Benedict-Bsl/SmartCap/Documents/US10445472.pdf

### US010445472B2

# ( 12 ) United States Patent

LeBrun

## ( 10 ) Patent No . : US 10 , 445 , 472 B2 ( 45 ) Date of Patent : Oct . 15 , 2019

### ( 54 ) SYSTEM AND METHOD FOR MONITORING

PILL CONTAINER ACTIVITY

( 56 ) | References Cited
U . S . PATENT DOCUMENTS
( 71 ) Applicant : PILLSY , INC . , Seattle , WA ( US ) | 5 , 751 , 661 A *

## ( 72 ) Inventor : Jeffrey R . LeBrun , Seattle , WA ( US )

## ( 73 ) Assignee : Pillsy , Inc . , Seattle , WA ( US )

6 , 518 , 523 B1
7 , 081 , 807 B2
7 , 446 , 272 B2
7 , 928 , 835 B1
8 , 092 , 224 B2
8 , 116 , 907 B2
5 / 1998 Walters | A61J 7 / 0409
221 / 2
2 / 2003 Chou
7 / 2006 Lai
11 / 2008 Chou
4 / 2011 Jovanov et al . 1 / 2012 Walker et al . 2 / 2012 Hyde et al .

( Continued )

( * ) Notice : Subject to any disclaimer , the term of this
patent is extended or adjusted under 35
U . S . C . 154 ( b ) by 742 days .
( 21 ) Appl . No . : 14 / 824 , 231 | FOREIGN PATENT DOCUMENTS
( 22 ) Filed : Aug . 12 , 2015 | WO
WO
2010078558 AL | 7 / 2010
2013120029 AL | 8 / 2013
( Continued ) ( 65 ) | Prior Publication Data
US 2016 / 0048657 A1 Feb . 18 , 2016 | OTHER PUBLICATIONS

## Related U . S . Application Data

( 60 ) Provisional application No . 62 / 036 , 272 , filed on Aug . 12 , 2014 .

PCT / US2018 / 040150 search report published WO2019 / 006212 dated Mar . 1 , 2019 .

### Primary Examiner — Hiep V Nguyen

( 51 ) | ( 74 ) Attorney , Agent , or Firm - Carrie M . Stroup

( 52 )

Int . Cl . G06F 19 / 00 | ( 2018 . 01 )
B65D 51 / 24 | ( 2006 . 01 )
B650 50 / 04 | ( 2006 . 01 )
A61J 1 / 14 | ( 2006 . 01 )
U . S . CI . CPC . . | G06F 19 / 3462 ( 2013 . 01 ) ; A61 ) 1 / 1412
( 2013 . 01 ) ; B650 50 / 043 ( 2013 . 01 ) ; B65D 51 / 24 ( 2013 . 01 ) ; B65D 51 / 248 ( 2013 . 01 ) ; GO6F 19 / 3418 ( 2013 . 01 ) ; A61J 2200 / 30 ( 2013 . 01 ) ; A61J 2200 / 74 ( 2013 . 01 ) Field of Classification Search
CPC | GO6F 19 / 3462 ; G06F 19 / 3456 ; A61J
1 / 1412 ; A61J 7 / 0472 ; A61J 7 / 0436 ; B65D 51 / 248 ; B65D 2101 / 0015 ; B65D 83 / 0409
USPC | | | 705 / 2
See application file for complete search history .
( 57 ) | ABSTRACT
A cap for a medication container includes a housing with a top portion and a bottom portion . The top and bottom portions together define a cavity therebetween . A sliding plate is disposed in the cavity adjacent the bottom portion . A microcontroller with a contact sensor is disposed in the

cavity between the top portion and the sliding plate . The
sliding plate is configured to slide toward and activate the
contact sensor where the cap is secured to the medication container in a closed state . The sliding plate is also config ured to slide away from and not activate the contact sensor where the cap is removed from the medication container in an open state .

( 58 )

21 Claims , 12 Drawing Sheets

501
Smart pill cap
Sensors | Micro
| controller
Wireless radio | Memory

Power
source | PCB

508
Remote computer
511 Wireless radio Memory

512 Power

source

Display
screen

User input interface ( touch screen or keyboard )

## US 10 , 445 , 472 B2

### Page 2

( 56 ) | | | References Cited
U . S . PATENT DOCUMENTS
8 , 362 , 914 B2 | 1 / 2013 Hyde et al . 8 , 666 , 926 B13 / 2014 Nease et al . 8 , 754 , 769 B2 | 6 / 2014 Stein et al . 2001 / 0028308 Al * 10 / 2001 De La Huerga . . A61M 5 / 14212

340 / 573 . 1
2002 / 0126585 Al * 9 / 2002 Osberg | A61J 7 / 0472
368 / 107
2003 / 0063522 AL | | | 4 / 2003 Sagar
2003 / 0069540 Al | 4 / 2003 Fowler et al . 2005 / 0047114 Al | 3 / 2005 Harrell et al .
2007 / 0171627 Al | | | 7 / 2007 Hsu
2007 / 0201220 A1 | | | 8 / 2007 Ulicny
2009 / 0134181 A1 | 5 / 2009 Wachman et al . 2010 / 0001812 A1 | 1 / 2010 Kausch
2010 / 0270257 Al 10 / 2010 Wachman et al . 2012 / 0029693 AL | 2 / 2012 Bear et al . 2014 / 0052468 A1 | 2 / 2014 Burrows et al . 2014 / 0108031 A1 | 4 / 2014 Ferrara
2014 / 0240094 AL | | | 8 / 2014 Stein et al . 2014 / 0300273 Al 10 / 2014 LeBrun et al .

FOREIGN PATENT DOCUMENTS
WO
WO
WO

2013127564 AL
2013158352 A1
WO2019006212 A1
| | | 9 / 2013
| | | 10 / 2013
| | | 1 / 2019
* cited by examiner

U . S . Patent | Oct . 15 , 2019 Sheet 1 of 12 | US 10 , 445 , 472 B2

103
101 | w | 104

105

106

102

# FIG . 1

U . S . Patent | Oct . 15 , 2019 | Sheet 2 of 12 | US 10 , 445 , 472 B2

101 .

Yrvacy | NO
wth | - 201

wa

Benim 203 -
IT S

AN
ITEMTIDUR Det ETT
am

208
209
207 _
01 | 202 4 + | 4 | + 4 | + 4 | + 4 + 4 *

AAL
? . . | XSATTA LE
written * * * * * * * * | : 11 * * * | ranti | F
. * | 206
211 | he

t

Whether

# FIG . 2

U . S . Patent | Oct . 15 , 2019 | Sheet 3 of 12 | US 10 , 445 , 472 B2

301

# FIG . 3A

302

w

ww | wwwwwwww
303 / | FIG . 3B

atent | Oct . 15 , 2019 | Sheet 4 of 12 | US 10 , 445 , 472 B2

Os 302
301 -

303

# FIG . 4

U . S . Patent | Oct . 15 , 2019 | Sheet 5 of 12 | US 10 , 445 , 472 B2

501

# \ Smart pill cap

Sensors | Micro
| controller

### Wireless

## radio Memory

WW

## Power

source

PCB

508

# Remote computer

- 511

### Wireless

## radio Memory

512
Power source | Display
| screen

### User input interface ( touch

## screen or keyboard )

# FIG . 5

U . S . Patent | Oct . 15 , 2019 Sheet 6 of 12 | US 10 , 445 , 472 B2

607

# Smart Pill Cap

# Additional remote

# computers ( e . g . caregiver smartphones or

# laptops )

603

# First Remote Computer

# ( e . g . smartphone )

# Internet

606 604
602

# Remote Servers

FIG . 6 | Storage

## ( databases )

## Processors

## ( controllers ) 605 -

atent | Oct . 15 , 2019 | Sheet 7 of 12 | US 10 , 445 , 472 B2

707

| 701
Smart Pill Cap | First remote computer ( e . g . User ' s computer , tablet or smartphone )

703

# Gateway

( e . g . cellular hub ) | Internet
708 | 704 | 706

# Servers Second remote

# computer ( operated by

# somebody other than

the user ) | Storage
| ( databases )

## Processors

### ( controllers ) 705

## FIG . 7

U . S . Patent atent | Oct . 15 , 2019 | Sheet 8 of 12 | US 10 , 445 , 472 B2

807

1801 Smart Pill Cap | User ' s smartphone

803

FIG . 8 | Internet

802
806

# Servers Caregiver or provider

## remote computers

( smartphones , laptops , etc . ) | Storage
| ( databases ) Processors

## ( controllers ) 805

atent | Oct . 15 , 2019 | Sheet 9 of 12 | US 10 , 445 , 472 B2
901 | 902

# PUBLIC GATEWAY

# Load balancing layer

App layer | Bastion layer

904

# PRIVATE GATEWAY

Database layer | .

_ W
905 | FIG . 9
906

tent | Oct . 15 , 2019 | Sheet 10 of 12 | US 10 , 445 , 472 B2
1001 | | Standby
1002 | Microcontroller on container receives sensor data indicating open / closed state
1003 | Sensor activity is recorded into memory with timestamp
1004 | Microcontroller sensor data log to smartphone via Bluetooth Low Energy , if they are paired or bonded and if there is a connection
1005 | Smartphone application sends pre - programmed reminders , unless the container activity is recorded and sent prior to the reminder time
1006 | Smartphone sends sensor data log to servers via cellular connection

# FIG . 10

U . S . Patent | Oct . 15 , 2019 | Sheet 11 of 12 | US 10 , 445 , 472 B2
1101 | User initiates refill action through sensor or switch located on the smart pill cap
1102 | Microcontroller on the smart pill cap interprets the sensed action to be a pill refill action
1103 | Microcontroller on the smart pill cap wirelessly sends a refill instruction to the smartphone or tablet application
1104 | Smartphone or tablet application sends a refill message to the web application API endpoint
1105 | Web application processes request and sends a refill message to the pharmacy ' s API endpoint

## 1106 _ Pharmacy API returns confirmation of successful refill to the

| web application API endpoint

1107 11077 Web application sends message to user ' s smartphone , confirming the successful refill action to the user ( optional )

# FIG . 11

nt | Oct . 15 , 2019 | Sheet 12 of 12 | US 10 , 445 , 472 B2

1205 000000000 1202

1203

1204 1204
. 1201

# FIG . 12

## US 10 , 445 , 472 B2

SYSTEM AND METHOD FOR MONITORING | | prescribed medications , and can transmit this information to
PILL CONTAINER ACTIVITY | | authorized individuals who can further assist patients in
managing their conditions . CROSS - REFERENCE TO RELATED | In one embodiment , a cap for a medication container
APPLICATIONS | | 5 includes a housing with a top portion and a bottom portion . The top portion and the bottom portion together define a
This application claims the benefit of U . S . Provisional | cavity therebetween . A sliding plate is disposed in the cavity Application No . 62 / 036 , 272 , filed on Aug . 12 , 2014 . The | adjacent the bottom portion . A microcontroller with a switch
entire disclosure of the above application is hereby incor | type contact sensor is disposed in the cavity between the top porated herein by reference . | portion and the sliding plate . The sliding plate is configured
to slide toward and activate the contact sensor where the cap FIELD | is secured to the medication container in a closed state . The
sliding plate is configured to slide away from and not The present disclosure relates to systems and methods for | activate the contact sensor where the cap is removed from increasing patient adherence to medication and nutrition 15 the medication container in an open state . regimens and , more particularly , to a smart pill cap for use
with standard prescription medicine containers . | | In another embodiment , a system for promoting adher
| | ence to a regimen by a patient includes the cap , and a first
BACKGROUND | | remote computer having a memory and a display . The first
| | 20 remote computer is in electronic communication with the
The statements in this section merely provide background | | cap . The first remote computer is configured to show on the
information related to the present disclosure and may not | | display information corresponding with the sliding plate
constitute prior art . | | pressing against and activating the contact sensor . The
Many people take medications , vitamins , and nutritional | | information is indicative of an opening and a closing of the
supplements on a regular basis as a way of life . However , a 25 medication container over time . common problem is that people forget to take their medi - | | In a further embodiment , a method for promoting adher
cations or other pills on a regular basis , or as they are | | ence to a regimen by a patient , includes the steps of
prescribed . Experts have estimated average medication | | providing the system with the cap and the first remote
adherence rates of 50 % to 60 % . According to the National | | computer , and maintaining the cap in a standby mode until
Community Pharmacists Association , this costs about 125 , 30 the cap senses a change in state from one of the open state
000 lives and $ 290 billion in the United States alone . While | | and the closed state . The cap is then caused to enter an active
there are several factors behind non - adherence , several mode for a predefined period of time . The cap is configured
studies have indicated that forgetfulness is a driving factor . | | to record the information from the contact sensor while in
In light of these facts , there is a continuing need for a cost | | the active mode . The microcontroller of the cap then creates
effective system and method of promoting patient adherence 35 a sensor data log of the information , and communicates the
to medication and nutrition regimens . Desirably , increasing | sensor data log to the first remote computer . rates of patient adherence will improve patient outcomes . | Further areas of applicability will become apparent from
saving patient lives and reducing preventative costs borne by | | the description provided herein . It should be understood that
the healthcare system and society . | | the description and specific examples are intended for pur 40 poses of illustration only and are not intended to limit the
SUMMARY | | scope of the present disclosure .
In concordance with the instant disclosure , a cost effective | | DRAWINGS
system and method of promoting patient adherence to medi
cation and nutrition regimens , which improves patient out - 45 | | The above , as well as other advantages of the present
comes , saves patient lives , and reduces preventative costs | | disclosure will become readily apparent to those skilled in
borne by the healthcare system and society , is surprisingly | | the art from the following detailed description when con
discovered . | | sidered in light of the accompanying drawings , in which :
The present disclosure provides a device and method to | | FIG . 1 is a perspective view of an assembly including a
assist people with managing either a ) their medications or b ) 50 smart pill cap attached to a prescription pill container , the medications of somebody whom they are caring for . In | | according to one embodiment of the disclosure ;
one embodiment of the disclosure , these medications are | | FIG . 2 is an exploded side elevational view of the
placed into a standard prescription pill container that is | | assembly of FIG . 1 ;
labeled and filled by a pharmacist . The standard prescription | | FIG . 3A is an enlarged side elevational view of the
pill vial has a smart pill cap . Information about the medi - 55 threaded smart pill cap of FIG . 1 , shown without the
cation , including the medication schedule , are programmed | | prescription pill container ;
into a software application that connects to the smart pill cap | | FIG . 3B is an enlarged bottom perspective view of the
attached to the pill container . The smart pill cap detects | | threaded smart pill cap shown in FIG . 3A ;
interactions with the pill container , including when it is | | FIG . 4 is an enlarged bottom perspective view of a smart
opened and closed , and sends this information wirelessly to 60 pill cap according to another embodiment of the disclosure , a remote computer . The remote computer can remind the | | wherein the smart pill cap is childproof ;
user to take their medications when they forget . The remote | | FIG . 5 is a schematic diagram illustrating an example
computer can also send the user ' s medication adherence data | | communication relationship between the smart pill cap and
to a remote server , where it may be shared with family | | pill container of FIG . 1 and a smartphone application ;
members or their healthcare providers . The system can 65 | | FIG . 6 is a schematic diagram illustrating an example of
remind patients when to take their medications , provide | | one network architecture between the smart pill cap , and
information about the medications , monitor adherence to the | | remote servers that store the web application ;

## US 10 , 445 , 472 B2

15

FIG . 7 is a schematic diagram illustrating an example | | | board 203 . Although the top portion 201 and the bottom
network architecture where the smart pill cap sends a | portion 202 are described further herein as being distinct top wireless signal to a cellular gateway , which relays medica - and bottom pieces , separately formed and subsequently tion adherence information to remote servers through the | attached to one another , it should be appreciated that the top Internet , which then routes medication adherence data to 5 portion 201 and the bottom portion 202 may also be formed
devices used by the patient and members of their care team ; | integrally as a single or unitary one - piece body , as desired . FIG . 8 is a schematic diagram illustrating an example | The printed circuit board contains a switch type sensor network architecture according to another embodiment of | 204 , a wireless radio , memory , a speaker , and other elec
the disclosure ; | tronic components . A sliding plate 204 is also encased by the FIG . 9 is a particular embodiment of a data structure for 10 top piece 201 of the housing and the bottom piece 202 of the preserving securing within the remote servers ; | housing . The sliding plate 204 presses down the switch type FIG . 10 is a flow diagram illustrating a method for sharing | sensor 205 when the pill container 211 is attached to the information from the smart pill cap to a remote server
through an intermediary remote computer , according to one | | | smart pill cap 101 by tightening the threads 206 on the
5 container with the threads 207 internal to the smart pill cap . embodiment of the disclosure ;
FIG . 11 is a flow diagram illustrating a method for | | | A silicone band 208 may be placed on the outside of the
initiating a prescription refill through the smart pill cap . | | | assembled smart pill cap 101 . The silicone band 208 may fit
according to another embodiment of the disclosure ; and | | | into a groove 209 that permits a flush fitting within the side
FIG . 12 is schematic illustration of a smart pill cap that is | | | of the smart pill cap 101 . The silicone band 208 may cover
capable of sensing and calculating the weight of the contents 20 up screw holes 210 that are used to attach the top piece 201
of the attached pill vial . | | | and the bottom piece 202 of the smart pill cap 101 . FIGS . 3A and 3B illustrate alternative views of the smart
DETAILED DESCRIPTION | | | pill cap 101 that is designed to fit with a “ 1 - click ” pill container . A thread 302 secures the smart pill cap to the pill The following description is merely exemplary in nature 25 container , with a rectangular block of plastic 303 that is
and is not intended to limit the present disclosure , applica - | | | incorporated into the smart pill cap 301 securing the 1 - click
tion , or uses . It should be understood that throughout the | | | mechanism that is built into the pill container . This ensures
drawings , corresponding reference numerals indicate like or | | | that the smart pill cap 301 remains securely fastened to the
corresponding parts and features . | | | pill cap until the user presses the 1 - click release mechanism
FIG . 1 illustrates a smart pill cap 101 that is capable of 30 on the container and twists the smart pill cap 301 to remove
being removably coupled to a pill container 102 , such as a | it . vial . The smart pill cap 101 contains an internal switch - type | FIG . 4 illustrates a further alternative version of the smart
contact sensor for detecting whether or not it is coupled to | | | pill cap 101 that is designed to integrate with a childproof
the container 102 , thereby detecting whether the container is | | | pill container . In this embodiment , rectangular blocks of
opened or closed . This information is stored in local memory 35 plastic 301 are integrated to the smart pill cap that fit with
that is also internal to the cap . As used herein , the term | | | plastic “ hooks ” that are included on the external portion of
“ memory ” may include a non - transitory and tangible com - | | | a childproof pill container when the smart pill cap is pushed
puter - readable storage medium , on which databases and | | | onto the childproof pill container . The sliding plate 302
processor - executable software code may be embodied . The | | | selectively activates , for example , by pressing against , the
smart pill cap 101 transmits the information to an external 40 switch type contact sensor when the container is attached to
computer or gateway via a wireless radio connection . Audio | | | the smart pill cap . A ridge 303 is included on the sliding plate
reminders may be emitted from a speaker internal to the | | | 302 in order to maintain a tight seal with the mouth of the
smart pill cap 101 , which are configured to occur when the | | | pill container .
user does not open the container on a pre - scheduled basis . | | | FIG . 5 illustrates a medication adherence system com
In a particular embodiment , a top plate 103 is incorpo - 45 prising a smart pill cap 501 , also described hereinabove and
rated into the smart pill cap 101 that can be removed in order | | | shown in FIGS . 1 and 2 as reference number 101 , that
to expose a coin cell style battery . A gap 104 between the top | | | transmits information that is sensed by the switch - based
plate 103 and the primary container body 105 permits the top | sensor 502 to a remote computer 508 , such as a smartphone , plate 103 to be removed via a prying action , as well as | tablet computer , or laptop computer , by transmitting infor
permits sound emitted by the internal speaker to be heard by 50 mation digitally from the smart pill cap ' s wireless radio 503
the user . | to the wireless radio contained in the remote computer 508 . A silicone band 106 provides an improved grip on the | The smart pill cap stores data in local memory 506 that is
smart pill cap while concealing a seam between the top and | | | transmitted whenever the smart pill cap 501 and remote
bottom portions of the smart pill cap assembly . The silicone | | | computer 508 are connected and are in range . A power
band 106 may also be colored in a way that the user 55 source 504 such as a lithium or lithium - ion battery is
associates it with the display of one of their medications in | | | contained inside the smart pill cap and components are
the accompanying software of the smart pill cap 101 . | connected via a printed circuit board ( PCB ) 507 . The smart pill cap 101 can be placed on a prescription or | The remote computer receives has the capability to store
over - the - counter pill container in order to track medication | | | data from the smart pill cap in local memory 511 . The
usage and adherence . The container 102 may be filled by a 60 remote computer also contains an onboard power 510
pharmacist , drug manufacturer , drug distributor , or whole - | | | source , such as a lithium ion battery . Most importantly the
sale provider . | | | remote computer serves as the user ' s primary means of
FIG . 2 illustrates a sub - assembly of the smart pill cap 101 | | | viewing data that is collected by the smart pill cap , with the
and integration with the pill container 102 , according to one | | | user of the smart pill cap having the ability to view said data
embodiment of the disclosure . A top portion 201 of the smart 65 on the display screen 512 of the remote computer 512 as
pill cap housing is securely attached to a bottom portion 202 | | | well as to input data that can be sent from the remote
of the smart pill cap housing , encasing a printed circuit | | | computer 508 to the smart pill cap 501 , such as a schedule view

## US 10 , 445 , 472 B2

of times when the user is supposed to take the medications | | | number 101 , sends data directly to remote servers 804
contained by the smart pill cap 501 and the pill container that | | | through a cellular data connection without passing data
it is mated to . | | | through an intermediate hub or remote computer , such as
FIG . 6 illustrates a medication adherence network archi - | | | those that were described in FIG . 6 and FIG . 7 . In this case , tecture comprising the system described in FIG . 5 . The 5 the remote servers 804 may relay data collected by sensors
remote computer 602 sends information received from the | | | in the smart pill cap 801 to the user ' s remote computer , or
smart pill cap 601 , also described hereinabove and shown in | to remote computers operated by people other than the user . FIGS . 1 and 2 as reference number 101 , to a remote server | The cellular connection used in this architecture may be
604 through the Internet 603 . The remote servers having | GSM , CDMA , LTE or another network type . storage 605 and processing capabilities 606 . | 10 | FIG . 9 illustrates an architecture for securely storing data
Data related to the user ' s medication adherence may be | | | collected by the smart pill cap described in FIG . 1 on a
stored in the smart pill cap , the remote computer , and on the | | | remote server . Requests to a first remote server come in
remote server , with data periodically synced across all three | | | through a public gateway 901 , with requests being routed to
locations . Medication adherence data stored on the smart pill | | | a second remote server through the load balancing layer 902 . cap may be deleted after a specified number of events in 15 This helps to ensure maximum responsiveness and uptime
order to free up additional memory , preferably after data is | | | by distributing the computational load among a network of
pushed to the remote computer or remote servers . Informa | | | servers . Requests are routed to the app layer 903 of a web
tion may also be sent from the remote servers to the user ' s | | | application or API that is designed specifically to be com
remote computer . For example , information may be sent to | | | plimentary to the smart pill cap device described in FIG . 1 . the user ' s smartphone related to pricing at various pharma - 20 This app layer 903 can may requests to database layer 906
cies where they can refill their medications . | | | only through a private gateway 905 . By limiting extraction
Optionally , a portion of the data captured by the smart pill | | | of data from the database layer to a small subset of known
cap may be shared from the remote servers to additional | | | servers , this helps to ensure security of the medication
remote computers 607 that are managed by remote caregiv | | | adherence data . All data stored in the server is also encrypted
ers , care managers , family members , or healthcare profes - 25 and servers are kept in locations that are physically secure . sionals ( doctors , nurses , physician ' s assistants , etc . ) . This | | | A bastion layer 904 running on one or more servers receives
sharing is likely to be executed via an application program - | requests from protected areas of the network and is desig ming interface ( API ) that is made available to users that have | nated with specific responsibilities , such as security privi
1 ) received permission from the owner of the smart pill cap | | | leges and access privileges . and first remote computer 2 ) have proven their credentials to 30 FIG . 10 illustrates a method for recording medication
the API through an authentication method , such as OAuth , | | | adherence data into memory located in a smart pill cap and
a known open standard for authorization , or a token - based | | | sending that information to remote servers via a smartphone
authentication method . This capability provides additional | | | intermediary . The smart pill cap will remain in standby
users to see information that can help them to care for the mode 1001 until it senses a change to opened / closed state , user , such as to intervene when the user has deviated from 35 at which point it will enter " active mode ” for a predefined their medication schedule . Moreover , the API enables 3rd | | | period of time . Standby mode may be designed to conserve
party solution providers to write custom software applica | | | power by reducing the advertising interval frequency by the
tions that combine data from the smart pill cap with data | | | wireless radio . Once sensor data is detected 1002 it will be
from other sources . For example , the additional remote | | | recorded into memory 1003 located on the smart pill cap . computers may combine data from the smart pill cap with 40 When the smart pill cap connects to a smartphone that it is
data from a wireless scale or a wireless blood pressure | | | paired to , it sends the data log to a complimentary applica
monitor to determine if the user has a high degree of risk of | | | tion running on the smartphone 1004 . The smartphone is
heart attack due to the user ' s deviation from their prescribed | | | pre - programmed to send medication reminders to the user
medication regimen . | | | unless it receives data from the smart pill container indicat
FIG . 7 illustrates a medication adherence system whereby 45 ing that the smart pill container has been opened within a
the smart pill cap 701 , also described hereinabove and | | | time interval designated to be associated with the scheduled
shown in FIGS . 1 and 2 as reference number 101 , sends data | | | medication event 1005 . The smartphone also sends the
related to a user ' s medication adherence to a wireless hub | | | sensor data log over the Internet using a cellular , WiFi , or
702 that is located within a close proximity ( less than 2000 | other wireless connection 1006 . feet ) that subsequently relays the data to remote servers 704 . 50 | FIG . 11 illustrates a method for initiating a refill of a
The remote servers are able to send the medication adher - | | | prescription medication , vitamin , or over - the - counter medi
ence data transmitted originally from the smart pill cap 701 | cation by interacting directly with the smart pill container . to at least one of the user ' s smartphone 707 or to remote | The user initiates the refill action by initiating the sensor
computers 708 being operated by the user ' s caregiver , | | | located inside of the smart pill cap 1101 using a pre - defined
family member or a healthcare professional . This represents 55 action , such as pressing the sliding plate two or three times
a different network architecture that requires an additional | | | quickly , or by tapping the container on the table . The
intermediate gateway device 702 that is not required in the microcontroller within the smart pill cap interprets the
architecture described in FIG . 6 . However this architecture | sensed action to be a pill refill action 1102 , and sends a pill does not require the user to own a smartphone or other | refill request to the user ' s remote computer ( e . g . smart

device . In this case , the gateway 702 may also receive data 60 phone ) during the next session when the two devices com
sent by additional remote monitoring devices , such as wire - | | | municate wireless 1103 . The remote computer relays this
less scales , blood pressure monitors , glucose monitors , | refill message to a web application ' s API endpoint 1104 , motion sensors or other devices , most likely by using a | with the web application relating the refill request to a
wireless connection . | | | specific medication known to be taken by the user . The web
FIG . 8 illustrates a medication adherence network archi - 65 application converts this into a refill request that can be send
tecture whereby the smart pill cap 801 , also described | | | to a pharmacy ' s API endpoint 1105 , including information
hereinabove and shown in FIGS . 1 and 2 as reference | | | the pharmacy can use to identify the specific prescription

## US 10 , 445 , 472 B2

such as the Rx number , store ID , and possibly some infor - | What is claimed is :
mation used to identify the individual ( name , social security | 1 . An electronic sensing cap for a pill container , compris number , phone number , etc . ) . Optionally this request may be | ing :
routed through one or more intermediate APIS , such as an | a housing with a top portion and a bottom portion and
ePrescription web service , prior to being routed to the 5 | defining a cavity therebetween ;
pharmacy . At this point the pharmacy has received infor | a sliding plate disposed in the cavity adjacent to the
mation instructing them to refill the prescription , which may | bottom portion ;
help them comply with regulations requiring user - initiated | a microcontroller with a switch type contact sensor dis
posed in the cavity between the top portion and the actions to refill prescriptions . Optionally , the pharmacy API | sliding plate , the sliding plate configured to slide may return confirmation to the original web service that the prescription was successfully received 1106 , with the web | upward and activate the contact sensor where the cap is
secured to the pill container in a closed state , and the application relaying that message to the user ' s remote com | sliding plate configured to slide downward from and puter 1107 through a mobile application that is also capable | not activate the contact sensor where the cap is of communicating with the smart pill container . The phar - 15 | removed from the pill container in an open state ;
macy ' s API may send additional messages to the user to | wherein the microcontroller further comprises a printed provide updates on the status of the prescription refill , such | circuit board that comprises a non - infrared wireless
as indication of when it is ready to be shipped or picked up . | radio , a memory , a speaker , and wherein a battery is
FIG . 12 illustrates a method for integrating a method for | connected to the printed circuit board that is powered at
detecting weight into the smart pill cap . In order to use this 20 | least in part in both the opened state and the closed
design , the smart cap and pill must be placed upside - down , | state ; and
with the contents of the pill container resting on the smart | wherein the microcontroller is configured to non - infra
pill cap in an attached position . The weight of the pills | redly , wirelessly transmit information indicative of an
presses on the sliding plate internal to the smart pill cap , for | opening and a closing of the pill container over time to
example , the sliding plate 204 described hereinabove . The 25 | at least one of a smartphone or a tablet computer and / or
sliding plate rests on a spring 1204 ; this spring can be the | a cellular gateway device . spring included in the sensor switch . | 2 . The cap of claim 1 , wherein the microcontroller is
As shown in FIG . 12 , a capacitor is created through two | configured to store in the memory information correspond
metallic plates , the first plate 1201 of which is attached to the | ing with the sliding plate pressing up against the switch type
printed circuit board . The second metallic plate is integrated 30 contact sensor , the information indicative of an opening and
into the sliding plate , and may consist of a sliding plate that | a closing of the medication container over time . is coated in a metallic material on the side of the plate that | 3 . The cap of claim 1 , wherein the microcontroller is
is not in contact with the contents of the pill container . The | configured to cause the speaker to emit an audio reminder
sliding plate may move between a first position 1202 when | according to a predetermined schedule . the contents of the container are empty , and a second 35 4 . The cap of claim 1 , wherein the bottom portion of the
position 1203 when the contents of the container are full and | housing has internal threads configured to cooperate with
there is a greater force imposed on the plate . Capacitance is | external threads of the container , and at least one rectangular
sensed by the printed circuit board and correlated to a | block of plastic beneath the internal threads , configured to
measured distance , based on previous empirical experimen - | securely fasten the pill cap to the container until the user
tation . A weight is calculated based on Hooke ' s law , which 40 presses down on the cap in a one - click action and twists the
holds that the displacement of a spring is proportional to the | cap to remove it from the container . weight and the spring constant . The spring 1204 in the | 5 . The cap of claim 1 , wherein the top portion of the
pushbutton may be used to provide the resistive force to the | housing has a removable top plate that permits access to the
weight of the pills 1205 that are resting on the sliding plate | cavity and the battery upon removal . 1201 . Calibration is required to correlate weight to capaci - 45 6 . The cap of claim 1 , further comprising a band disposed
tance , which may be measured by creating a delay line | on an outer perimeter of the cap , flush to a cap side , covering consisting of the capacitive sensor and a large resistor | a seam between the top portion and the bottom portion , and
( ~ 10M Ohm ) . | colored to associate with a specific pill . In another embodiment , the pushbutton itself is used as a | 7 . The cap of claim 6 , wherein the top portion is a top capacitive weight sensor . | 50 piece and the bottom portion is a bottom piece , the top piece
In yet another embodiment , a load sensor is used that is | formed separately from the bottom piece , the top piece
attached to the printed circuit board . | affixed to the bottom piece to form the housing , and at least
In a further embodiment , scattered light is used to mea - | one of the top piece and the bottom piece defines a groove
sure the distance between the PCB and the sliding plate . An | on an outer surface thereof , the groove extending around an
infrared LED and complementary photoreceiver are placed 55 entirety of the cap , the band disposed in the groove . in proximity on the side of the printed circuit board that is | 8 . The cap of claim 1 , wherein the microcontroller further
facing the sliding plate . Scattering from the sliding plate | includes a sensor configured to measure a weight of contents
results in reflections of a portion of the illuminated light onto | of the container where the container is turned upside down . the photoreceiver , with the intensity of the light being | 9 . The electronic sensing cap of claim 1 , wherein a cap

proportional to the distance between the two plates . This 60 data is able to be wirelessly synced from one of the cellular
illumination is best enabled in short bursts or on command | enabled remote computers and / or the cellular gateway
in order to conserve energy . | device through an internet to a remote server , and the remote
From the foregoing description , one ordinarily skilled in | server is configured to receive the data through an applica
the art can easily ascertain the essential characteristics of | tion program interface ( API ) , store an encrypted data in the
this disclosure and , without departing from the spirit and 65 memory , and process the encrypted data on a central web
scope thereof , make various changes and modifications to | application , the API first checking for an authorization and
the disclosure to adapt it to various usages and conditions . | a credential prior to granting access ; and wherein the data is

## US 10 , 445 , 472 B2

10

ma

synced from a central web application to a second web | | | | | tion , and a microcontroller with a switch type contact
application that is run by a healthcare provider and / or by a | | | | | sensor disposed in the cavity between the top portion
secure web - based API . | | | | | and the sliding plate , the sliding plate configured to
10 . The electronic sensing cap of claim 1 , wherein the | | | | | slide upward and activate the contact sensor where the
microprocessor within the cap , is programmed to remain in 5 | | | | | cap is secured to the pill container in a closed state , and
a first low energy standby mode until the switch type contact | | | | | the sliding plate configured to slide downward and not
sensor is activated , upon which the microprocessor enters a | | | | | activate the contact sensor where the cap is removed
second high energy active mode for a predefined period of | from the pill container in an open state , time . | wherein the microcontroller further comprises a printed
11 . The electronic sensing cap of claim 1 , wherein the 10 | | | | | circuit board that comprises a non - infrared wireless
microprocessor within the cap is programmed to schedule | | | | | radio , a memory , a speaker , and a battery connected
transmission of a wireless data on a regularly scheduled | | | | | to the printed circuit board that is powered at least in
basis regardless of the contact sensor input , and varies one | | | | | part in both the opened state and the closed state ;
of a transmission power , or a reduced wireless radio adver | | | | | and
tising interval frequency , in response to a data that is 15 | a first remote computer having a memory and a display , received by the contact sensor . | the first remote computer in non - infrared wireless
12 . A system for promoting adherence to a regimen by a | electronic communication with the cap and config patient , comprising : | ured to show on a display information corresponding
a cap for a pill container , including a housing with a top | with the sliding plate activating the contact sensor , portion and a bottom portion and defining a cavity 20 | the information indicative of an opening and a clos
therebetween , a sliding plate disposed in the cavity | | | | | ing of the pill container over time , wherein the first
adjacent to the bottom portion , and a microcontroller | | | | | remote computer is a smartphone or a tablet com
with a switch type contact sensor disposed in the cavity | | | | | puter ;
between the top portion and the sliding plate , the | | | | | maintaining the cap in a standby mode until the cap senses
sliding plate configured to slide upward and activate the 25 | | | | | a change in state from one of the open state and the
contact sensor where the cap is secured to the pill | | | | | closed state ;
container in a closed state , and the sliding plate con | | | | | causing the cap to enter an active mode , the cap config
figured to slide downward and not activate the contact | | | | | ured to record the information from the contact sensor
sensor where the cap is removed from the pill container | | | | | in the active mode ;
in an open state ; wherein the microcontroller further 30 | | | | | creating by the microcontroller of the cap a sensor data
comprises a printed circuit board that comprises a | | | | | log of the information ; and
non - infrared wireless radio , a memory , a speaker , and | | | | | communicating non - infrared wirelessly from the micro
a battery connected to the printed circuit board that is | | | | | controller of the cap to the first remote computer the
powered at least in part in both the opened state and the | sensor data log . closed state ; | 35 | 19 . The method of claim 18 , further comprising the step
and | | | | | of sending non - infrared wirelessly pill reminders to the
a first remote computer having a memory and a display , | | | | | patient by the first remote computer unless the first remote
the first remote computer in non - infrared wireless elec | | | | | computer receives information from the cap indicating that
tronic communication with the cap and configured to | | | | | the container has been in the open state within a time interval
show on the display information corresponding with 40 designated to be associated with a scheduled pill event . the sliding plate activating the switch type contact | | | | | 20 . The method of claim 18 , further comprising the steps
sensor , the information indicative of an opening and a | of , closing of the pill container over time . | initiating a refill action by a pre - defined action on the cap 13 . The system of claim 12 , wherein the first remote | by a user , the predefined action comprising , pressing computer is one of a personal computer , a tablet , and a 45 | the sliding plate two or three times quickly , or by smartphone of the patient . | tapping the pill container on the table , the microcon
14 . The system of claim 13 , wherein the smartphone or | | troller detecting the predefined action and causing the
tablet is pre - programmed to send pill reminders to the | | microcontroller to non - infrared wirelessly send a refill
patient , unless the smartphone or tablet non - infrared wire | | request to the first remote computer ;
lessly receives data from the pill container indicating that the 50 relaying the refill request wirelessly by the first remote
pill container has been opened within a time interval des | | computer to a second remote computer through an API
ignated to be associated with a scheduled pill event . | | endpoint with a web application ;
15 . The system of claim 12 , further comprising a cellular | | relaying the refill request wirelessly by the web applica
gateway in non - infrared wireless communication with both | | tion to a pharmacy computer running a pharmacy
the cap and the first remote computer . | 55 | application , wherein the refill request comprises infor
16 . The system of claim 12 , further comprising a second | | mation to identify the prescription and patient ;
remote computer in non - infrared wireless communication | | relaying a confirmation message from the pharmacy
with the first remote computer over the Internet . | | application to the web application API endpoint ; and
17 . The system of claim 16 , wherein the second remote | | the web application processing a successful refill confir
computer provides access to the information to one of a 60 | mation and wirelessly sending a message to the first
caregiver and a provider of the patient . | | remote computer confirming a successful refill action
18 . A method for promoting adherence to a regimen by a | by the pharmacy computer . patient , the method comprising the steps of : | 21 . A method for ordering a refill of a vitamin or a
providing a system including a cap for a pill container , the medication in a pill container , comprising :
cap having a housing with a top portion and a bottom 65 | providing a system with a wireless network connecting a
portion and defining a cavity therebetween , a sliding | | cap for a pill container , a first remote computer , a
plate disposed in the cavity adjacent the bottom por | | second remote computer with a refill request web

## US 10 , 445 , 472 B2

12
application installed thereon , and a remote pharmacy computer , the cap including a housing with a top
portion and a bottom portion and defining a cavity therebetween , a sliding plate disposed in the cavity adjacent to the bottom portion , and a microcontroller 5

with a switch type contact sensor disposed in the cavity between the top portion and the sliding plate , the sliding plate configured to slide upward and activate the contact sensor ;
wherein and the microcontroller further comprises a 10 printed circuit board that comprises a non - infrared wireless radio , a memory , a speaker , and a battery connected to the printed circuit board that is powered at least part in both the opened stated and the closed
state ;
a first remote computer comprising a user ' s personal computer , a tablet , or a smartphone , having a memory and a display , and in non - infrared wireless electronic communication with the cap and configured to show on the display information corresponding to a refill 20 request ;
initiating a refill action by a pre - defined action on the cap by the user , the predefined action comprising pressing

the sliding plate two or three times quickly , or by tapping the pill container on the table , and causing the
microcontroller to non - infrared wirelessly send a refill request to the first remote computer ;
relaying the refill request wirelessly by the first remote computer to a second remote computer with a refill
request web application installed thereon , wherein the web application refill request comprises information to identify the prescription and a patient , comprising at
least one of , a prescription number , a store identifica
tion , and / or a patient identification information ;
relaying the refill request wirelessly by the second remote computer web application to a pharmacy computer , wherein the refill request comprises the information to

identify the prescription and the patient ;
transmitting a confirmation of a refill completion wire

### lessly by the pharmacy computer to the second remote

computer web application ; and
transmitting the confirmation of the refill completion wirelessly by the second remote computer web appli cation to the first remote computer .

15
