Benedict-Bsl/SmartCap/Documents/US20160048657A1.pdf

## (19) United States

# (12) Patent Application Publication (10) Pub. No.: US 2016/0048657 A1

US 201600.48657A1

LeBrun et al. | (43) Pub. Date: | Feb. 18, 2016
(54) SYSTEMAND METHOD FORMONITORING | B65D 5L/24 | (2006.01)
PLL CONTAINERACTIVITY | B65D 4L/04 | (2006.01)
(52) U.S. Cl.
(71) Applicant: PILLSY, INC., Seattle, WA (US) | CPC ........ G06F 19/3462 (2013.01); G06F 19/3418
(2013.01); B65D 41/04 (2013.01); B65D 43/20 (72) Inventors: Jeffrey R. LeBrun, Seattle, WA (US); | (2013.01); B65D 5L/245 (2013.01); B65D
David McIntosh, Wilsonville, OR (US) | 5 1/248 (2013.01)
(21) Appl. No.: 14/824,231 | (57) | ABSTRACT
(22) Filed: | Aug. 12, 2015 | A cap for a medication container includes a housing with atop
O O | portion and a bottom portion. The top and bottom portions Related U.S. Application Data | together define a cavity therebetween. A sliding plate is dis
(60) Provisional application No. 62/036,272, filed on Aug. | posed in the cavity adjacent the bottom portion. A microcon
12, 2014. | troller with a contact sensor is disposed in the cavity between
the top portion and the sliding plate. The sliding plate is
Publication Classification | configured to slide toward and activate the contact sensor
where the cap is secured to the medication container in a
(51) Int. Cl. | closed State. The sliding plate is also configured to slide away
G06F 9/00 | (2006.01) | from and not activate the contact sensor where the cap is
B65D 43/20 | (2006.01) | removed from the medication container in an open state.

101
Y

205

210

2O2

Patent Application Publication | Feb. 18, 2016 Sheet 1 of 12 | US 2016/0048657 A1

## FIG. 1

Patent Application Publication | Feb. 18, 2016 Sheet 2 of 12 | US 2016/0048657 A1

101

2O3

2O6

Patent Application Publication | Feb. 18, 2016 Sheet 3 of 12 | US 2016/0048657 A1

301

## FIG. 3A

302

303

Patent Application Publication | Feb. 18, 2016 Sheet 4 of 12 | US 2016/0048657 A1

3O2
301

303

## FIG. 4

Patent Application Publication | Feb. 18, 2016 Sheet 5 of 12 | US 2016/0048657 A1

501

## Smart pill cap

502 | 505

Micro
Controller Sensors
503 | 506
Wireless
radio

SOCC

Memory

508 | N-1

## Remote computer

509 | 511
Wireless
radio
510 | 512 Display
SOUCe | SCee

User input interface (touch Screen or keyboard)

## FIG. 5

POWer

513

Patent Application Publication | Feb. 18, 2016 Sheet 6 of 12 | US 2016/0048657 A1
601 | Additional remote

## Computers

# (e.g. Caregiver Smartphones or

# laptops)

# Smart Pill Cap

## First Remote

# Computer

# (e.g. Smartphone)

## Remote Servers

## FIG. 6

Processors

### (controllers)

Storage

### (databases) 605

Patent Application Publication | Feb. 18, 2016 Sheet 7 of 12 | US 2016/0048657 A1

707

701

## First remote computer

(e.g. User's Computer,

## tablet or smartphone)

# Smart Pill Cap

702

# Gateway

# (e.g. cellular hub)

706

### Second remote

## Computer (operated by

## somebody other than

the user) | Processors

### (controllers)

Storage

### (databases)

## FIG. 7

Patent Application Publication | Feb. 18, 2016 Sheet 8 of 12 | US 2016/0048657 A1

807

801
Smart Pill Cap | User's Smartphone

## FIG. 8

802
YN

## Caregiver or provider

## remote computers

(Smartphones,

## laptops, etc.)

806

Processors

### (controllers)

Storage

### (databases)

Patent Application Publication | Feb. 18, 2016 Sheet 9 of 12 | US 2016/0048657 A1
901 | 902

## PUBLIC GATEWAY

## Load balancing layer

App layer | Bastion layer

# PRIVATE GATEWAY

## Database layer

905 | FIG. 9
906

Patent Application Publication | Feb. 18, 2016 Sheet 10 of 12 | US 2016/0048,657 A1
1001 N-N | Standby
1002 | Microcontroller on container receives sensor

## data indicating open/closed State

1003 | Sensor activity is recorded into memory with timestamp
1004 | Microcontroller Sensor data log to Smartphone via Bluetooth Low Energy, if they are paired or bonded and if there is a connection
1005 | Smartphone application sends pre-programmed reminders, unless the container activity is recorded and sent prior to the reminder time
1006 | Smartphone sends sensor data log to Servers via cellular connection

## FIG. 10

Patent Application Publication | Feb. 18, 2016 Sheet 11 of 12 | US 2016/0048657 A1

## User initiates refill action through sensor or switch located on

## the smart pill cap 1 101

1102 | Microcontroller on the smart pill cap interprets the sensed action to be a pill refill action
| Microcontroller on the smart pill cap wirelessly sends a refill instruction to the smartphone or tablet application
| Smartphone or tablet application sends a refill message to the web application API endpoint

1103

1104

## Web application processes request and sends a refill message to the pharmacy's API endpoint

V

## Pharmacy API returns confirmation of successful refill to the Web application AP endpoint

1105

1106

Web application sends message to user's Smartphone,

## confirming the successful refill action to the user (optional) 1107

## FIG. 11

Patent Application Publication | Feb. 18, 2016 Sheet 12 of 12 | US 2016/0048657 A1

# 120s --OOOOOOO

## FIG. 12

US 2016/0048,657 A1

SYSTEMAND METHOD FORMONITORING PLL CONTAINERACTIVITY

CROSS-REFERENCE TO RELATED APPLICATIONS
0001. This application claims the benefit of U.S. Provi sional Application No. 62/036,272, filed on Aug. 12, 2014. The entire disclosure of the above application is hereby incor porated herein by reference.

FIELD
0002 The present disclosure relates to systems and meth ods for increasing patient adherence to medication and nutri tion regimens and, more particularly, to a Smart pill cap for use with standard prescription medicine containers.

BACKGROUND
0003. The statements in this section merely provide back ground information related to the present disclosure and may not constitute prior art.
0004. Many people take medications, vitamins, and nutri tional Supplements on a regular basis as a way of life. How ever, a common problem is that people forget to take their medications or other pills on a regular basis, or as they are prescribed. Experts have estimated average medication adherence rates of 50% to 60%. According to the National Community Pharmacists Association, this costs about 125, 000 lives and S290 billion in the United States alone. While there are several factors behind non-adherence, several stud ies have indicated that forgetfulness is a driving factor. 0005. In light of these facts, there is a continuing need for a cost effective system and method of promoting patient adherence to medication and nutrition regimens. Desirably, increasing rates of patient adherence will improve patient outcomes, saving patient lives and reducing preventative costs borne by the healthcare system and Society.

SUMMARY
0006. In concordance with the instant disclosure, a cost effective system and method of promoting patient adherence to medication and nutrition regimens, which improves patient outcomes, saves patient lives, and reduces preventative costs borne by the healthcare system and Society, is Surprisingly
discovered.
0007. The present disclosure provides a device and method to assist people with managing either a) their medi cations or b) the medications of somebody whom they are caring for. In one embodiment of the disclosure, these medi cations are placed into a standard prescription pill container that is labeled and filled by a pharmacist. The standard pre Scription pill vial has a Smart pill cap. Information about the medication, including the medication schedule, are pro grammed into a software application that connects to the Smart pill cap attached to the pill container. The Smart pill cap detects interactions with the pill container, including when it is opened and closed, and sends this information wirelessly to a remote computer. The remote computer can remind the user to take their medications when they forget. The remote com puter can also send the user's medication adherence data to a remote server, where it may be shared with family members or their healthcare providers. The system can remind patients when to take their medications, provide information about the medications, monitor adherence to the prescribed medica

### Feb. 18, 2016

tions, and can transmit this information to authorized indi viduals who can further assist patients in managing their
conditions.
0008. In one embodiment, a cap for a medication container includes a housing with a top portion and a bottom portion. The top portion and the bottom portion together define a cavity therebetween. A sliding plate is disposed in the cavity adjacent the bottom portion. A microcontroller with a switch type contact sensor is disposed in the cavity between the top portion and the sliding plate. The sliding plate is configured to slide toward and activate the contact sensor where the cap is
secured to the medication container in a closed State. The
sliding plate is configured to slide away from and not activate the contact sensor where the cap is removed from the medi cation container in an open state.
0009. In another embodiment, a system for promoting adherence to a regimen by a patient includes the cap, and a first remote computer having a memory and a display. The first remote computeris in electronic communication with the cap. The first remote computer is configured to show on the display information corresponding with the sliding plate pressing against and activating the contact sensor. The infor mation is indicative of an opening and a closing of the medi
cation container over time.
0010. In a further embodiment, a method for promoting adherence to a regimen by a patient, includes the steps of providing the system with the cap and the first remote com puter, and maintaining the cap in a standby mode until the cap senses a change in state from one of the open state and the closed State. The cap is then caused to enteran active mode for a predefined period of time. The cap is configured to record
the information from the contact sensor while in the active
mode. The microcontroller of the cap then creates a sensor datalog of the information, and communicates the sensor data log to the first remote computer.
0011 Further areas of applicability will become apparent from the description provided herein. It should be understood that the description and specific examples are intended for purposes of illustration only and are not intended to limit the Scope of the present disclosure.

DRAWINGS
0012. The above, as well as other advantages of the present disclosure will become readily apparent to those skilled in the art from the following detailed description when considered in light of the accompanying drawings, in which:
0013 FIG. 1 is a perspective view of an assembly includ ing a Smart pill cap attached to a prescription pill container, according to one embodiment of the disclosure;
0014 FIG. 2 is an exploded side elevational view of the assembly of FIG. 1;
0015 FIG. 3A is an enlarged side elevational view of the threaded smart pill cap of FIG. 1, shown without the prescrip tion pill container, 0016 FIG. 3B is an enlarged bottom perspective view of the threaded smart pill cap shown in FIG. 3A:
0017 FIG. 4 is an enlarged bottom perspective view of a Smart pill cap according to another embodiment of the dis closure, wherein the Smart pill cap is childproof.
0018 FIG. 5 is a schematic diagram illustrating an example communication relationship between the Smart pill cap and pill container of FIG. 1 and a Smartphone application;

US 2016/0048,657 A1

0019 FIG. 6 is a schematic diagram illustrating an example of one network architecture between the Smart pill cap, and remote servers that store the web application; 0020 FIG. 7 is a schematic diagram illustrating an example network architecture where the Smart pill cap sends a wireless signal to a cellular gateway, which relays medica tion adherence information to remote servers through the Internet, which then routes medication adherence data to devices used by the patient and members of their care team; 0021 FIG. 8 is a schematic diagram illustrating an example network architecture according to another embodi ment of the disclosure;
0022 FIG.9 is a particular embodiment of a data structure for preserving securing within the remote servers;
0023 FIG. 10 is a flow diagram illustrating a method for sharing information from the Smart pill cap to a remote server through an intermediary remote computer, according to one embodiment of the disclosure;
0024 FIG. 11 is a flow diagram illustrating a method for initiating a prescription refill through the Smart pill cap, according to another embodiment of the disclosure; and 0025 FIG. 12 is schematic illustration of a smart pill cap that is capable of sensing and calculating the weight of the contents of the attached pill vial.

DETAILED DESCRIPTION
0026. The following description is merely exemplary in nature and is not intended to limit the present disclosure, application, or uses. It should be understood that throughout the drawings, corresponding reference numerals indicate like or corresponding parts and features.
0027 FIG. 1 illustrates a smart pill cap 101 that is capable of being removably coupled to a pill container 102, such as a vial. The smart pill cap 101 contains an internal switch-type contact sensor for detecting whether or not it is coupled to the container 102, thereby detecting whether the container is opened or closed. This information is stored in local memory that is also internal to the cap. As used herein, the term “memory may include a non-transitory and tangible com puter-readable storage medium, on which databases and pro cessor-executable software code may be embodied. The smart pill cap 101 transmits the information to an external computer or gateway via a wireless radio connection. Audio reminders may be emitted from a speaker internal to the Smart pill cap 101, which are configured to occur when the user does not open the container on a pre-scheduled basis.
0028. In a particular embodiment, a top plate 103 is incor porated into the smart pill cap 101 that can be removed in order to expose a coin cell style battery. A gap 104 between the top plate 103 and the primary container body 105 permits the top plate 103 to be removed via a prying action, as well as permits sound emitted by the internal speaker to be heard by
the user.
0029. A silicone band 106 provides an improved grip on the Smart pill cap while concealing a seam between the top and bottom portions of the smart pill cap assembly. The silicone band 106 may also be colored in a way that the user associates it with the display of one of their medications in the accompanying software of the Smart pill cap 101.
0030 The smart pill cap 101 can be placed on a prescrip tion or over-the-counterpill container in order to track medi cation usage and adherence. The container 102 may be filled by a pharmacist, drug manufacturer, drug distributor, or wholesale provider.

### Feb. 18, 2016

0031 FIG. 2 illustrates a sub-assembly of the smart pill cap 101 and integration with the pill container 102, according to one embodiment of the disclosure. A top portion 201 of the Smart pill cap housing is securely attached to a bottom portion 202 of the Smart pill cap housing, encasing a printed circuit board 203. Although the top portion 201 and the bottom portion 202 are described further herein as being distinct top and bottom pieces, separately formed and Subsequently attached to one another, it should be appreciated that the top portion 201 and the bottom portion 202 may also be formed integrally as a single or unitary one-piece body, as desired. 0032. The printed circuit board contains a switch type sensor 204, a wireless radio, memory, a speaker, and other electronic components. A sliding plate 204 is also encased by the top piece 201 of the housing and the bottom piece 202 of the housing. The sliding plate 204 presses down the switch type sensor 205 when the pill container 211 is attached to the smart pill cap 101 by tightening the threads 206 on the con tainer with the threads 207 internal to the Smart pill cap. 0033. A silicone band 208 may be placed on the outside of the assembled smart pill cap 101. The silicone band 208 may fit into a groove 209 that permits a flush fitting within the side of the smart pill cap 101. The silicone band 208 may cover up screw holes 210 that are used to attach the top piece 201 and the bottom piece 202 of the Smart pill cap 101.
0034 FIGS. 3A and 3B illustrate alternative views of the smart pill cap 101 that is designed to fit with a “1-click” pill container. A thread 302 secures the Smart pill cap to the pill container, with a rectangular block of plastic 303 that is incorporated into the smart pill cap 301 securing the 1-click mechanism that is built into the pill container. This ensures that the smart pill cap 301 remains securely fastened to the pill cap until the user presses the 1-click release mechanism on the container and twists the Smart pill cap 301 to remove it. 0035 FIG. 4 illustrates a further alternative version of the smart pill cap 101 that is designed to integrate with a child proof pill container. In this embodiment, rectangular blocks of plastic 301 are integrated to the Smart pill cap that fit with plastic “hooks' that are included on the external portion of a childproof pill container when the smart pill cap is pushed onto the childproof pill container. The sliding plate 302 selec tively activates, for example, by pressing against, the Switch type contact sensor when the container is attached to the Smart pill cap. A ridge 303 is included on the sliding plate 302 in order to maintain a tight seal with the mouth of the pill
container.
0036 FIG. 5 illustrates a medication adherence system comprising a smart pill cap 501, also described hereinabove and shown in FIGS. 1 and 2 as reference number 101, that transmits information that is sensed by the Switch-based sen sor 502 to a remote computer 508, such as a smartphone, tablet computer, or laptop computer, by transmitting informa tion digitally from the smart pill caps wireless radio 503 to the wireless radio contained in the remote computer 508. The smart pill cap stores data in local memory 506 that is trans mitted whenever the smart pill cap 501 and remote computer 508 are connected and are in range. A power source 504 such as a lithium or lithium-ion battery is contained inside the Smart pill cap and components are connected via a printed circuit board (PCB) 507.
0037. The remote computer receives has the capability to store data from the Smart pill cap in local memory 511. The remote computer also contains an onboard power 510 Source, such as a lithium ion battery. Most importantly the remote

US 2016/0048,657 A1

computer serves as the user's primary means of viewing data that is collected by the smart pill cap, with the user of the Smart pill cap having the ability to view said data on the display screen 512 of the remote computer 512 as well as to input data that can be sent from the remote computer 508 to the smart pill cap 501, such as a schedule of times when the user is Supposed to take the medications contained by the smart pill cap 501 and the pill container that it is mated to. 0038 FIG. 6 illustrates a medication adherence network architecture comprising the system described in FIG. 5. The remote computer 602 sends information received from the smart pill cap 601, also described hereinabove and shown in FIGS. 1 and 2 as reference number 101, to a remote server 604 through the Internet 603. The remote servers having storage 605 and processing capabilities 606. 0039 Data related to the user's medication adherence may be stored in the Smart pill cap, the remote computer, and on the remote server, with data periodically synced across all
three locations. Medication adherence data stored on the
smart pill cap may be deleted after a specified number of events in order to free up additional memory, preferably after data is pushed to the remote computer or remote servers. Information may also be sent from the remote servers to the user's remote computer. For example, information may be sent to the user's Smartphone related to pricing at various pharmacies where they can refill their medications.
0040. Optionally, a portion of the data captured by the smart pill cap may be shared from the remote servers to additional remote computers 607 that are managed by remote caregivers, care managers, family members, or healthcare professionals (doctors, nurses, physicians assistants, etc.). This sharing is likely to be executed via an application pro gramming interface (API) that is made available to users that have 1) received permission from the owner of the smart pill cap and first remote computer 2) have proven their credentials to the API through an authentication method, such as OAuth, a known open standard for authorization, or a token-based authentication method. This capability provides additional users to seeinformation that can help them to care for the user,
such as to intervene when the user has deviated from their
medication schedule. Moreover, the API enables 3rd party Solution providers to write custom Software applications that combine data from the Smart pill cap with data from other Sources. For example, the additional remote computers may combine data from the Smart pill cap with data from a wireless scale or a wireless blood pressure monitor to determine if the user has a high degree of risk of heart attack due to the user's deviation from their prescribed medication regimen.
0041 FIG. 7 illustrates a medication adherence system whereby the Smart pill cap 701, also described hereinabove and shown in FIGS. 1 and 2 as reference number 101, sends
data related to a user's medication adherence to a wireless hub
702 that is located within a close proximity (less than 2000 feet) that subsequently relays the data to remote servers 704.
The remote servers are able to send the medication adherence
data transmitted originally from the Smart pill cap 701 to at least one of the user's smartphone 707 or to remote computers 708 being operated by the user's caregiver, family member or a healthcare professional. This represents a different network architecture that requires an additional intermediate gateway device 702 that is not required in the architecture described in FIG. 6. However this architecture does not require the user to own a Smartphone or other device. In this case, the gateway 702 may also receive data sent by additional remote monitor

### Feb. 18, 2016

ing devices, such as wireless scales, blood pressure monitors, glucose monitors, motion sensors or other devices, most likely by using a wireless connection.
0042 FIG. 8 illustrates a medication adherence network architecture whereby the smart pill cap 801, also described
hereinabove and shown in FIGS. 1 and 2 as reference number
101, sends data directly to remote servers 804 through a cellular data connection without passing data through an intermediate hub or remote computer, Such as those that were described in FIG. 6 and FIG. 7. In this case, the remote servers 804 may relay data collected by sensors in the smart pill cap 801 to the user's remote computer, or to remote computers operated by people other than the user. The cellular connec tion used in this architecture may be GSM, CDMA, LTE or another network type.
0043 FIG. 9 illustrates anarchitecture for securely storing data collected by the Smart pill cap described in FIG. 1 on a remote server. Requests to a first remote server come in through a public gateway 901, with requests being routed to a second remote server through the load balancing layer 902. This helps to ensure maximum responsiveness and uptime by distributing the computational load among a network of serv ers. Requests are routed to the app layer 903 of a web appli cation or API that is designed specifically to be complimen tary to the smart pill cap device described in FIG.1. This app layer 903 can may requests to database layer 906 only through a private gateway 905. By limiting extraction of data from the database layer to a small subset of known servers, this helps to ensure security of the medication adherence data. All data stored in the server is also encrypted and servers are kept in locations that are physically secure. A bastion layer 904 run ning on one or more servers receives requests from protected areas of the network and is designated with specific respon sibilities, such as security privileges and access privileges. 0044 FIG. 10 illustrates a method for recording medica tion adherence data into memory located in a Smart pill cap and sending that information to remote servers via a Smart phone intermediary. The Smart pill cap will remain in standby mode 1001 until it senses a change to opened/closed State, at which point it will enter “active mode” for a predefined period of time. Standby mode may be designed to conserve power by reducing the advertising interval frequency by the wireless

radio. Once sensor data is detected 1002 it will be recorded
into memory 1003 located on the smart pill cap. When the Smart pill cap connects to a Smartphone that it is paired to, it sends the datalog to a complimentary application running on the Smartphone 1004. The smartphone is pre-programmed to
send medication reminders to the user unless it receives data
from the Smart pill container indicating that the Smart pill container has been opened within a time interval designated

to be associated with the scheduled medication event 1005.
The Smartphone also sends the sensor data log over the Inter net using a cellular, WiFi, or other wireless connection 1006. 0045 FIG. 11 illustrates a method for initiating a refill of a prescription medication, vitamin, or over-the-counter medi cation by interacting directly with the Smart pill container. The user initiates the refill action by initiating the sensor located inside of the Smart pill cap 1101 using a pre-defined action, Such as pressing the sliding plate two or three times quickly, or by tapping the container on the table. The micro controller within the smart pill cap interprets the sensed action to be a pill refill action 1102, and sends a pill refill request to the user's remote computer (e.g. Smartphone) dur ing the next session when the two devices communicate wire

US 2016/0048,657 A1

less 1103. The remote computer relays this refill message to a web application’s API endpoint 1104, with the web applica tion relating the refill request to a specific medication known to be taken by the user. The web application converts this into a refill request that can be send to a pharmacy’s API endpoint 1105, including information the pharmacy can use to identify the specific prescription Such as the RX number, Store ID, and possibly some information used to identify the individual (name, Social security number, phone number, etc.). Option ally this request may be routed through one or more interme diate APIS, such as an ePrescription web service, prior to being routed to the pharmacy. At this point the pharmacy has received information instructing them to refill the prescrip tion, which may help them comply with regulations requiring user-initiated actions to refill prescriptions. Optionally, the pharmacy API may return confirmation to the original web service that the prescription was successfully received 1106, with the web application relaying that message to the user's remote computer 1107 through a mobile application that is also capable of communicating with the Smart pill container. The pharmacy's API may send additional messages to the user to provide updates on the status of the prescription refill, Such as indication of when it is ready to be shipped or picked
up.
0046 FIG. 12 illustrates a method for integrating a method for detecting weight into the Smart pill cap. In order to use this design, the Smart cap and pill must be placed upside-down, with the contents of the pill container resting on the smart pill cap in an attached position. The weight of the pills presses on the sliding plate internal to the Smart pill cap, for example, the sliding plate 204 described hereinabove. The sliding plate rests on a spring 1204; this spring can be the spring included
in the sensor Switch.
0047. As shown in FIG. 12, a capacitor is created through two metallic plates, the first plate 1201 of which is attached to the printed circuit board. The second metallic plate is inte grated into the sliding plate, and may consist of a sliding plate that is coated in a metallic material on the side of the plate that is not in contact with the contents of the pill container. The sliding plate may move between a first position 1202 when the contents of the container are empty, and a second position
1203 when the contents of the container are full and there is a
greater force imposed on the plate. Capacitance is sensed by the printed circuit board and correlated to a measured dis tance, based on previous empirical experimentation. A weight is calculated based on Hooke's law, which holds that the displacement of a spring is proportional to the weight and the spring constant. The spring 1204 in the pushbutton may be used to provide the resistive force to the weight of the pills 1205 that are resting on the sliding plate 1201. Calibration is required to correlate weight to capacitance, which may be measured by creating a delay line consisting of the capacitive sensor and a large resistor (-10M Ohm).
0048. In another embodiment, the pushbutton itself is used as a capacitive weight sensor.
0049. In yet another embodiment, a load sensor is used that is attached to the printed circuit board.
0050. In a further embodiment, scattered light is used to measure the distance between the PCB and the sliding plate. An infrared LED and complementary photoreceiver are placed in proximity on the side of the printed circuit board that is facing the sliding plate. Scattering from the sliding plate results in reflections of a portion of the illuminated light onto the photoreceiver, with the intensity of the light being

### Feb. 18, 2016

proportional to the distance between the two plates. This
illumination is best enabled in short bursts or on command in
order to conserve energy. 0051. From the foregoing description, one ordinarily skilled in the art can easily ascertain the essential character istics of this disclosure and, without departing from the spirit and scope thereof, make various changes and modifications to the disclosure to adapt it to various usages and conditions.
What is claimed is:
1. A cap for a medication container, comprising:
a housing with a top portion and a bottom portion and defining a cavity therebetween;
a sliding plate disposed in the cavity adjacent the bottom portion; and
a microcontroller with a contact sensor disposed in the cavity between the top portion and the sliding plate, the sliding plate configured to slide toward and activate the contact sensor where the cap is secured to the medica tion container in a closed State, and the sliding plate configured to slide away from and not activate the con tact sensor where the cap is removed from the medica tion container in an open state.
2. The cap of claim 1, wherein the microcontroller includes a printed circuit board.
3. The cap of claim 2, wherein the printed circuit board further includes a wireless radio, a memory, and a speaker.
4. The cap of claim 3, wherein the microcontroller is con figured to store in the memory information corresponding with the sliding plate pressing against the contact sensor, the information indicative of an opening and a closing of the medication container over time, and transmit the information to at least one of an external computer and a cellular gateway
via the wireless radio.
5. The cap of claim 3, wherein the microcontroller is con figured to cause the speaker to emit an audio reminder accord ing to a predetermined schedule.
6. The cap of claim 1, wherein the bottom portion of the housing has internal threads configured to cooperate with
external threads of the container.
7. The cap of claim 1, wherein the top portion of the housing has a removable top plate that permits access to the cavity upon removal.
8. The cap of claim 1, further comprising a silicone band disposed on an outer perimeter of the cap.
9. The cap of claim 8, wherein the top portion is a top piece and the bottom portion is a bottom piece, the top piece formed separately from the bottom piece, the top piece affixed to the bottom piece to fonn the housing., and at least one of the top piece and the bottom piece defines a groove on an outer Surface thereof, the groove extending around an entirety of the cap, the silicone band disposed in the groove.
10. The cap of claim 1, wherein the microcontroller further includes a sensor configured to measure a weight of contents of the container where the container is turned upside down.
11. A system for promoting adherence to a regimen by a patient, comprising:
a cap for a medication container, including a housing with a top portion and a bottom portion and defining a cavity therebetween, a sliding plate disposed in the cavity adja cent the bottom portion, and a microcontroller with a contact sensor disposed in the cavity between the top portion and the sliding plate, the sliding plate configured

to slide toward and activate the contact sensor where the
cap is secured to the medication container in a closed

US 2016/0048,657 A1

state, and the sliding plate configured to slide away from and not activate the contact sensor where the cap is removed from the medication container in an open state;
and
a first remote computer having a memory and a display, the first remote computer in electronic communication with the cap and configured to show on the display informa tion corresponding with the sliding plate activating the contact sensor, the information indicative of an opening and a closing of the medication container over time.
12. The system of claim 11, wherein the first remote com puteris one of a personal computer, a tablet, and a Smartphone of the patient.
13. The system of claim 11, further comprising a cellular gateway in communication with both the cap and the first remote computer.
14. The system of claim 11, further comprising a second remote computer in communication with the first remote computer over the Internet.
15. The system of claim 14, wherein the second remote computer provides access to the information to one of a caregiver and a provider of the patient.
16. A method for promoting adherence to a regimen by a patient, the method comprising the steps of
providing a system including a cap for a medication con tainer, the cap having a housing with a top portion and a bottom portion and defining a cavity therebetween, a sliding plate disposed in the cavity adjacent the bottom portion, and a contact sensor disposed in the cavity between the top portion and the sliding plate, the sliding plate configured to slide toward and activate the contact sensor where the cap is secured to the medication con tainer in a closed State, and the sliding plate configured to slide away from and not activate the contact sensor where the cap is removed from the medication container in an open state, and a first remote computer having a

### Feb. 18, 2016

memory and a display, the first remote computer in elec tronic communication with the cap and configured to show on the display information corresponding with the sliding plate activating the contact sensor, the informa tion indicative of an opening and a closing of the medi cation container over time;
maintaining the cap in a standby mode until the cap senses a change in state from one of the open state and the closed State;
causing the cap to enter an active mode for a predefined period of time, the cap configured to record the informa tion from the contact sensor in the active mode; creating by the microcontroller of the cap a sensor datalog of the information; and
communicating from the microcontroller of the cap to the first remote computer the sensor data log.
17. The method of claim 16, further comprising the step of sending medication reminders to the patient by the first remote computer unless the first remote computer receives information from the cap indicating that the container has been in the open state within a time interval designated to be
associated with a scheduled medication event.
18. The method of claim 16, further comprising the step of initiating a refill action by a pre-defined action on the cap, the predefined action causing the microcontroller to send a refill request to the first remote computer.
19. The method of claim 18, further comprising the step of relaying the refill request by the first remote computer to a web application, which in turn provides the refill request to a pharmacy.
20. The method of claim 19, further comprising the step of sending by the web application a message to the first remote computer confirming a successful refill action by the phar
macy.
