Benedict-Bsl/SmartCap/Documents/US20160120758A1.pdf

US 2016O120758A1

## (19) United States

# (12) Patent Application Publication (10) Pub. No.: US 2016/0120758 A1

P. et al. | (43) Pub. Date: | May 5, 2016
(54) SMART PILL CONTAINER, CONTROL | (52) U.S. Cl.
METHOD AND SYSTEM | CPC. A61J 704 (2013.01); A61J I/03 (2013.01);
H04O9/00 (2013.01); H04O 2209/40 (71) Applicants: Bo PI, San Diego, CA (US); Halton PI, | (2013.01)
San Diego, CA (US)
(72) Inventors: Bo PI, San Diego, CA (US); Halton PI, | (57) | ABSTRACT
San Diego, CA (US)
A medicine pill box or pill bottle equipped with sensors to
(21) Appl. No.: 14/933,884 | detect presence or absence status of pills and/or movement of
(22) Filed: | Nov. 5, 2015 | the pill box or bottle and/or removal of a bottle cap, and a
communication module for wirelessly communicating with
Related U.S. Application Data | an external device to exchange data with the connected device
and internet-based services. The internet-based service
(60) yinal application No. 62/075,804, filed on Nov. | records the data from the pill box or bottle and sends relevant s | notifications and reminders to authorized users. In one
Publication Classification | example, capacitive sensors are provided at the bottom of
each cell of a pill box having multiple cells, to detect the
(51) Int. Cl. | presence and absence of pills in the cells. In another example,
46.7/04 | (2006.01) | magnetic field sensors are provided on the cap of a pill bottle
H04O9/00 | (2006.01) | and magnetic materials are provides on the body of the bottle,
A61. I/03 | (2006.01) | to detect the removal of the cap.

Other authorized

### USer 140

## Smart pill Container 1

Connected
Communication

## device 110

internet-based
cloud service
120

User's Mobile

## device 130

Patent Application Publication | May 5, 2016 Sheet 1 of 13 | US 2016/O120758A1

Patent Application Publication | May 5, 2016 Sheet 2 of 13 | US 2016/O120758A1

i

## Cell Sensor ... circuit. 2

•
O
O
S.

Patent Application Publication | May 5, 2016 Sheet 3 of 13 | US 2016/O120758A1

Patent Application Publication | May 5, 2016 Sheet 4 of 13 | US 2016/O120758A1

OY

co | y
G)
| See
S
99

y
N

Patent Application Publication | May 5, 2016 Sheet 5 of 13 | US 2016/O120758A1

Patent Application Publication | May 5, 2016 Sheet 6 of 13 | US 2016/O120758A1

Patent Application Publication | May 5, 2016 Sheet 7 of 13 | US 2016/O120758A1

i

Patent Application Publication | May 5, 2016 Sheet 8 of 13 | US 2016/0120758A1
i

i

Patent Application Publication | May 5, 2016 Sheet 9 of 13 | US 2016/O120758A1

555

Patent Application Publication | May 5, 2016 Sheet 10 of 13 | US 2016/O120758A1

318 pue[nOWN

Patent Application Publication | May 5, 2016 Sheet 11 of 13 | US 2016/O120758A1

Patent Application Publication | May 5, 2016 Sheet 12 of 13 | US 2016/0120758A1

Patent Application Publication | May 5, 2016 Sheet 13 of 13 | US 2016/O120758A1

US 2016/0120758 A1

SMART PILL CONTAINER, CONTROL
METHOD AND SYSTEM

BACKGROUND OF THE INVENTION
0001 1. Field of the Invention
0002 This invention relates to a control system and method to control taking of medicine pills, which uses sen sors for monitoring the status of the pill container, and a wireless link to report to user and a server program the status of the pill box to trigger appropriate actions.
0003 2. Description of Related Art
0004. In a conventional pill box, shown in FIG. 5, the pill box has multiple cells, which the user uses to help organize daily medicine or medicine needs to be taken at different times. With a conventional pill box, the user puts one or multiple types of medicines he needs to take each day in each cell of the pill box. And the user will typically remember to take the pill each day. For example, if the user forgot to take the pill for Tuesday, he returns home, and takes a look at the pillbox, he will find the pill still in the Tuesday cell. So it also serves as a reminder for the user. However, if the user forgot to check, then he would not know if he took the pill or not. Further, if the user's medicine needs to be taken at certain times, like in the morning, and if user forgot to take it, no one will remind him until he remembers to check the pillbox. The user may take the pill at a later time; this delay may affect the
medicine effectiveness.

SUMMARY
0005. One embodiment of this invention relates to a medi cine pillbox and a related user notification system. The Smart pill box has sensors in each pill box cell, and these sensors detect the status of each pill box cells, e.g. the presence or absence of pills, and/or the number of pills in the cell. The Smart pill box also has a communication module, which can be wirelessly connected to a communication device, to exchange data with the connected device and also exchange data with an Internet-based service through the connected
device. The Internet-based service records the status of each
Smart pill box, and also provides services like sending noti fications to authorized users regarding the status of the pill box, sending out reminders to a mobile device of the Smart pill box user to remind the person to take medicine if the medi cines in the pill box cell are not taken out in time, etc.
0006. The pill box according to an embodiment of the present invention has a sensor System, which senses the con tent of each pillbox cell, to determine which cell has pills or not. An electronic controller controls the sensor System, and also reads out sensed data from the sensor System. In one embodiment, when a cell contains one or more pills and the user takes out the pill from a cell, the status of the cell is changed from full to empty. This information is sent to the connected communication device, which directly notifies the user, or through the internet-based service sends the notifica tion to multiple peoples who are authorized to receive this information. An internet host database keeps a record of the status of each user. The Summery results are updated periodi cally for authorized persons to view. The authorized persons may include the user himself/herself, the user's care takers, the user's doctors, the user's relatives etc.
0007 Additional features and advantages of the invention will be set forth in the descriptions that follow and in part will be apparent from the description, or may be learned by prac

## May 5, 2016

tice of the invention. The objectives and other advantages of the invention will be realized and attained by the structure particularly pointed out in the written description and claims thereofas well as the appended drawings.
0008 To achieve these and/or other objects, as embodied and broadly described, the present invention provides a Smart pill box system which includes: a pill box body with multiple cell for containing pills; a sensor on the bottom of each cell for detecting presence or absence of the pills in the cell; a sensor circuit for processing signals from the sensor, a communica
tion circuit for wireless communication with external
devices; a battery; and a microprocessor unit and memory for controlling operations of the sensor circuit and communica
tion circuit.
0009. In another aspect, the present invention provides a method for monitoring the status of a Smart pillbox, the Smart pill box comprising one or more cells for containing pills, a sensor System for detecting presence or absence status of pills in each cell, control circuitry, and a communication unit, the method including: detecting the presence of absence status of each cell using the sensor system; recording status informa tion for each cell using the control circuitry; and communi cating the status information wirelessly to an external data processing system using the communication unit.
0010. In another aspect, the present invention provides a smart pill bottle system which includes: a sensor unit on the bottle, which includes an accelerometer, a magnetic field sensor, a communication circuit, a battery and a microcon troller and memory; and a magnetic material placed on the bottle, wherein the sensor unit is located on a cap of the bottle and the magnetic material is located on a body of the bottle, or the sensor unit is located on the body of the bottle and the magnetic material is located on the cap of the bottle.
0011. In another aspect, the present invention provides a method for monitoring a smart pill bottle, the smart pill bottle including a sensor unit which includes an accelerometer, a magnetic field sensor, a communication circuit, a battery and a Microcontroller and memory, and magnetic material, wherein the sensor unit is located on a cap of the bottle and the magnetic material is located on a body of the bottle, or the sensor unit is located on the body of the bottle and the mag netic material is located on the cap of the bottle, the method including: detecting a motion of the pill bottle using the accelerometer and generating a wakeup signal for the micro controller;
0012 detecting an event of a separation of the cap and the body of the bottle using the magnetic field sensor and the magnetic material and recording the separation event; and communicating the separation event to an external device. 0013. It is to be understood that both the foregoing general description and the following detailed description are exem plary and explanatory and are intended to provide further explanation of the invention as claimed.

BRIEF DESCRIPTION OF THE DRAWINGS
0014 FIG. 1 is a block diagram showing a smart pillbox connected to an internet-based service and to a user according to an embodiment of the present invention.
0015 FIG. 2 is a schematic illustration of the smart pill box according to an embodiment of the present invention. 0016 FIG. 3A shows an exemplary implementation of a capacitive Smart pill box sensor design according to an embodiment of the present invention.

US 2016/0120758 A1

0017 FIG. 3B is a schematic illustration of how the capacitive Smart pillbox sensor of FIG. 3A senses the pills in
the box cell.
0018 FIGS. 4A and 4B are flow diagrams showing how the Smart pillbox operates according to an embodiment of the present invention.
0019 FIG. 5 illustrate a conventional pill box.
0020 FIG. 6 is a schematic illustration of a smart bottle cap sensor according to another embodiment of the present
invention.
0021 FIG. 7 is a schematic block diagram of an exemplary implementation of the Smart bottle cap sensor design of FIG.

6.
0022 FIG. 8 is a flow diagram showing how the Smart cap sensor of FIGS. 6 and 7 operates.
0023 FIGS. 9A and 9B are schematic illustrations of a Smart bottle cap sensor according to another embodiment of the present invention.
0024 FIG.9C is the top view of an exemplary smart cap SSO. 0025 FIGS. 10A-C show data taken from an exemplary implementation of a smart bottle cap sensor of FIGS. 9A-B.

DETAILED DESCRIPTION OF PREFERRED EMBODIMENTS
0026. A preferred embodiment of the Smart pill box is descripted as follows with reference to FIGS. 1-3B. Like in a conventional pill box (see FIG. 5), the smart pill box 1 has multiple cells 2, which the user uses to help organize daily
medicine or medicine needs to be taken at different times. In
the Smart pillbox according to an embodiment of the present invention, the box1 has sensors to detect if each cell is empty or full with medicine. And the box 1 reports the status (full/ empty) to the connected device 110, which may be a smart phone, or a network gateway devices, or a network router, through a wireless connection, which maybe Bluetooth, Wi Fi, or other wireless links. The status of the pill box can be send, via the connected device 110, to an internet cloud based server 120, running a services Software to monitor each user's pill box status. Each user or his care taker, can configure the service software so it will record the status; also it may send out notice (and reminder) to user mobile devices 130, and/or to other authorized person's device 140. The user's mobile
device 130 and the connected device 120 in some case can be
the same device. The server software can also keep a record of when each user takes medicine in which pill box cell, and provide a summary of how well the user complies with the time schedule that he is required to take the medicine. 0027. The user or the user's authorized care taker can configure the service software to send out different remind ers, for example, if the pillbox cell has not been emptied at a set time, the service software will send out reminder at cer tainly time after the time that user is supposed to take the medicine. Also, the user or authorized person can check with service Software to get status if the user has taken the medi
cine or not.
0028. A preferred implementation of the smart pill box 1 of an embodiment of the present invention is illustrated in FIG. 2, where at the bottom of each cell 2, there are capacitive sensor elements. An example implementation of the capaci
tive sensorelements 8 and 9 is illustrated in FIGS. 3A and 3B.
In an example implementation of the Smart pillbox 1, there is a cell sensor circuit 3, which interfaces with the capacitive sensor elements. The sensor circuit 3 measures the capaci

## May 5, 2016

tance changes in sensor elements 8 and 9 of each cell. The sensor elements 8 and 9 are designed such that there will be differences in the capacitance between when the cell has pill(s) and when the cell is empty. Alternatively, the sensor elements 8 and 9 and the control circuit 3 may be designed to detect the number of pills present in each cell. The Smart pill box 1 also includes a microcontroller (MCU) with memory 4, a wireless communication circuit 7, an accelerometer (G sen sor) 5, and a battery 6. The wireless communication circuits 7 can be implement as low energy Bluetooth, Wi-Fi, Zigbee, or Some other standard or proprietary wireless communication schemes. The microcontroller 4 can execute a program to control the operation of the various circuits of the smart pill box 1. It also keeps a time and date of when each detected event happens. The events include when the user fills or empties the pill box cells. The microcontroller 4 also stores the status of the pill cells and the event time in the memory.
The microcontroller 4 also controls the communication cir
cuit 7 to periodically check if there is a connected communi
cation devices 110 available. A connected communication
device can be a cell phone, or a dedicated communication device (like a gateway, a router). When the microcontroller 4 detects a connected communication device available, it trans fers the status of the pill box to the connected device, and through the connected device, transfers the status to an inter net cloud based service program 120.
0029. The cell sensor circuit 3, the MCU4, the G sensor 5, the battery 7 and the communication circuit 7 may be physi cally located at any appropriate location of the overall pill box. Such as in a compartment under the cells 2, or in a compartment on the side of the cells, etc.
0030 FIG. 4A illustrates a process flow diagram of the smart pill box operation. When the pill box is not in use, the microcontroller 4 puts the system in a low power standby mode (step S41), where, the communication circuit 7 is in a low power standby mode, and the cell sensor circuit 3 is also in a low power standby mode. The G sensor 5 is normally in a low power detection mode, where the G sensor is used to detect ifa user is accessing the Smart pillbox 1. When the user tries to access the Smart pill box 1, like he pick up the box to open a cell to get the pill, or fill in the pills, the G sensor detects the motion of the Smart pill box (step S42). The G sensor S sends a signal to the microcontroller 4 to indicate that the user may be accessing the pill box (step S42). Upon receiving this signal, the microcontroller 4 changes to a nor mal detection mode; it also turns the sensor circuit 3 to a normal mode, and tries to scan the Smart pill box cell sensor elements 8 and 9, to check if there is capacitance changes in each cell 2. And it records the status of the cells in the memory with a time stamp (step S43). The microcontroller 4 also turns the wireless communication circuit 7 into a normal operation mode, and checks for connected device availability (step S44). If the connected device 110 is detected, the microcon troller 4 transfers the status of the smart pill box to the con nected device and through the connected device to the inter net cloud service program 120 (step S45).
0031. The microcontroller 4 also keeps a counter running in the standby mode, and if the microcontroller has not received signals from the G sensor 5 over a predetermined time period, the microcontroller periodically wakes up the system, and its circuits, to check for connected communica tion device availability (step S46). When the communication device 110 is available, the microcontroller 4 transfers the

US 2016/0120758 A1

recorded status to the connected device 110 and through the
connected device transfers it to the internet cloud service
program 120 (step S47).
0032. In another simpler form of implementation, illus trated by the flow diagram of FIG. 4B, the G sensor 5 is not required for the pill box system. The microcontroller is nor mally in a sleep mode and waits for wakeup timer interrupt (step S41A); it wakes up periodically (step S42A), to check the status of the pillbox cells (step S43A), and also check for presence of the connected device (step S44A). If the con nected device is detected, and the status of the cells has changed, the microcontroller sends updated information to the connected device and through the connected device to the internet cloud based service program (step S44A).
0033. In an exemplary implementation, the capacitive sensing elements for each pill cell are illustrated in FIGS. 3A, 3B. Under each pill cell 2, there are two group of interleaved electrodes 8,9. One group of the electrodes 8 transmits an RF signals (TX), typically in the frequency range of 100 Hz to 10 MHz. Another group of the electrodes 9 is connected to an amplified receive circuit 11 of sensor circuit block3, to detect the TX signals. As illustrated in FIG. 3B in detail, the mate rials 23 form bottom panels of the cells 2 isolates the elec trodes from the pills 21, and the cell walls 22 are also provided to contain the pills. These materials forming the bottom panel 23 and cell walls 22 can be plastics, glasses, or other polymers
materials which is nonconductive. There is electrical cou
pling (capacitive coupling) between two group of the elec trodes, as schematically indicated by the lines 20, and the present or absent of the pills 21 in the cell changes change the coupling of the signal (i.e. the capacitance between two groups of electrodes changes). The sensor circuit 3 detects these changes, and the software in the MCU 4 receives these data, to determine if the cell status is changed or not.
0034. Two groups of electrodes are used in this example to detect the change of material in the proximity of the elec trodes. Similarly one can use a single group of electrode to detect the change of materials in the proximity of the elec trode. In that case, there will be just one set of electrode under each pill cell 2.
0035. In another implementation of a smart pill control system, a Smart cap sensor is used to monitor the user's opening of the cap of a medicine bottle, and also wirelessly
communicate the information to a connected communication
device, and through the connected device to an internet cloud service program. Similar to the Smart pill box system and method described above, the internet cloud service can pro vide recording and sending out notifications to user and authorized persons.
0036 FIGS. 6 and 7 schematically illustrate an implemen tation of the Smart cap sensor used for monitoring the medi cine bottle. The sensor unit 31 (also referred to as a detection and communication system) may be attached to the top of the bottle cap 37 by an adhesive 32; the adhesive can be a double sided adhesive tape, or other adhesive. Alternatively, the sen Sor unit may be located inside the cap, for example, attached to the underside of the cap 37. The sensor unit 31 includes a communication circuits 47, an acceleration sensor (G sensor) 45, a magnetic field sensor (M sensor) 43, a microcontroller and memory 44, and a battery 46. The implementation also includes magnetic materials on the body 36 of the bottle. This can be implemented as a sticker with magnetic properties or a small magnet attached by a sticker, on the side of bottle 35, or on the bottom of the bottle33, or around the bottle as a ring

## May 5, 2016

34. The electronics detection and communication system 31 may alternatively be located on the body 36 of the bottle, in which case the magnetic material is located on the cap 37. 0037 FIG. 8 illustrates a process flow diagram of the smart pill bottle operation. When the pill bottle is not in use, the MCU puts the system in standby mode, where very low power is required (step S81). When the G sensor is in a low power mode, it can detect motions of the bottle. When user picks up the bottle, the G sensor detects the motion, and sends a signal to MCU (step S82); when MCU receives this signal, it wakes up the system, and turn on the M sensor (step S83). When the user opens the cap, the M sensor detects the sepa ration of the M sensor from the magnetic materials on the body of the bottle (33, or 34, or 35). It is the assumption that when user opens the medicine bottle, he will take his pill. The MCU records the event (opening of the bottle cap) with a time stamp. MCU also checks if a connected device is available (step S84), and communicate the event information to con nected device and through the connected device, communi cate to an internet cloud based service program (step S85). MCU also has an independent wake up timer, which wakes up MCU periodically to check if the connected device is avail able (step S86), and complete the communication of the bottle event to the connected device and through connected device to an internet cloud based service program (step S87). The cloud based service program 120 can record the event, and perform statistics of the event, and generate report of user/ bottle use, and send out notices to user and other authorized persons. In the event that the user forgot to take pill, the service program sends out reminder to user and other care
taker.
0038 FIGS. 9A and 9B schematically illustrate another implementation of this embodiment. FIG.9A is side view and FIG.9B is a top view of the medicine bottle. In this imple mentation, the detection and communication system 31 is located in the bottle cap 37; it includes a chip 42 which includes a magnetic field sensor (M sensor) or both an accel eration sensor (G sensor) and an M sensor (a combination chip), and a chip 41 that integrates the MCU 44 and the communication circuit 47. FIG.9C is a photograph showing a sample detection and communication system 31 including the chips 41 and 42 (M and G sensor chip). A magnetic material strip 38 is mounted on the body 36 of the medicine bottle, where the north and south poles of the magnet 38 is aligned in up/down direction (i.e. in the longitudinal direc tion) of the body 36 to ensure maximum magnetic field spread out of the magnet to reach the M sensor. The relative location of the M sensor and magnet strip is to be kept as close as possible to maximum the signals of the magnet on the M sensor. As shown in FIG. 9B, in the top view, the magnetic strip 38 and the M (or M and G) sensor chip 42 are aligned in the circumferential direction when the cap 37 is properly closed on the body 36 of the bottle. The magnet strip 38 can be attached with an adhesive tape to the side of the bottle. 0039. A visible marker 39 is optionally provided on the outside of the sensor unit 31 to indicate the position of the M sensor 42 inside the sensor unit. It helps the user to place the magnet strip 38 close to the M sensor. If the G sensor is in a separate chip from the M sensor, then the location of the G sensor is not important, as long as it is mounted inside the sensor unit 31. The chips are preferably mounted on a printed
circuit board. Note that the M and G sensors in the sensor
chips have their built in directionality, typically including three axes; when the chips are mounted on the PCB, the

US 2016/0120758 A1

alignment of the axes depend on the PCB mount. In most applications the precise directions of the axes are not impor
tant.
0040. The G sensor can detect movements of the bottle, while the M sensor can detect the rotation of the cap 37 or its removal from the body 36. In actual implementations, for a given G and M sensor chip 42 and a given magnetic strip 38 on a given bottle, the signal from the G and M sensor relative to the remove of the cap 37 of the bottle can be measured; based on the measurements, the microcontroller is designed to have appropriate signal thresholds for making various determinations as to whether the bottle is being picked up or the cap is being removed.
0041 FIGS. 10A-C are examples of measurement data taken from a Smart cap sensor having the configuration of FIGS. 9A-B. In each figure, the top panel is the M sensor signal and the bottom panel is the G sensor signal. Each sensor has three axels and their signals are represented by the three curves. In FIG. 10A, where the vertical axis is the signal of the sensor output, and the horizontal axis is the samples read in by the MCU, typical in the time of 1 Hz to 10 kHz sample rate, this graph is sample at 10 HZ rate, the cap was on the bottle body and the bottle was moved. In this case, when the bottle was moved, the G sensor signal changed up to +/-500 units, while the M sensor signal changed by smaller amounts, about +/-200 units, which are similar to the signal caused by changes in the earth magnetic field. In other words, and M sensor was picking up the changes in the magnetic field by moving the bottle in in the earth’s magnetic field.
0042. In FIG. 10B, the bottle cap was removed. It can be seen that the M sensor signal changed more than 1000 units in all 3 directions, which is much larger than the signal caused by changes in the earth's magnetic field in FIG. 10A. Also, the signal in one direction was of the opposite polarity as that in the other two directions. The G sensor signal also picked up the motion of the cap.
0043. In FIG. 10C, the bottle cap was put back on, where the magnetic strip on the bottle was again aligned with the M sensor. It can be seen that the G sensor picked up the motion of the cap (the signal change is +/-200 units). The M sensor signal again changed over 1000 units in all 3 directions; again the signal in one direction is of the opposite polarity as that in the other two directions. The M sensor signal change back to the state it was in when the cap was close on the bottle. The
data shown in FIGS. 10A-C demonstrates that the movement
of the bottle and the removal and re-placement of the cap can be reliably detected using the M and G sensors in the present
embodiments.
0044. In another implementation, every time when user closed the cap put the bottle back to storage, user can shake the bottle, or hit gently table two or more times. This can signal the sensor through the signal of the G sensor that the bottle is closed put to rest. And the sensor can ran through a
calibration program to acquire the normal values of each sensor as baseline values. These baseline values can be used
to compare with sensor values when user pick up the bottle and remove the cap. This makes it more accurate to determine the thresholds to determine the state changes of the bottles. 0045. This smart cap implementation can also be used to monitor access of a bottle for other materials. For example, it can be used to monitor alcohol bottles, so if the bottle is open by unknown person, it will send notice to internet service program. This can monitor unwanted kids use of alcohol in

## May 5, 2016

the family. It can also be used in the hotel to monitor the access of the premier drinks provide in hotel room.
0046. It will be apparent to those skilled in the art that
various modification and variations can be made in the Smart
medicine container and related method of the present inven tion without departing from the spirit or scope of the inven tion. Thus, it is intended that the present invention cover modifications and variations that come within the scope of the appended claims and their equivalents.
What is claimed is:
1. A Smart pill box system comprising:
a pill box body with multiple cell for containing pills;
a sensor on the bottom of each cell for detecting presence or absence of the pills in the cell;
a sensor circuit for processing signals from the sensor; a communication circuit for wireless communication with
external devices;
a battery; and
a microprocessor unit and memory for controlling opera
tions of the sensor circuit and communication circuit.
2. The smart pillbox system of claim 1, wherein the sensor is a capacitive sensor for generating capacitance signals in response to the presence or absence of the pills.
3. The Smart pill box system of claim 2, further comprising an accelerometer for detecting motions of the Smart pill box.
4. A method for monitoring the status of a Smart pill box, the Smart pillbox comprising one or more cells for containing pills, a sensor system for detecting presence or absence status of pills in each cell, control circuitry, and a communication unit, the method comprising:
detecting the presence of absence status of each cell using the sensor system;
recording status information for each cell using the control circuitry; and
communicating the status information wirelessly to an external data processing system using the communica
tion unit.
5. The method of claim 4, wherein the Smart pillbox further comprises an accelerometer for detecting motions of the Smart pill box, the method further comprising generating a wakeup signal for the control circuitry when a motion of the smart pill box is detected.
6. A Smart pill bottle system comprising:
a sensor unit on the bottle, which includes an accelerom eter, a magnetic field sensor, a communication circuit, a battery and a microcontroller and memory; and
a magnetic material placed on the bottle,
wherein the sensor unit is located on a cap of the bottle and the magnetic material is located on a body of the bottle, or the sensor unit is located on the body of the bottle and the magnetic material is located on the cap of the bottle.
7. A method for monitoring a smart pillbottle, the smart pill bottle including a sensor unit which includes an accelerom eter, a magnetic field sensor, a communication circuit, a bat tery and a Microcontroller and memory, and magnetic mate rial, wherein the sensor unit is located on a cap of the bottle and the magnetic material is located on a body of the bottle, or the sensor unit is located on the body of the bottle and the magnetic material is located on the cap of the bottle, the method comprising:
detecting a motion of the pillbottle using the accelerometer and generating a wakeup signal for the microcontroller;

US 2016/0120758 A1

detecting an event of a separation of the cap and the body of the bottle using the magnetic field sensor and the mag netic material and recording the separation event; and
communicating the separation event to an external device. k | k | k | k | k

## May 5, 2016
