Benedict-Bsl/SmartCap/cv/Dataset/p1.PNG

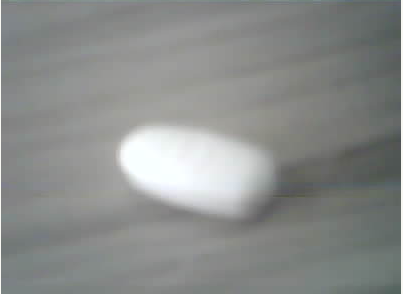
cv/Dataset/p1.PNG
