Benedict-Bsl/SmartCap/cv/Dataset/p2.PNG

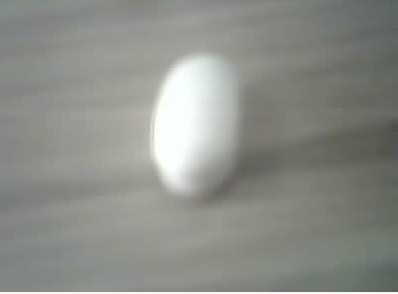
cv/Dataset/p2.PNG
