Benedict-Bsl/SmartCap/cv/Dataset/p3.PNG

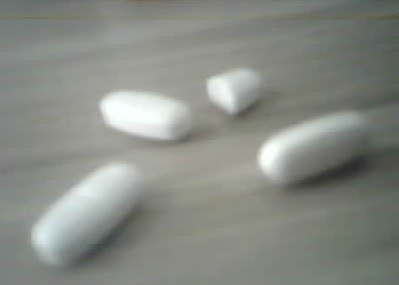
cv/Dataset/p3.PNG
