Benedict-Bsl/SmartCap/cv/Dataset/p4.PNG

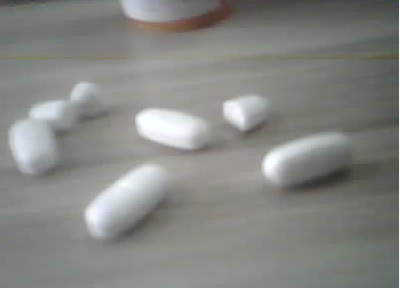
cv/Dataset/p4.PNG
