Benedict-Bsl/SmartCap/cv/Dataset/p6.PNG

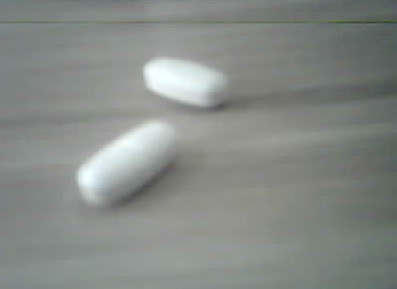
cv/Dataset/p6.PNG
