Benedict-Bsl/SmartCap/cv/Dataset/p7.PNG

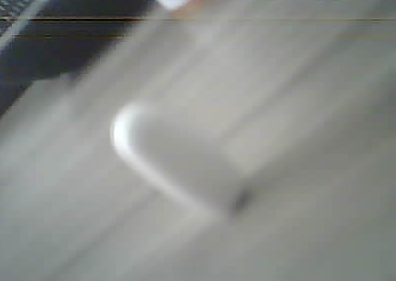
cv/Dataset/p7.PNG
