Benedict-Bsl/SmartCap/cv/Dataset/p8.PNG

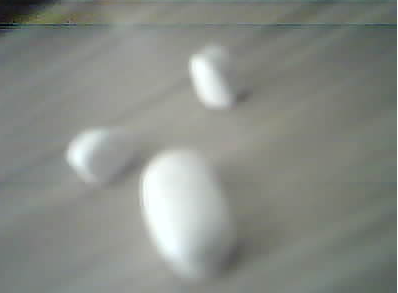
cv/Dataset/p8.PNG
