Benedict-Bsl/SmartCap/cv/Dataset/p9.PNG

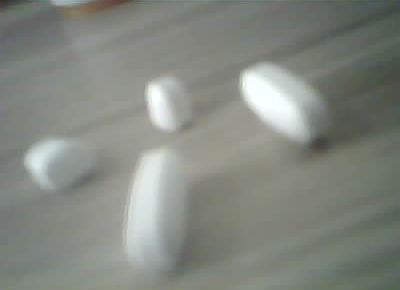
cv/Dataset/p9.PNG
