Benedict-Bsl/SmartCap/cv/Dataset/p10.PNG

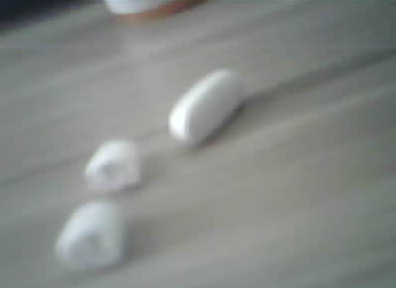
cv/Dataset/p10.PNG
