Benedict-Bsl/SmartCap/cv/Dataset/p11.PNG

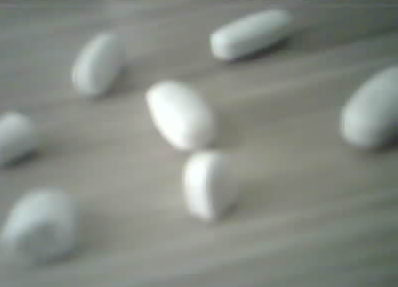
cv/Dataset/p11.PNG
