Benedict-Bsl/SmartCap/cv/Dataset/p12.jpg

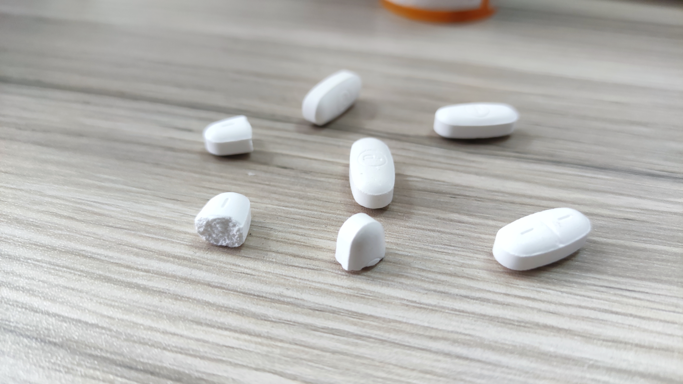
cv/Dataset/p12.jpg
