Benedict-Bsl/SmartCap/cv/Dataset/p13.jpg

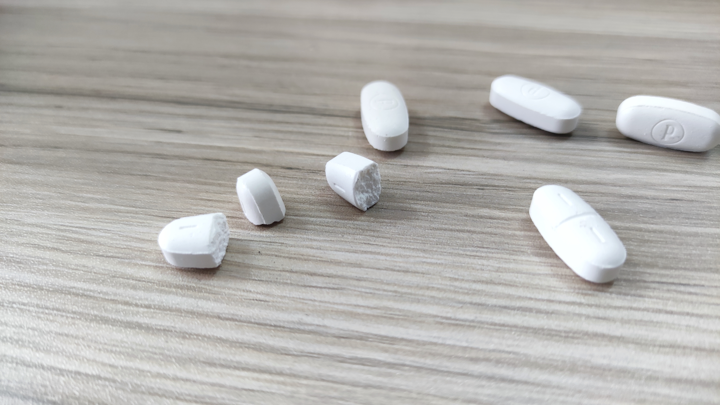
cv/Dataset/p13.jpg
