Benedict-Bsl/SmartCap/cv/Dataset/p14.jpg

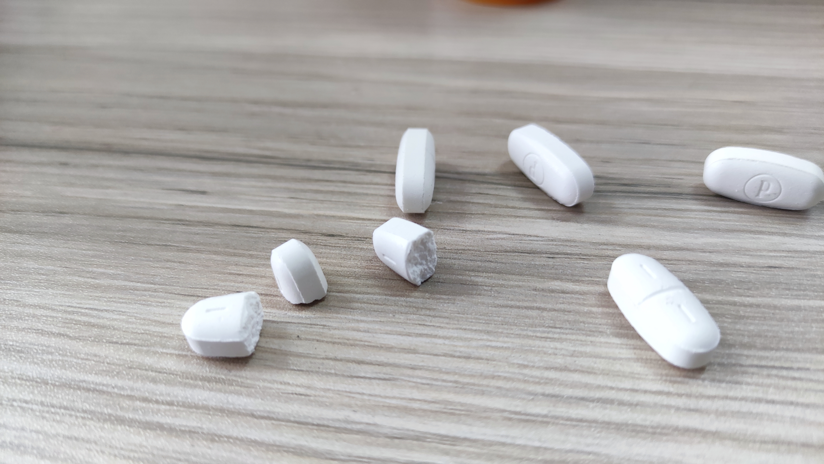
cv/Dataset/p14.jpg
