Benedict-Bsl/SmartCap/cv/Dataset/p15.jpg

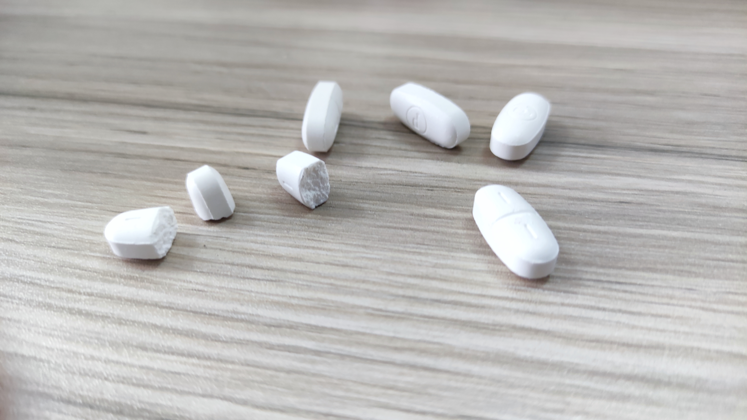
cv/Dataset/p15.jpg
