Benedict-Bsl/SmartCap/cv/Dataset/p16.jpg

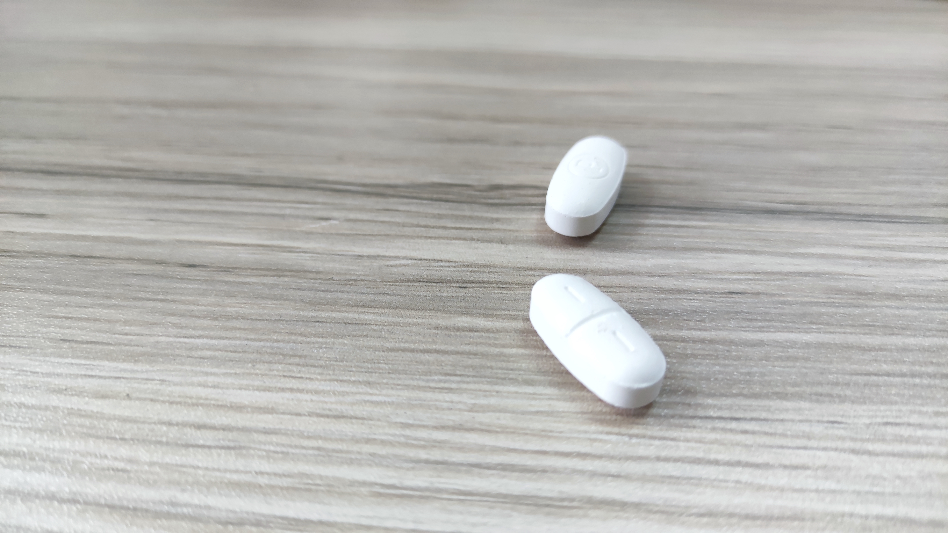
cv/Dataset/p16.jpg
