Benedict-Bsl/SmartCap/cv/Dataset/p17.jpg

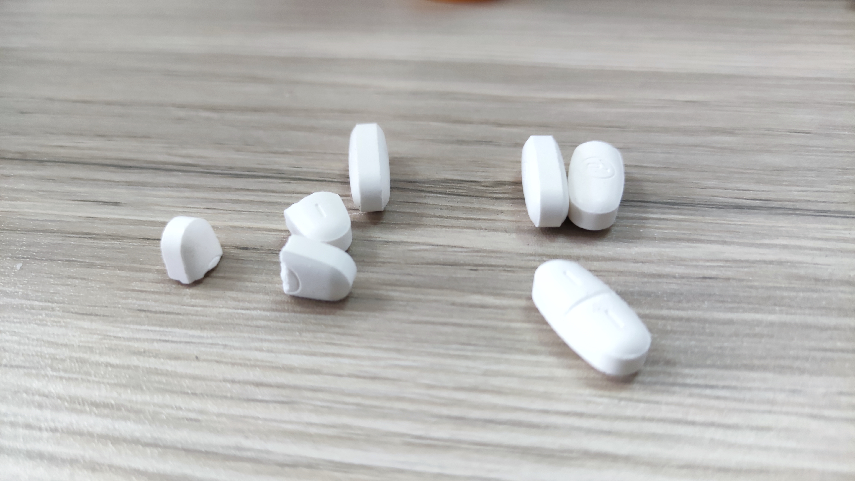
cv/Dataset/p17.jpg
