Benedict-Bsl/SmartCap/cv/Dataset/p18.jpg

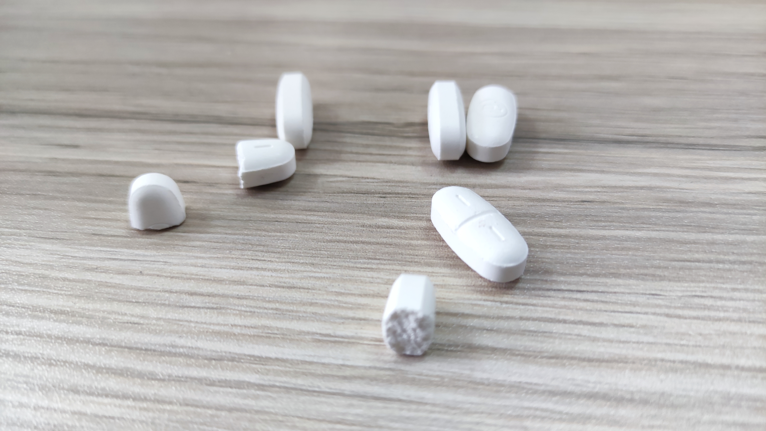
cv/Dataset/p18.jpg
