Benedict-Bsl/SmartCap/cv/Dataset/p19.jpg

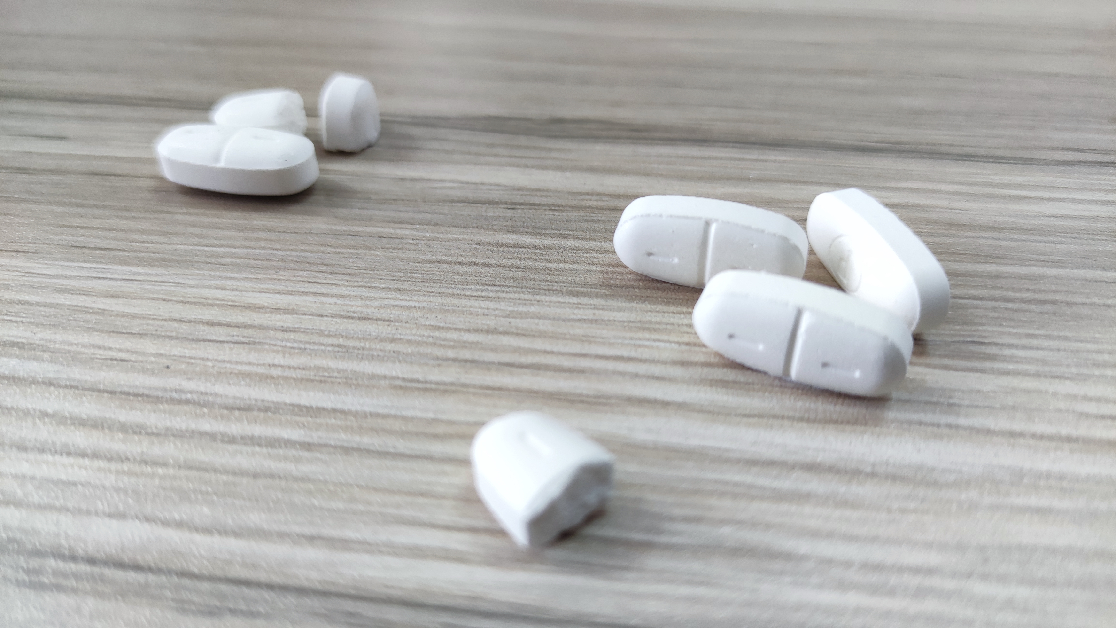
cv/Dataset/p19.jpg
