Benedict-Bsl/SmartCap/cv/Dataset/p22.jpg

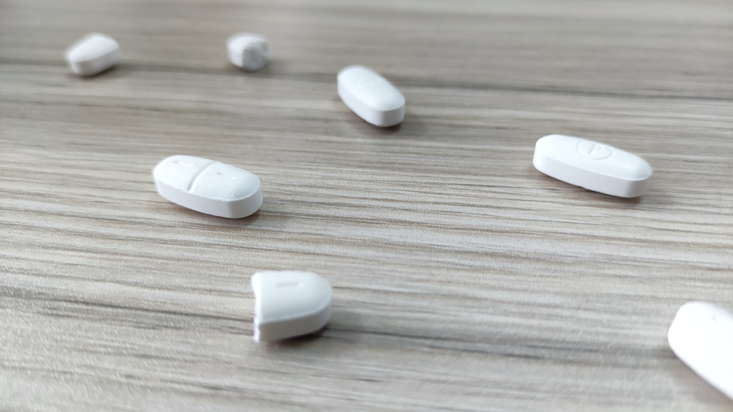
cv/Dataset/p22.jpg
