Benedict-Bsl/SmartCap/cv/Dataset/p23.jpg

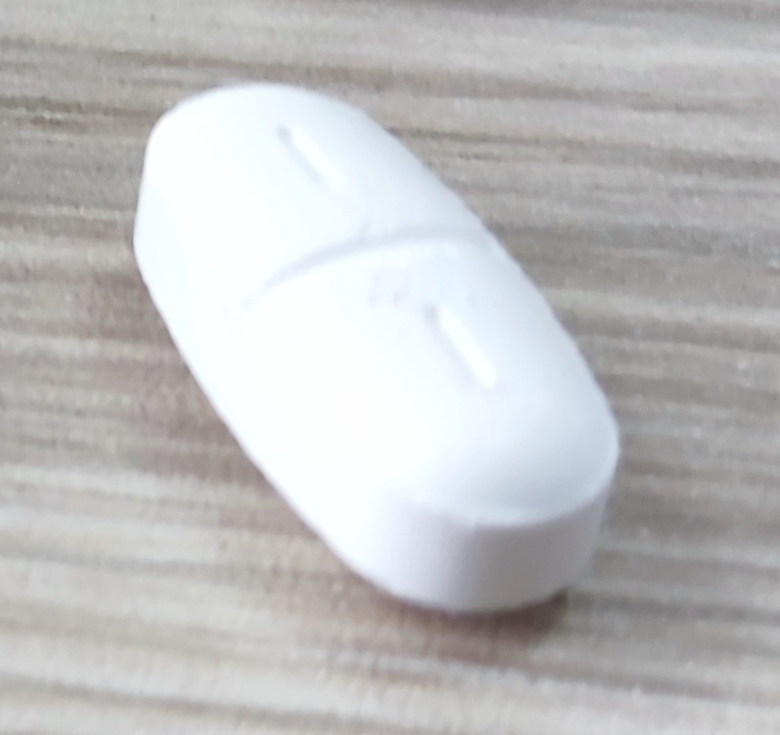
cv/Dataset/p23.jpg
