Benedict-Bsl/SmartCap/cv/Dataset/p24.jpg

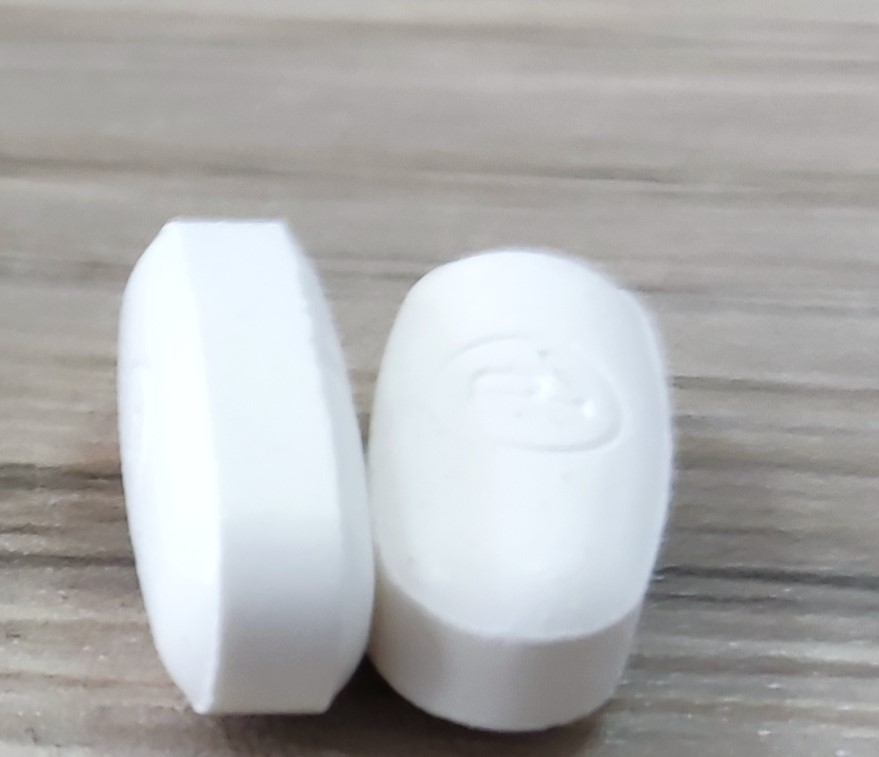
cv/Dataset/p24.jpg
