Benedict-Bsl/SmartCap/cv/Dataset/p25.jpg

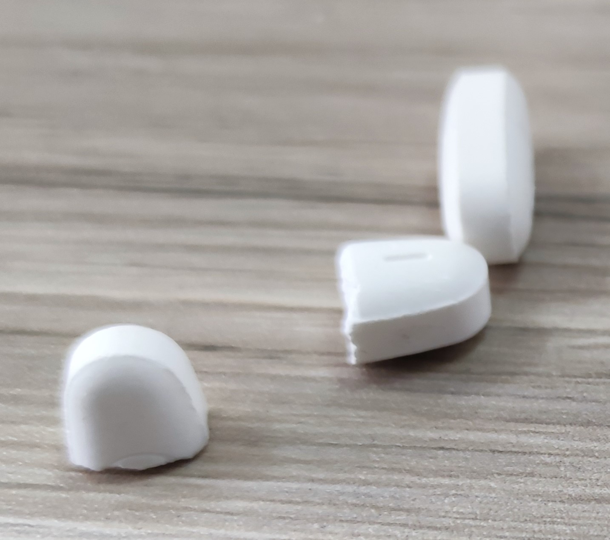
cv/Dataset/p25.jpg
