Benedict-Bsl/SmartCap/cv/Dataset/p26.jpg

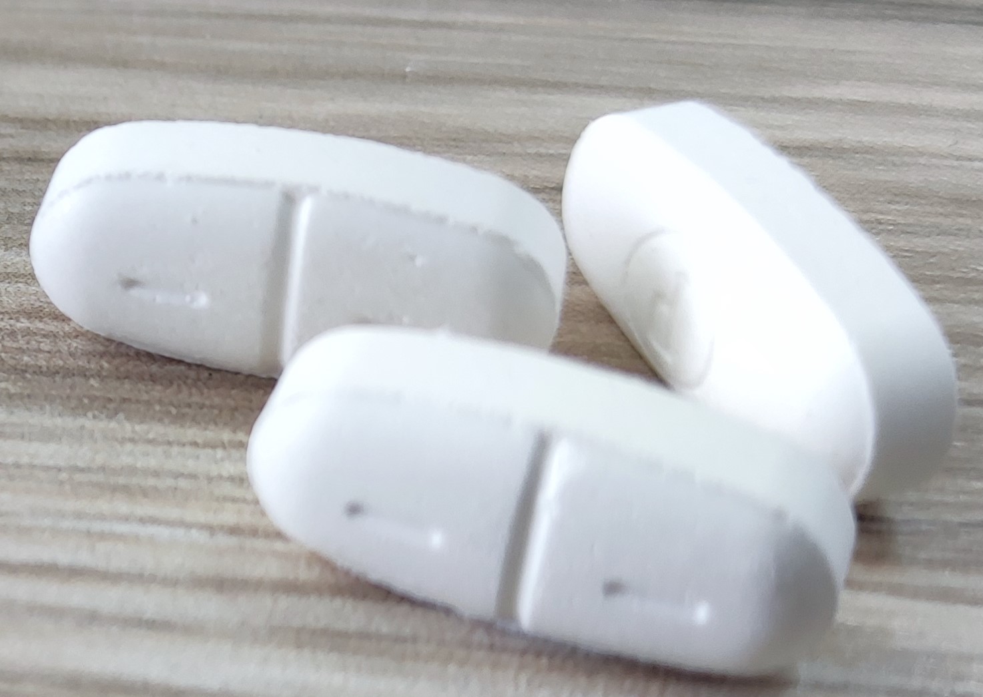
cv/Dataset/p26.jpg
