Benedict-Bsl/SmartCap/cv/Dataset/p27.jpg

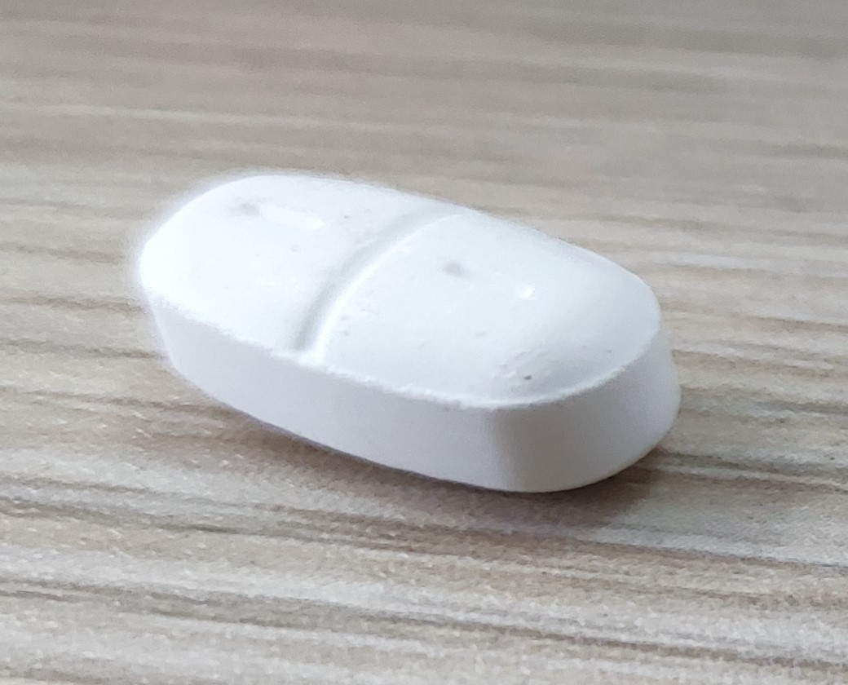
cv/Dataset/p27.jpg
