Benedict-Bsl/SmartCap/cv/Dataset/p28.jpg

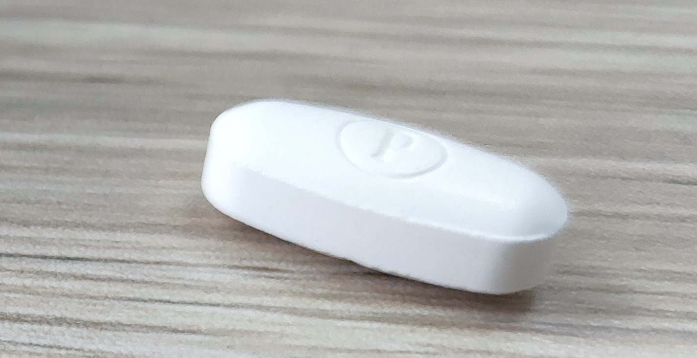
cv/Dataset/p28.jpg
