Benedict-Bsl/SmartCap/cv/Dataset/p29.jpg

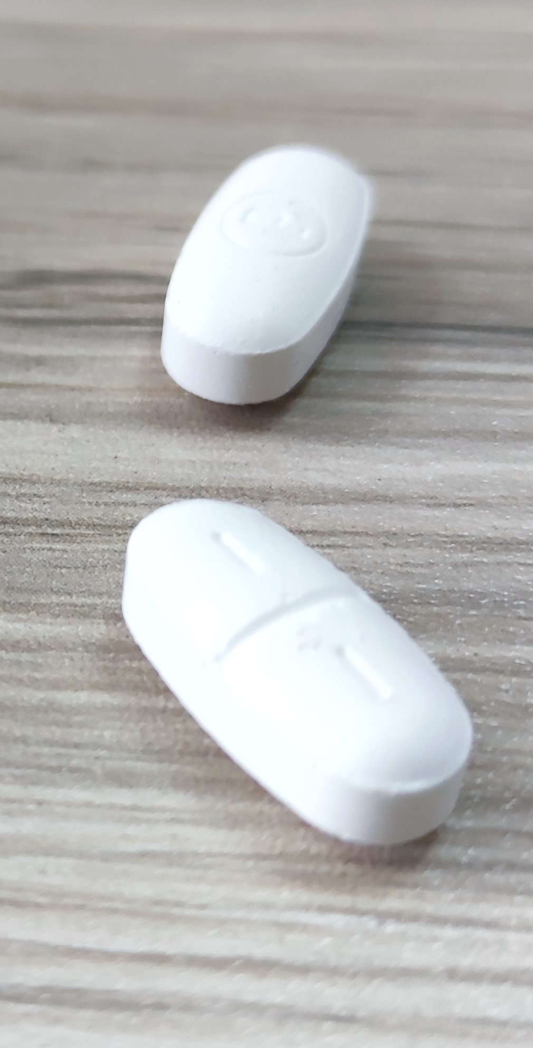
cv/Dataset/p29.jpg
