Benedict-Bsl/SmartCap/cv/Dataset/p30.jpg

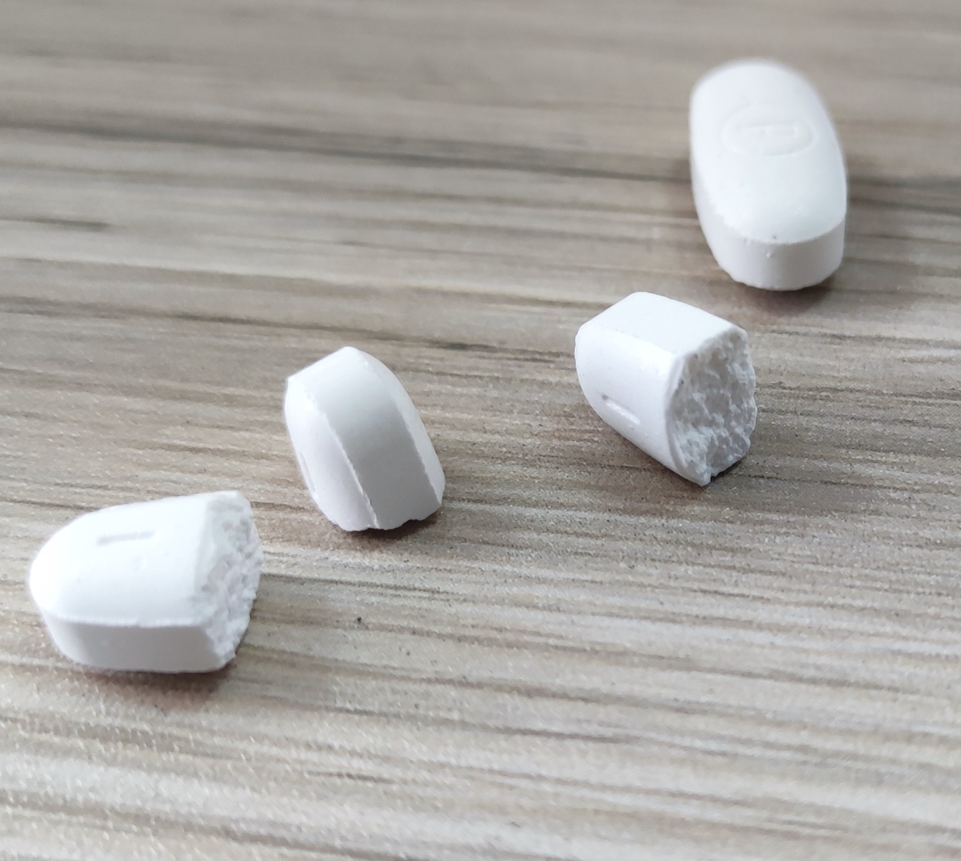
cv/Dataset/p30.jpg
