Benedict-Bsl/SmartCap/SmartCap.jpg

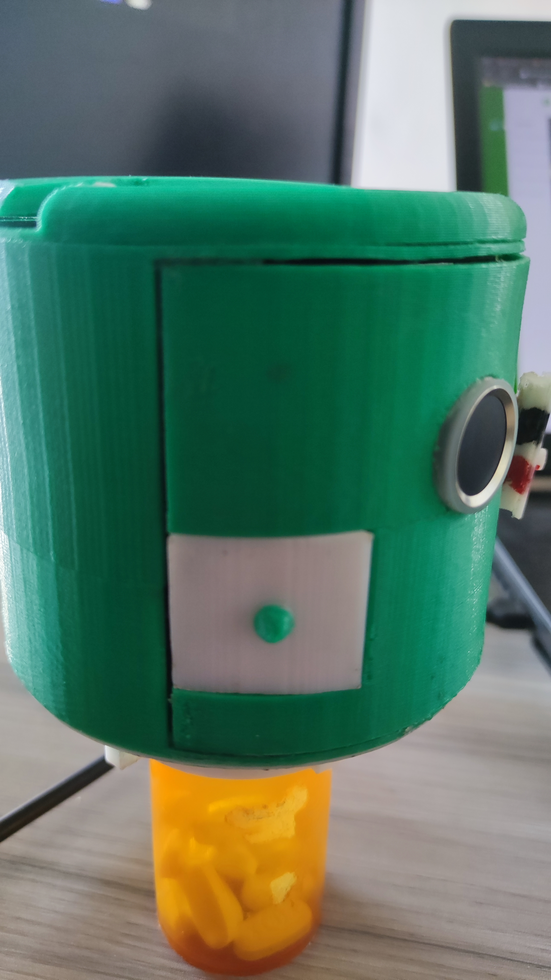
SmartCap.jpg
