Benedict-Bsl/SmartCap/Designs/Designs/Thursday 13 04 2022/Backup (5) of Assem2.SLDASM

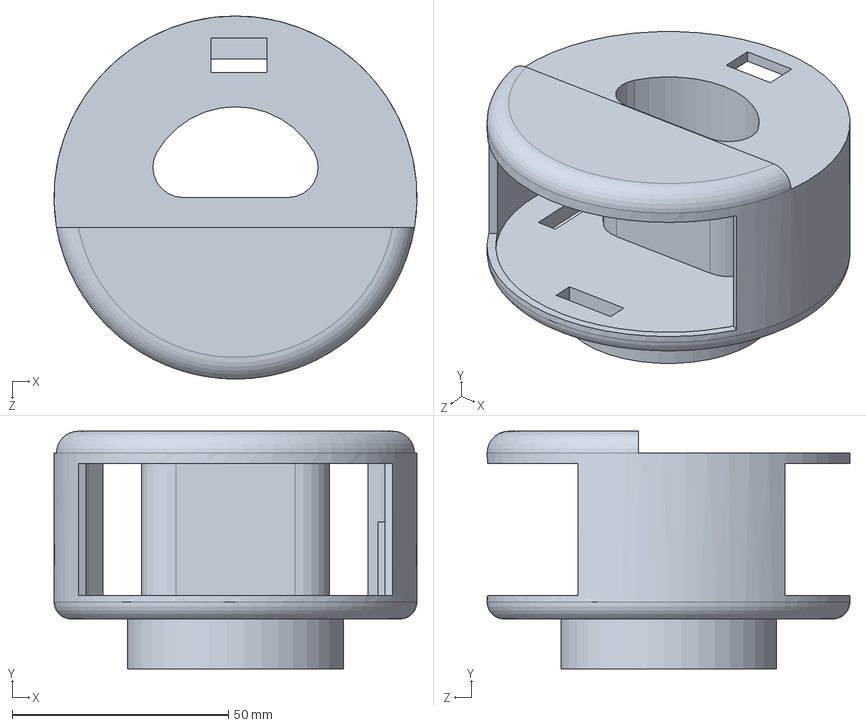
[picture p123: CAD file, 2022-04-26]
Designs/Designs/Thursday 13 04 2022/Backup (5) of Assem2.SLDASM
84.0 x 55.0 x 84.0 mm
