Benedict-Bsl/SmartCap/Designs/Designs/Assemblies/Backup (4) of Hinge_Assem1.SLDASM

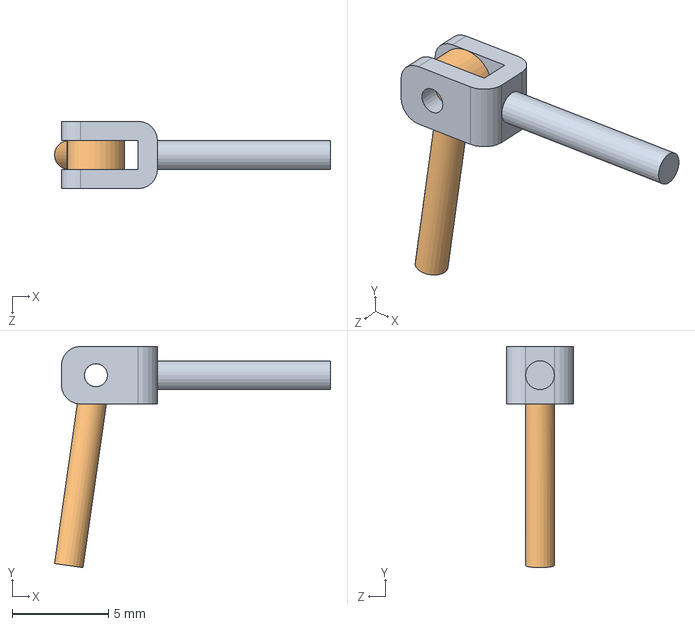
[picture p124: CAD file, 2022-04-26]
Designs/Designs/Assemblies/Backup (4) of Hinge_Assem1.SLDASM
14.4 x 11.5 x 3.50 mm
hinge2
hinge1
