Benedict-Bsl/SmartCap/Designs/STL files/Usable/Backup (1) of Assembly_4Dft&fp.SLDASM

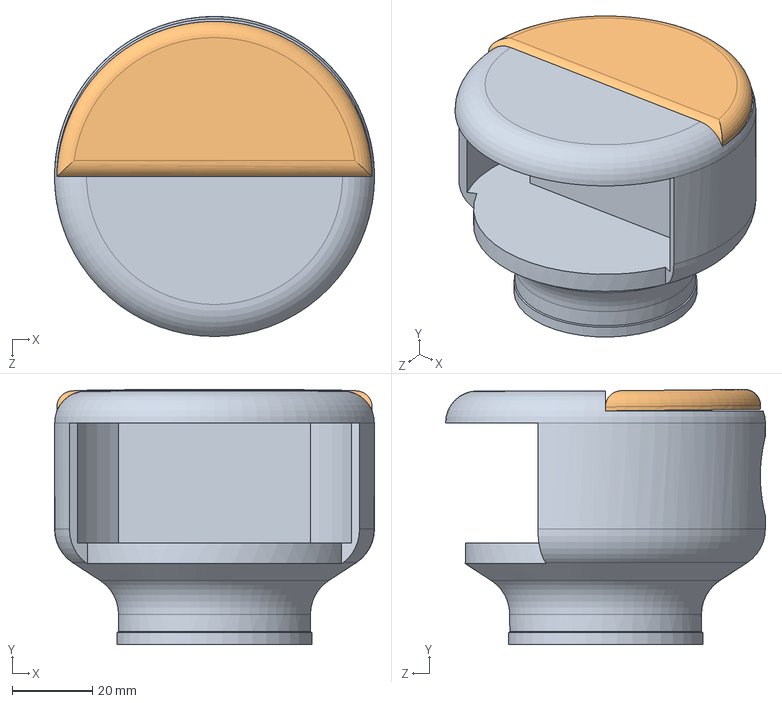
[picture p125: CAD file, 2022-03-20]
Designs/STL files/Usable/Backup (1) of Assembly_4Dft&fp.SLDASM
80.0 x 63.8 x 80.0 mm
CupVersion4D6_withLocksM_2_fp&mt
TopFor_VErsion4D_fp&mt
