Benedict-Bsl/SmartCap/Designs/Designs/STL files/New/Backup (1) of Rectractor_Assembly1.SLDASM

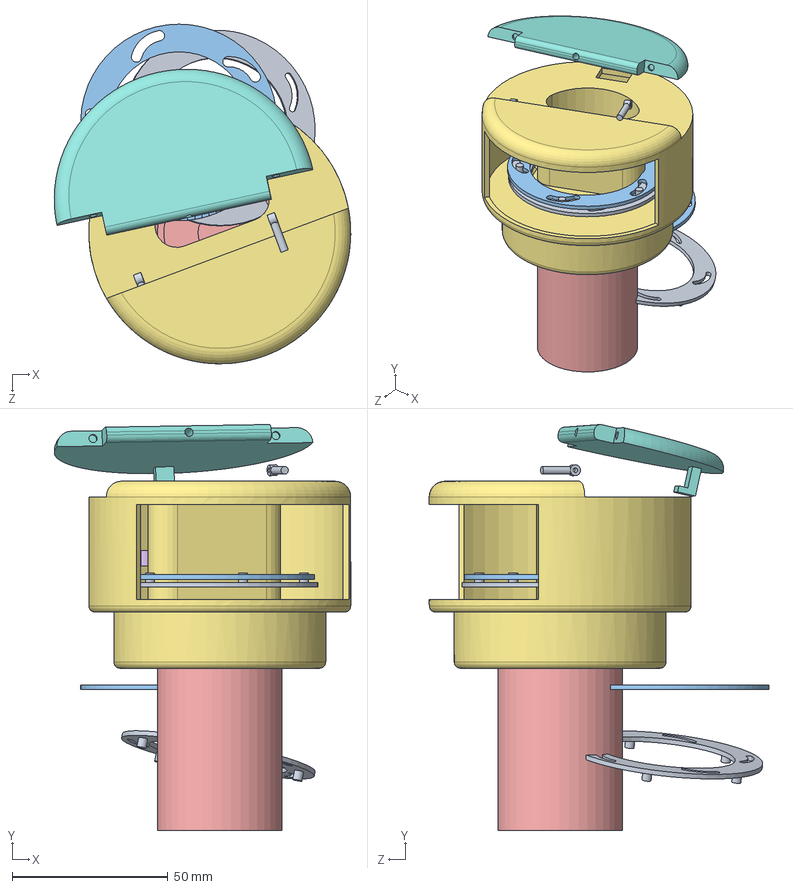
[picture p126: CAD file, 2022-04-26]
Designs/Designs/STL files/New/Backup (1) of Rectractor_Assembly1.SLDASM
95.1 x 130.2 x 108.9 mm
retractable2 x 2
Retractee
retractable_rotator x 2
Rectrator_holder
Bottle)design
MotorThread
CapDesign_Version2
UP_lock_CapDesign_Version2
hinge1 x 2
