Benedict-Bsl/SmartCap/Designs/Designs/Monday 04 04 2022/Assem1.SLDASM

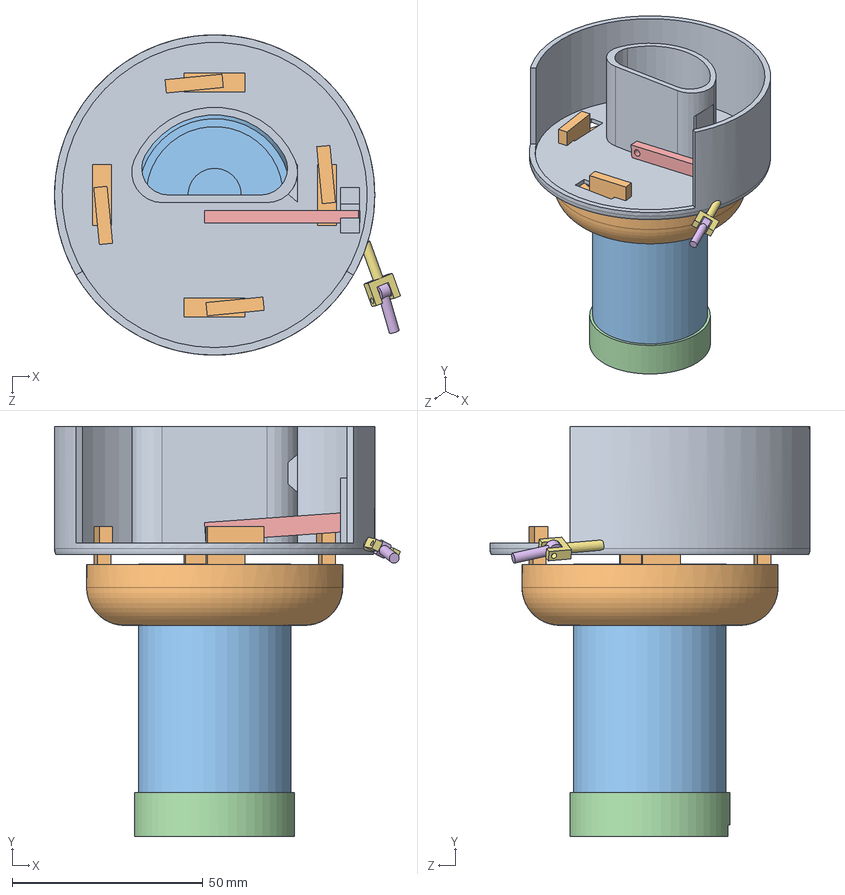
[picture p127: CAD file, 2022-04-26]
Designs/Designs/Monday 04 04 2022/Assem1.SLDASM
90.7 x 107.5 x 84.0 mm
CapDesign_Version5
Bottle)design
LockInside
