Benedict-Bsl/SmartCap/Designs/Designs/Assemblies/Backup (9) of Assem_With_Top_lockMechanism.SLDASM

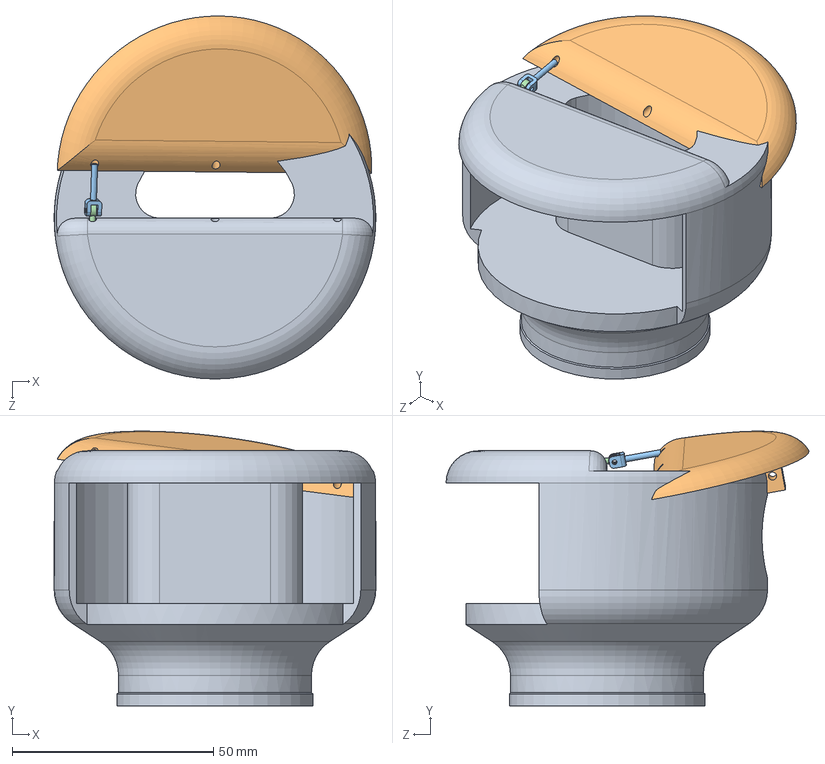
[picture p128: CAD file, 2022-04-26]
Designs/Designs/Assemblies/Backup (9) of Assem_With_Top_lockMechanism.SLDASM
80.0 x 68.3 x 90.3 mm
CupVersion4D6_withLocksM_2_fp&mt
Top_LockMechan_CupVersion4D6_withLocksM_2_fp&mt
hinge2
hinge1
