Benedict-Bsl/SmartCap/Designs/Designs/Thursday 13 04 2022/Backup (1) of Assem2.SLDASM

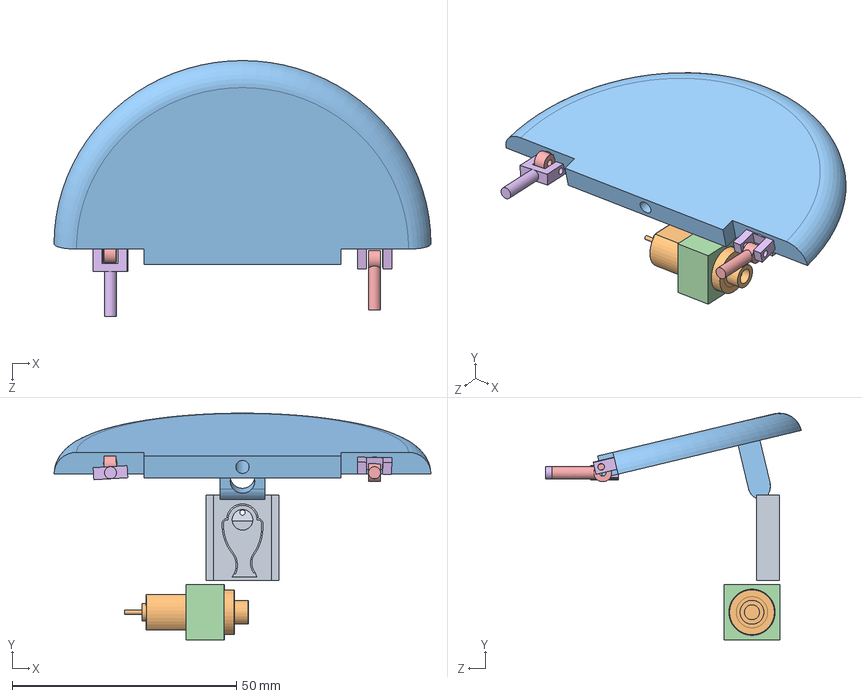
[picture p129: CAD file, 2022-04-26]
Designs/Designs/Thursday 13 04 2022/Backup (1) of Assem2.SLDASM
84.0 x 50.5 x 57.0 mm
a
servoMotor_A35A703
UP_lock_CapDesign_Version6
Holder_servoMotor_A35A703
