Benedict-Bsl/SmartCap/Designs/Tuesday 15 06 2022/Assem5_bigWithCam.SLDASM

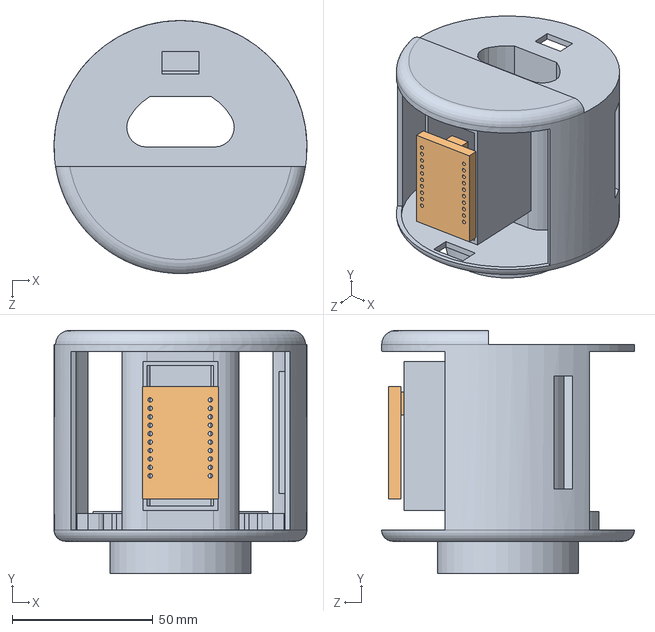
[picture p130: CAD file, 2022-06-18]
Designs/Tuesday 15 06 2022/Assem5_bigWithCam.SLDASM
90.0 x 86.5 x 90.0 mm
bigger_cap5
esp32Cam
