Benedict-Bsl/SmartCap/Designs/Tuesday10 05 2022/Assem2.SLDASM

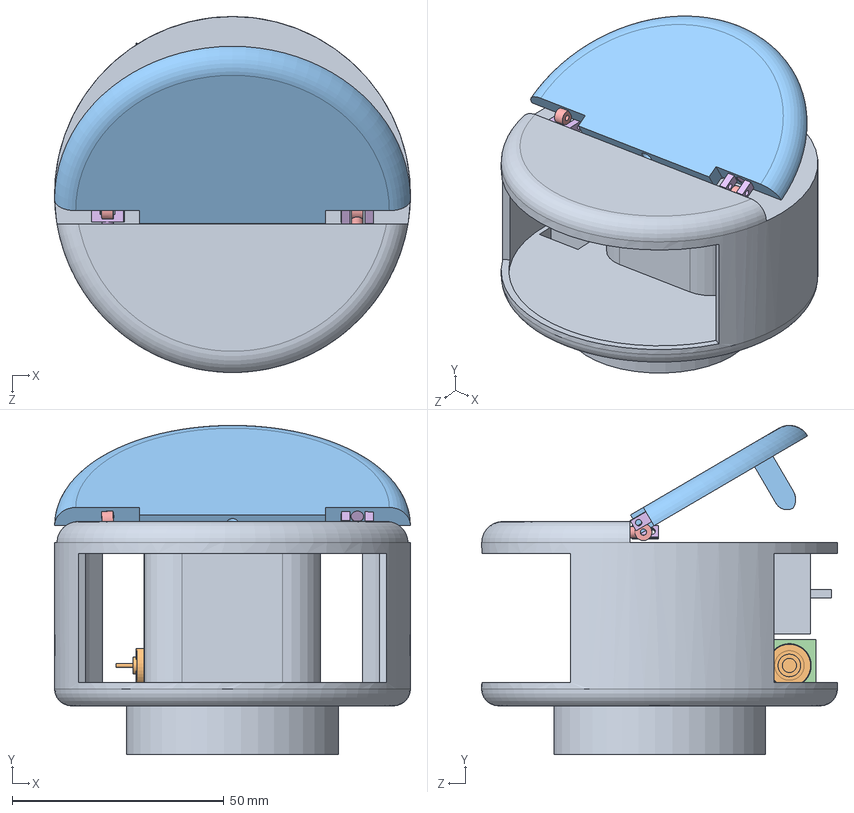
[picture p131: CAD file, 2022-05-22]
Designs/Tuesday10 05 2022/Assem2.SLDASM
84.0 x 77.7 x 84.0 mm
a
servoMotor_A35A703
UP_lock_CapDesign_Version6
Holder_servoMotor_A35A703
