Benedict-Bsl/SmartCap/Designs/Designs/Assemblies/Backup (3) of Hinge_Assem1.SLDASM

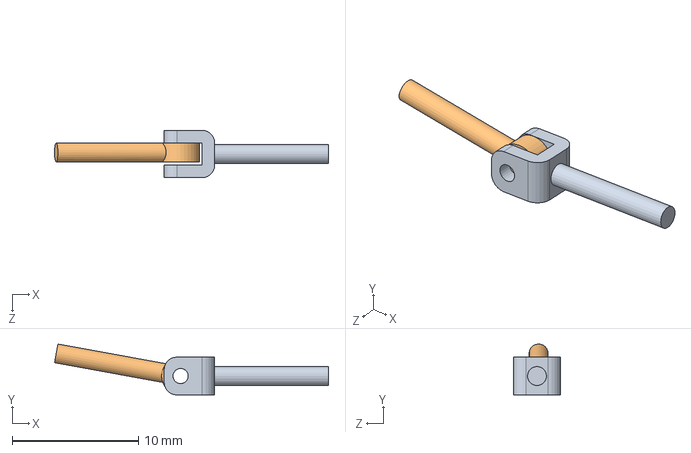
[picture p134: CAD file, 2022-04-26]
Designs/Designs/Assemblies/Backup (3) of Hinge_Assem1.SLDASM
21.7 x 4.03 x 3.75 mm
hinge2
hinge1
