Benedict-Bsl/SmartCap/Designs/Designs/Assemblies/Backup (1) of Hinge_Assem1.SLDASM

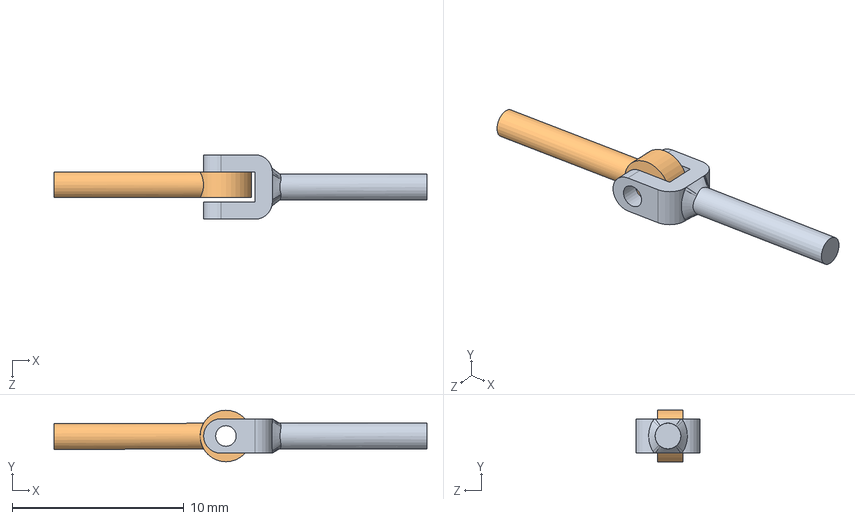
[picture p135: CAD file, 2022-04-26]
Designs/Designs/Assemblies/Backup (1) of Hinge_Assem1.SLDASM
21.7 x 3.00 x 3.75 mm
hinge2
hinge1
