Benedict-Bsl/SmartCap/Designs/Designs/Assemblies/Backup (8) of Assem_With_Top_lockMechanism.SLDASM

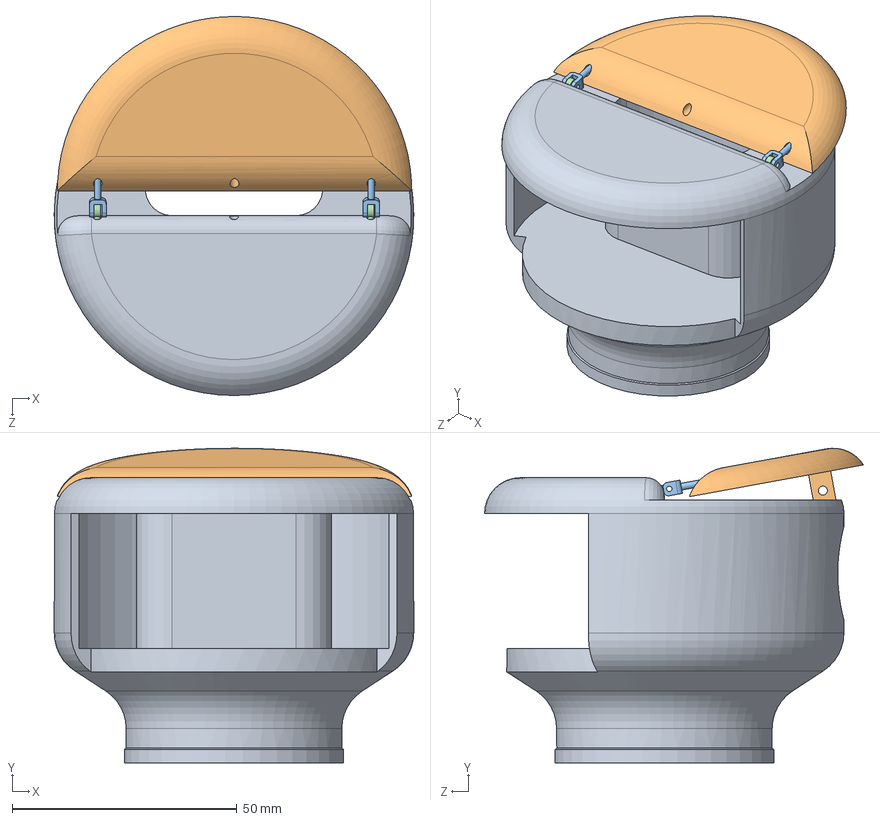
[picture p136: CAD file, 2022-04-26]
Designs/Designs/Assemblies/Backup (8) of Assem_With_Top_lockMechanism.SLDASM
80.0 x 70.0 x 84.3 mm
CupVersion4D6_withLocksM_2_fp&mt
Top_LockMechan_CupVersion4D6_withLocksM_2_fp&mt
hinge2 x 2
hinge1 x 2
