Benedict-Bsl/SmartCap/Designs/Designs/Assemblies/Version4D_Assembly1.SLDASM

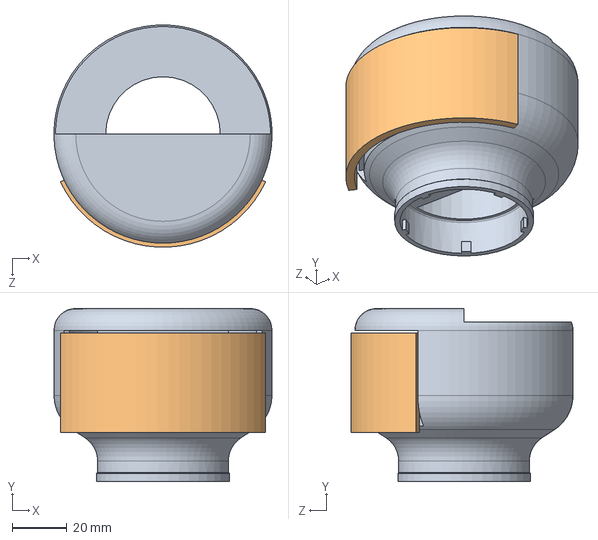
[picture p137: CAD file, 2022-03-20]
Designs/Designs/Assemblies/Version4D_Assembly1.SLDASM
79.9 x 63.4 x 81.4 mm
CupVersion4D6_withLocksM
SideCoverFor_CupVersion4D6
