Benedict-Bsl/SmartCap/Designs/Designs/Assemblies/CapVersion4_complete.SLDASM

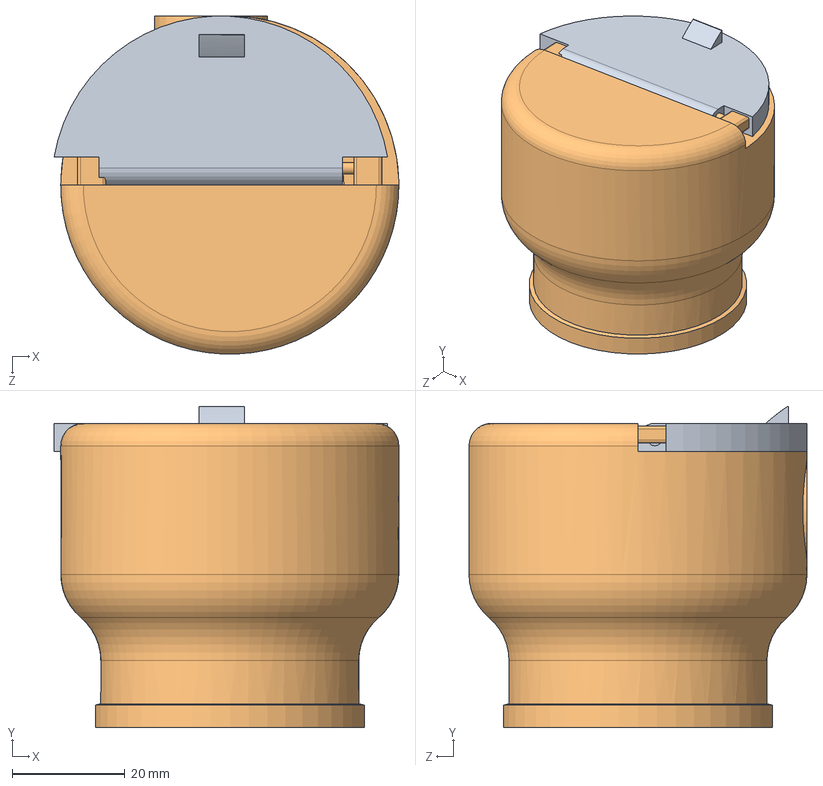
[picture p138: CAD file, 2022-03-13]
Designs/Designs/Assemblies/CapVersion4_complete.SLDASM
61.2 x 57.0 x 60.0 mm
CupOpenPopSideFv4C
CupVersion4C
