Benedict-Bsl/SmartCap/Designs/Designs/Assemblies/Assem1_OP.SLDASM

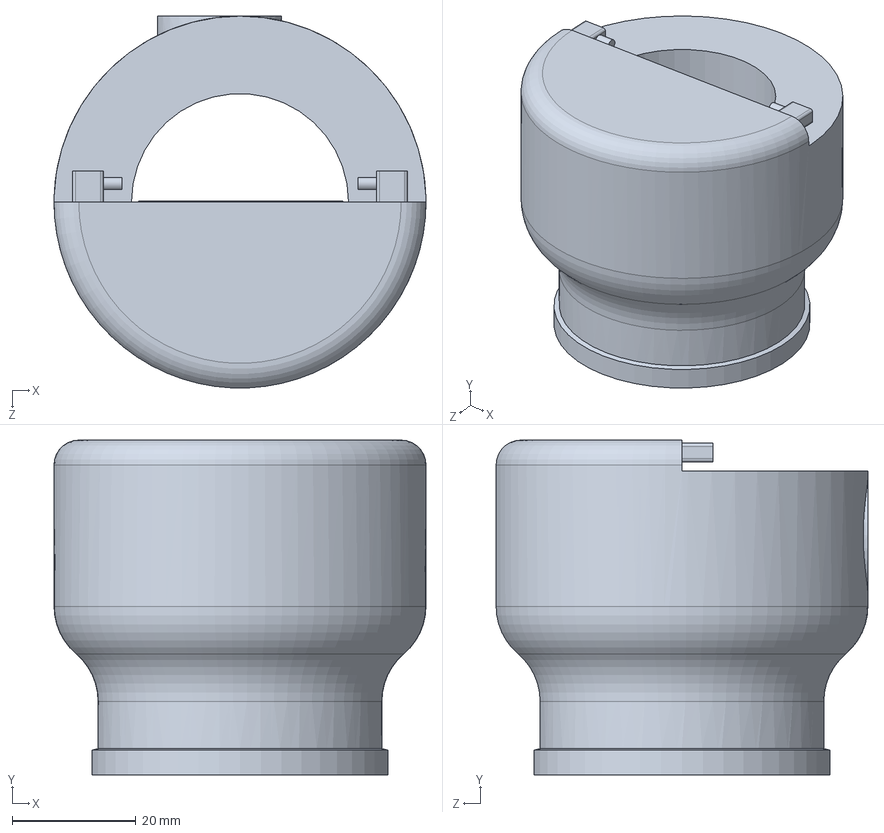
[picture p139: CAD file, 2022-03-13]
Designs/Designs/Assemblies/Assem1_OP.SLDASM
60.0 x 54.0 x 60.0 mm
CupVersion4C2
Gsm_moduleGPRS
wifi_module_esp8266
Arduino_Nano
