Benedict-Bsl/SmartCap/Designs/CupVersion4D6_withLocksM_2_fp&mt.SLDPRT

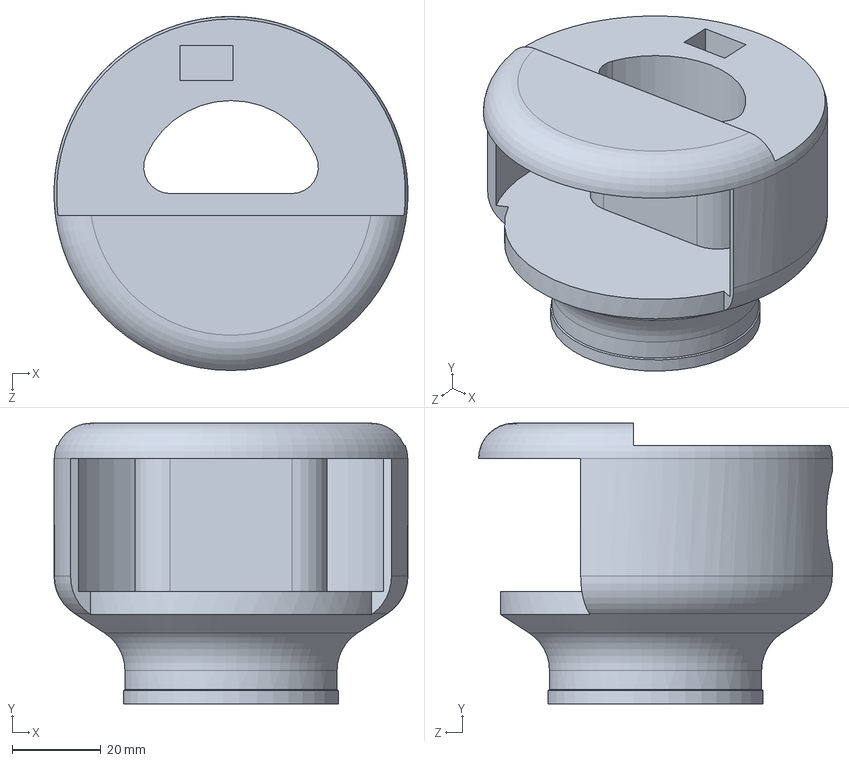
[picture p140: CAD file, 2022-05-06]
Designs/CupVersion4D6_withLocksM_2_fp&mt.SLDPRT
80.0 x 63.4 x 80.0 mm
