Benedict-Bsl/SmartCap/Designs/Designs/Idea_last_before_last/rectractee_.SLDPRT

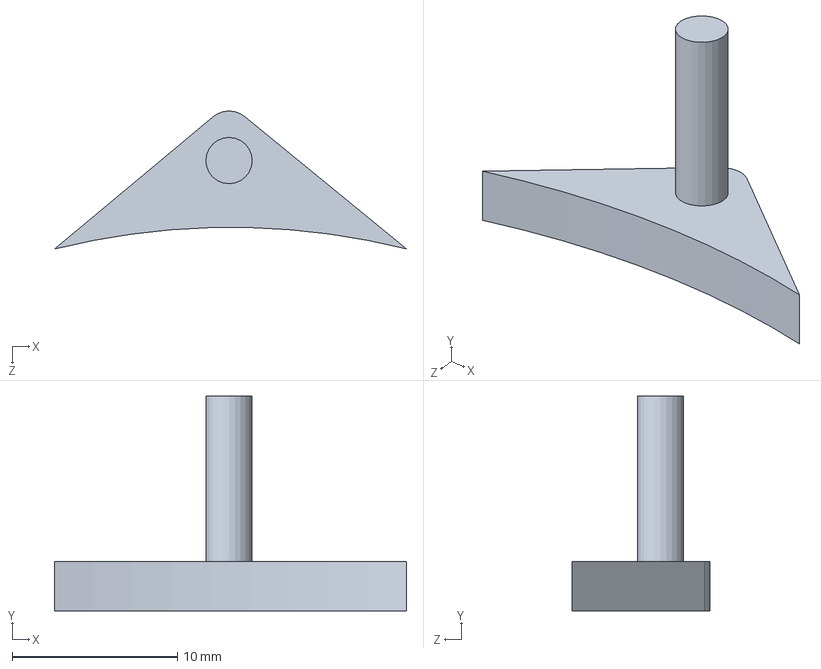
[picture p141: CAD file, 2022-04-26]
Designs/Designs/Idea_last_before_last/rectractee_.SLDPRT
21.3 x 13.0 x 8.35 mm
