Benedict-Bsl/SmartCap/Designs/Designs/Locking/New/lockee2.STL

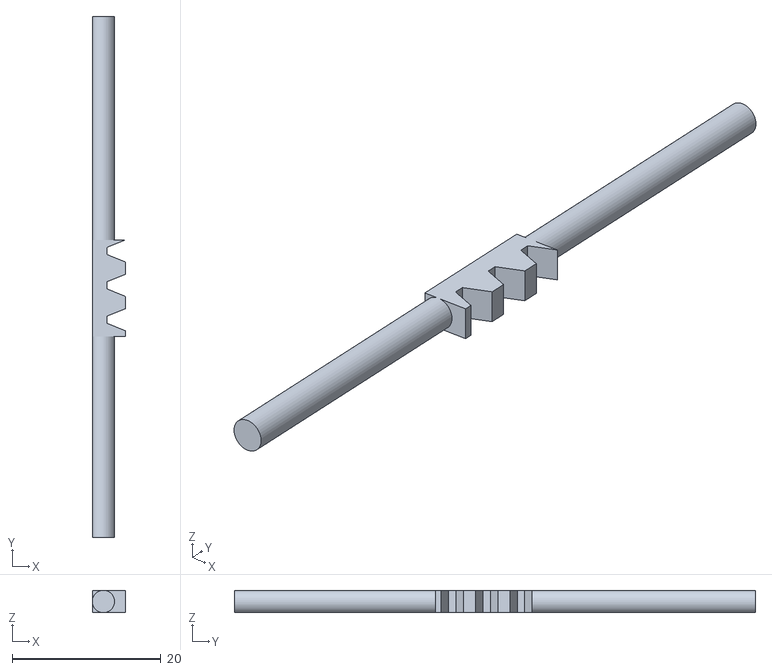
[picture p142: CAD file, 2022-04-26]
Designs/Designs/Locking/New/lockee2.STL
4.50 x 70.0 x 3.00
