Benedict-Bsl/SmartCap/Designs/Designs/Locking/Top_LockMechan_CupVersion4D6_withLocksM_2_fp&mt.SLDPRT

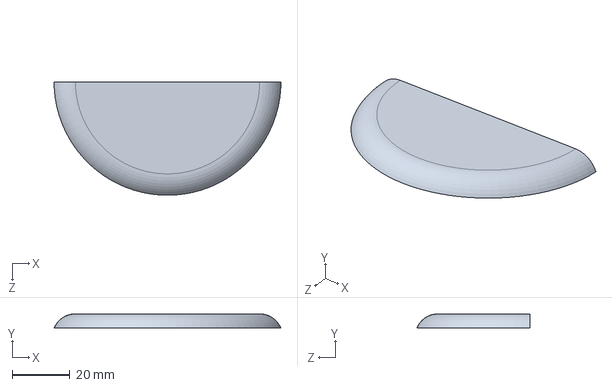
[picture p143: CAD file, 2022-05-06]
Designs/Designs/Locking/Top_LockMechan_CupVersion4D6_withLocksM_2_fp&mt.SLDPRT
78.8 x 5.00 x 39.4 mm
