Benedict-Bsl/SmartCap/Designs/Designs/Monday 04 04 2022/Part001B_bevel.STL

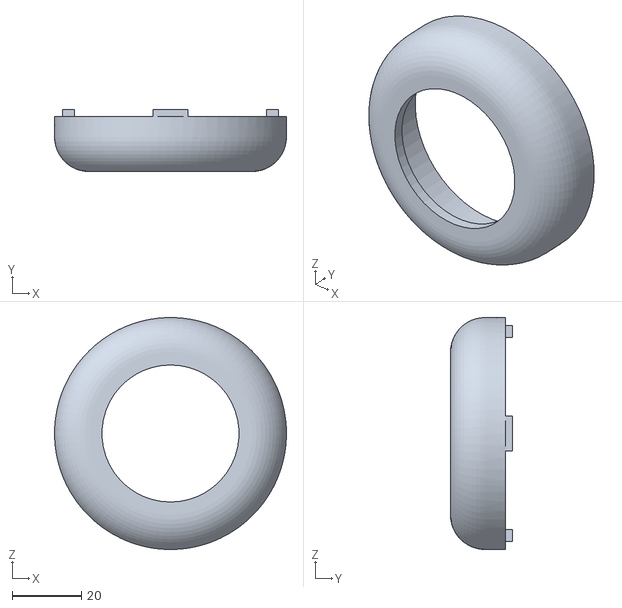
[picture p144: CAD file, 2022-04-26]
Designs/Designs/Monday 04 04 2022/Part001B_bevel.STL
67.2 x 18.0 x 67.2
