Benedict-Bsl/SmartCap/Designs/Designs/Monday 25 04 2022/locks_bottom_2.SLDPRT

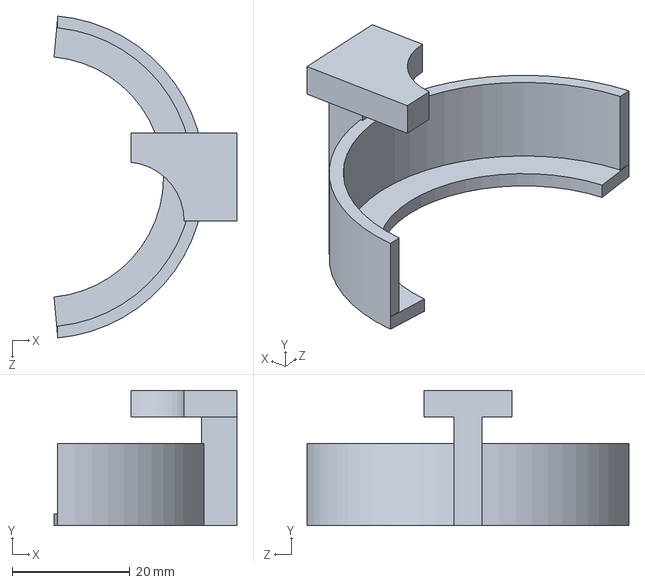
[picture p145: CAD file, 2022-05-22]
Designs/Designs/Monday 25 04 2022/locks_bottom_2.SLDPRT
31.1 x 23.0 x 54.8 mm
