Benedict-Bsl/SmartCap/Designs/Designs/New cap Design/CapDesign_Version2Down.SLDPRT

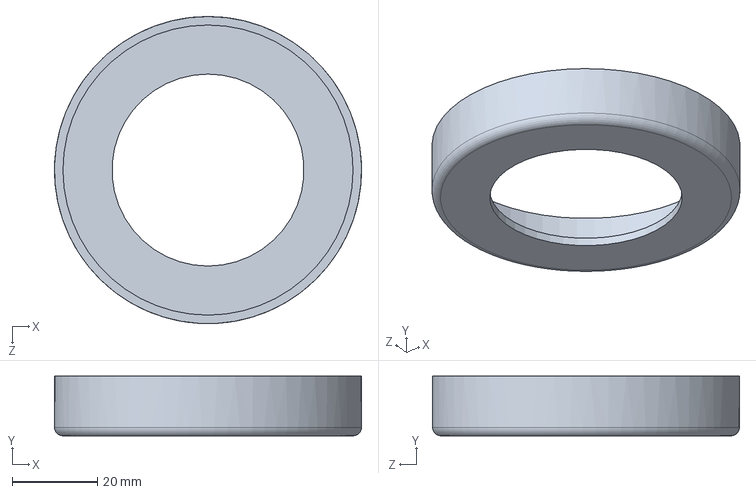
[picture p146: CAD file, 2022-04-26]
Designs/Designs/New cap Design/CapDesign_Version2Down.SLDPRT
72.0 x 14.0 x 72.0 mm
