Benedict-Bsl/SmartCap/Designs/Designs/New cap Design/stl/2 CapDesign_Version2.STL

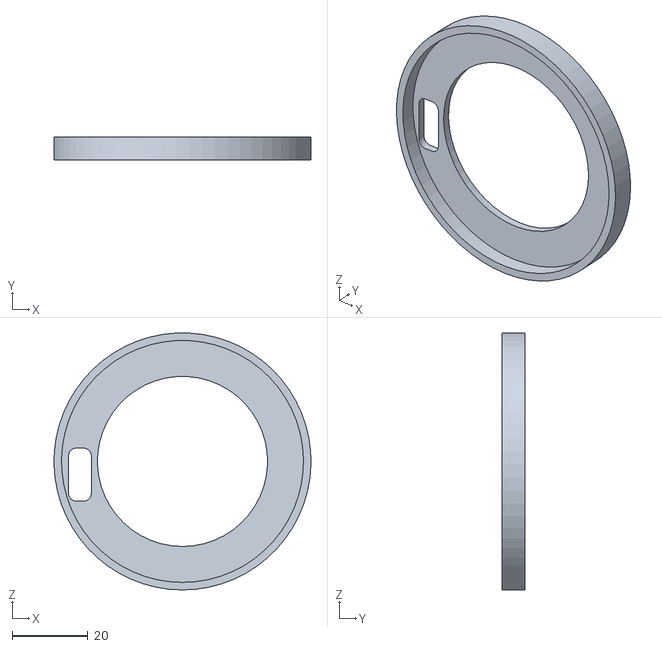
[picture p147: CAD file, 2022-04-26]
Designs/Designs/New cap Design/stl/2 CapDesign_Version2.STL
68.0 x 6.00 x 68.0
