Benedict-Bsl/SmartCap/Designs/Designs/STL files/New/retractable_anOtherOne.SLDPRT

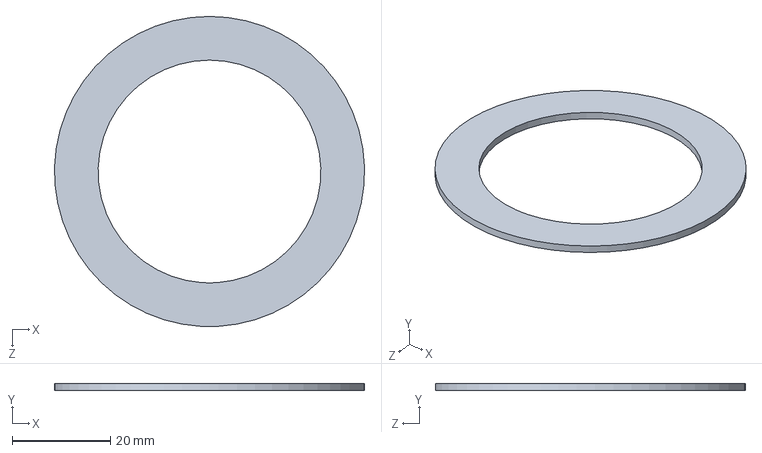
[picture p148: CAD file, 2022-04-26]
Designs/Designs/STL files/New/retractable_anOtherOne.SLDPRT
63.0 x 1.50 x 63.0 mm
