Benedict-Bsl/SmartCap/Designs/Designs/STL files/UP_lock_CapDesign_Version2.STL

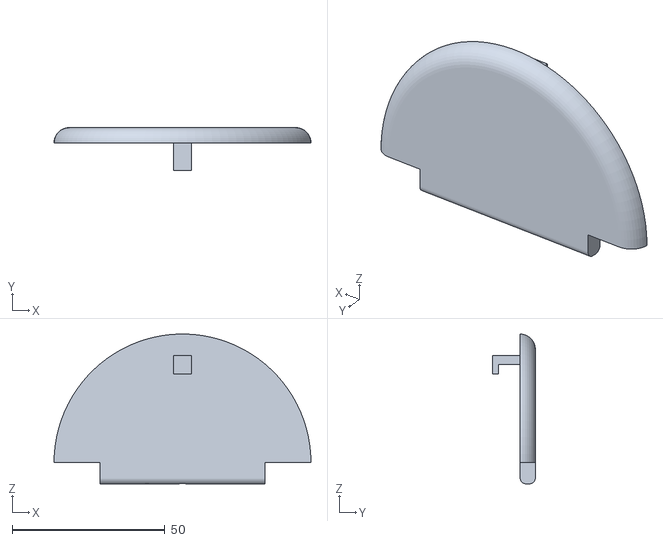
[picture p149: CAD file, 2022-04-26]
Designs/Designs/STL files/UP_lock_CapDesign_Version2.STL
84.0 x 14.0 x 49.0
