Benedict-Bsl/SmartCap/Designs/Designs/Thursday 13 04 2022/STL/a.SLDPRT

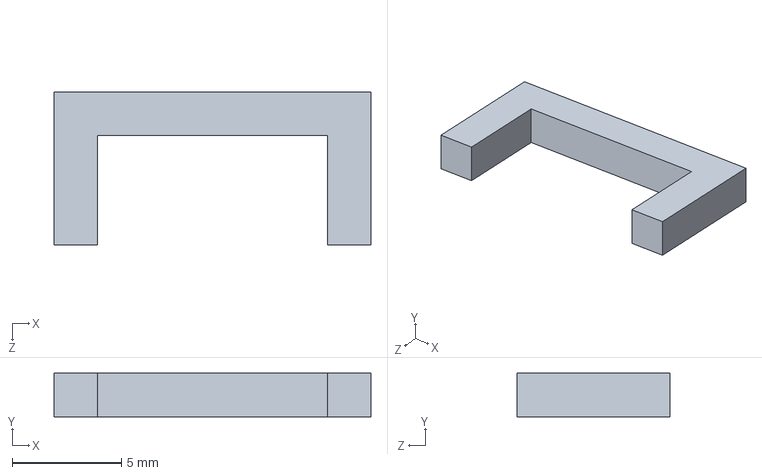
[picture p150: CAD file, 2022-05-22]
Designs/Designs/Thursday 13 04 2022/STL/a.SLDPRT
14.5 x 2.00 x 7.00 mm
