Benedict-Bsl/SmartCap/Designs/Designs/tuesda 04 05/Motor_HLDPart2.SLDPRT

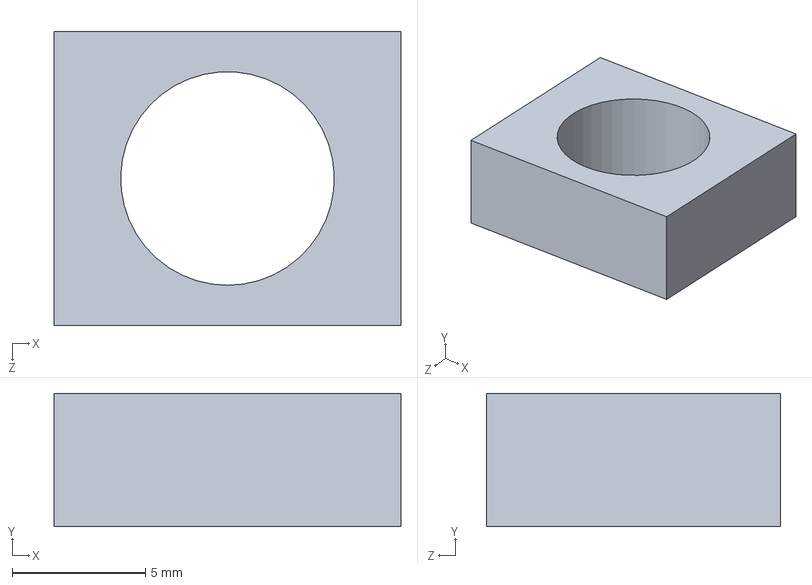
[picture p151: CAD file, 2022-04-26]
Designs/Designs/tuesda 04 05/Motor_HLDPart2.SLDPRT
13.0 x 5.00 x 11.0 mm
