Benedict-Bsl/SmartCap/Designs/Locking/Backup (1) of Top_LockMechan_CupVersion4D6_withLocksM_2_fp&mt.SLDPRT

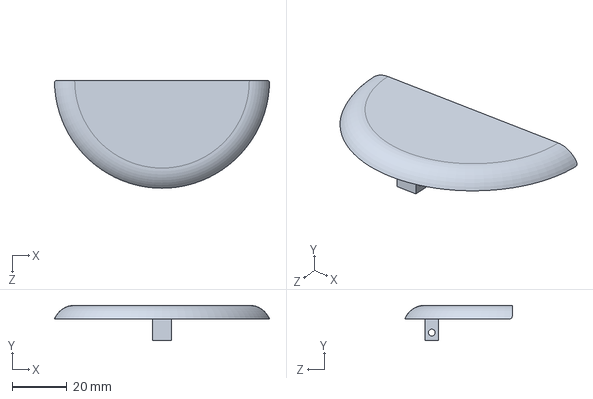
[picture p152: CAD file, 2022-05-06]
Designs/Locking/Backup (1) of Top_LockMechan_CupVersion4D6_withLocksM_2_fp&mt.SLDPRT
78.8 x 13.0 x 39.4 mm
