Benedict-Bsl/SmartCap/Designs/Monday 25 04 2022/stkl/FP_bigger_cap.STL

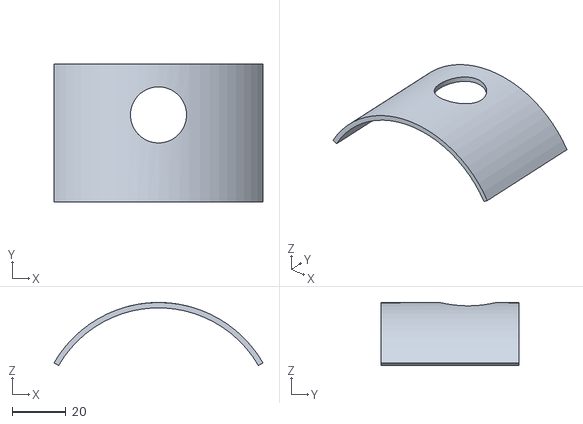
[picture p153: CAD file, 2022-05-06]
Designs/Monday 25 04 2022/stkl/FP_bigger_cap.STL
77.9 x 51.5 x 23.5
