Benedict-Bsl/SmartCap/Designs/STL files/CupVersion4D4.STL

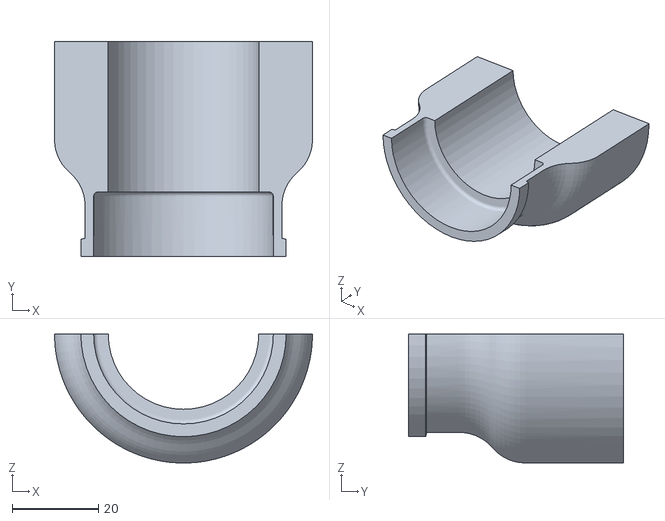
[picture p154: CAD file, 2022-03-20]
Designs/STL files/CupVersion4D4.STL
60.0 x 50.0 x 30.0
