Benedict-Bsl/SmartCap/Designs/STL files/Usable/Up1.STL

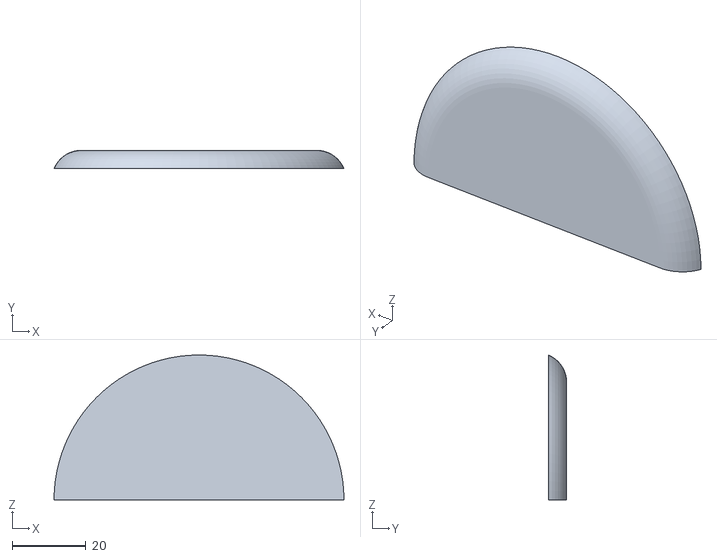
[picture p155: CAD file, 2022-03-20]
Designs/STL files/Usable/Up1.STL
78.8 x 5.00 x 39.4
