Benedict-Bsl/SmartCap/Designs/Thursday 13 04 2022/servoMotor_A35A703.SLDPRT

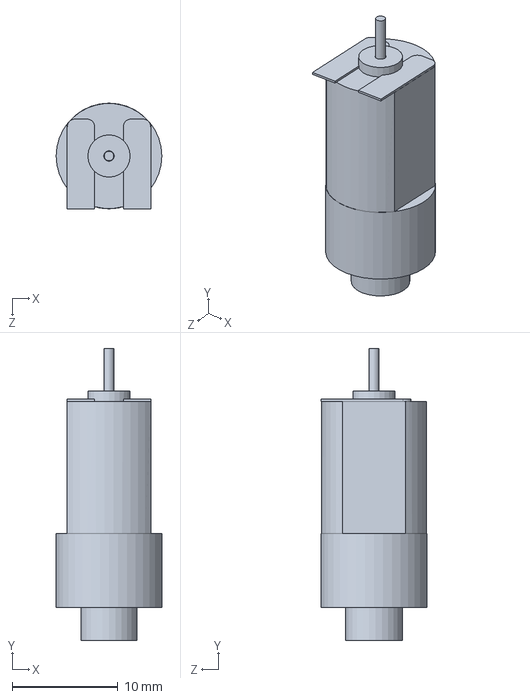
[picture p156: CAD file, 2022-06-18]
Designs/Thursday 13 04 2022/servoMotor_A35A703.SLDPRT
10.0 x 27.6 x 10.0 mm
