Benedict-Bsl/SmartCap/Designs/Tuesday 15 06 2022/Backup (7) of rotatingDisk2.SLDPRT

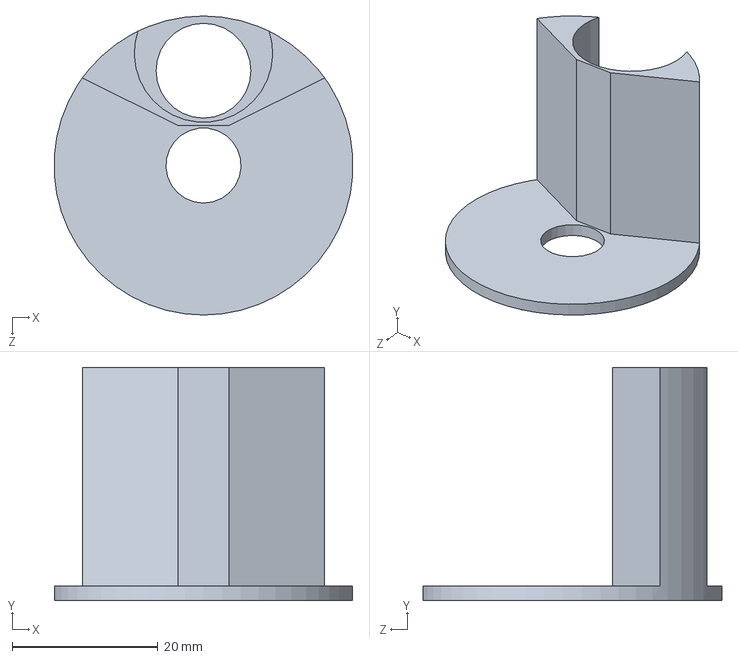
[picture p157: CAD file, 2022-06-18]
Designs/Tuesday 15 06 2022/Backup (7) of rotatingDisk2.SLDPRT
40.9 x 32.0 x 41.0 mm
