Benedict-Bsl/SmartCap/Designs/Tuesday 15 06 2022/STL/2_bigger_cap4_auto_pillDisp.STL

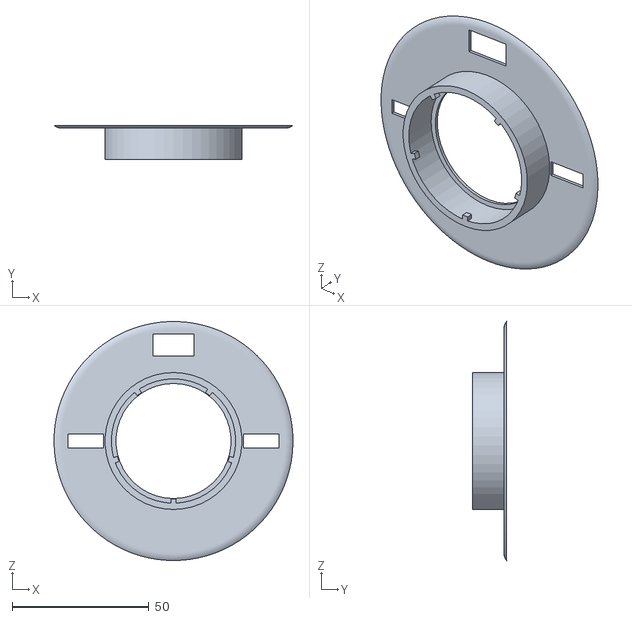
[picture p158: CAD file, 2022-06-18]
Designs/Tuesday 15 06 2022/STL/2_bigger_cap4_auto_pillDisp.STL
87.3 x 12.5 x 87.3
