Benedict-Bsl/SmartCap/Designs/Tuesday10 05 2022/couloir.SLDPRT

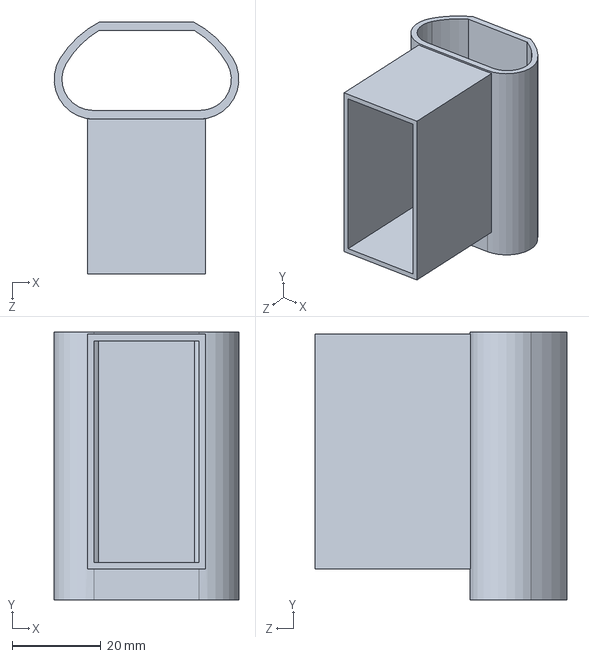
[picture p159: CAD file, 2022-06-18]
Designs/Tuesday10 05 2022/couloir.SLDPRT
41.7 x 60.5 x 57.0 mm
