Benedict-Bsl/SmartCap/Designs/Tuesday10 05 2022/stl/locks_bottom_2.STL

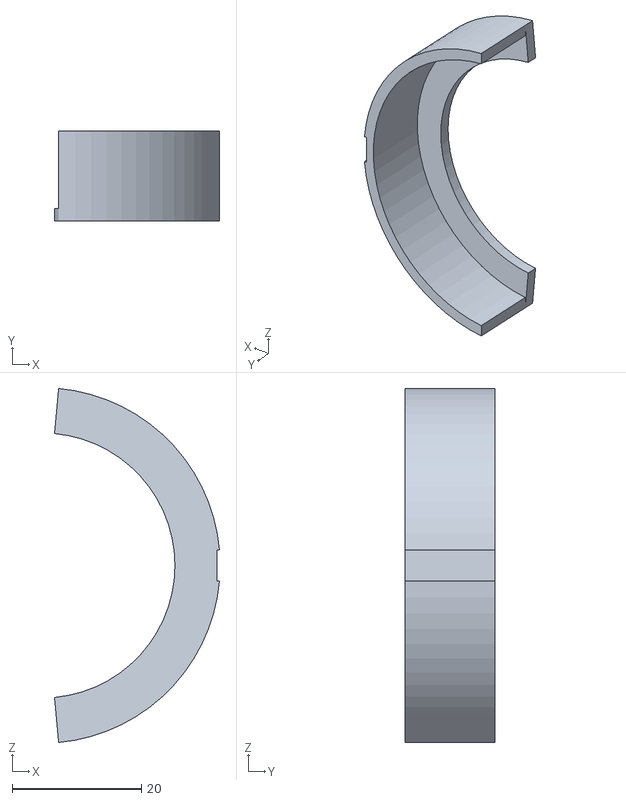
[picture p160: CAD file, 2022-05-22]
Designs/Tuesday10 05 2022/stl/locks_bottom_2.STL
25.5 x 14.0 x 54.8
