Benedict-Bsl/SmartCap/Designs/Designs/Locking/New/MotorThread.SLDPRT

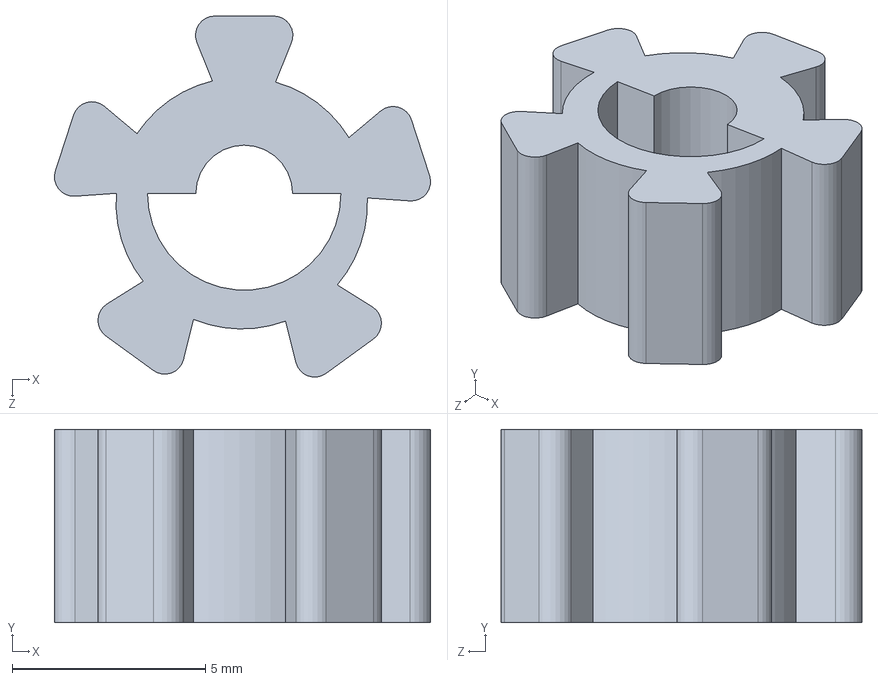
[picture p161: CAD file, 2022-04-26]
Designs/Designs/Locking/New/MotorThread.SLDPRT
9.72 x 5.00 x 9.33 mm
