Benedict-Bsl/SmartCap/Designs/Designs/Monday 04 04 2022/Part001.SLDPRT

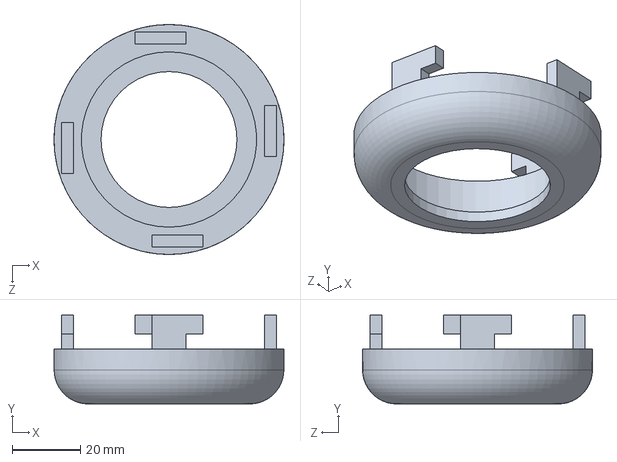
[picture p162: CAD file, 2022-04-26]
Designs/Designs/Monday 04 04 2022/Part001.SLDPRT
67.2 x 26.0 x 67.2 mm
