Benedict-Bsl/SmartCap/Designs/Designs/Monday 25 04 2022/locks_bottom.SLDPRT

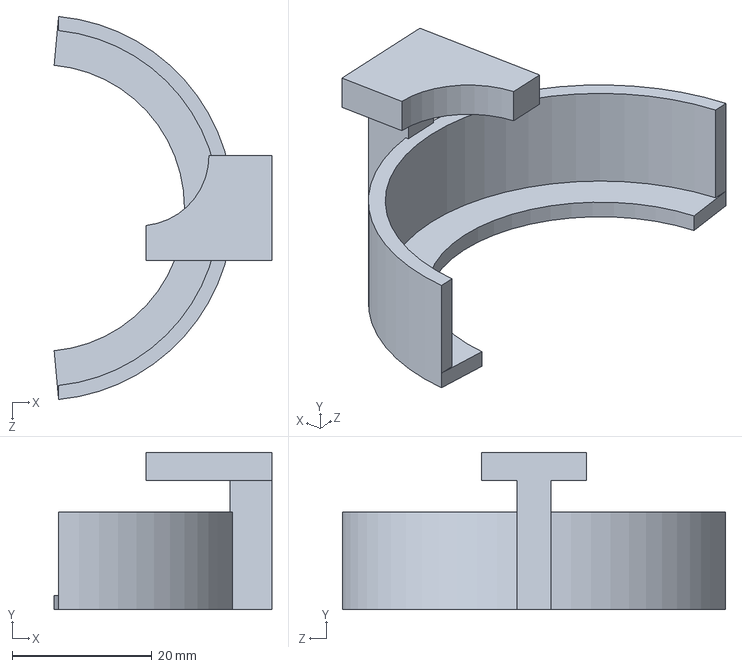
[picture p163: CAD file, 2022-05-22]
Designs/Designs/Monday 25 04 2022/locks_bottom.SLDPRT
31.1 x 22.5 x 54.8 mm
