Benedict-Bsl/SmartCap/Designs/Designs/New cap Design/stl/1FingerPrint_part_CapDesign_Version2.STL

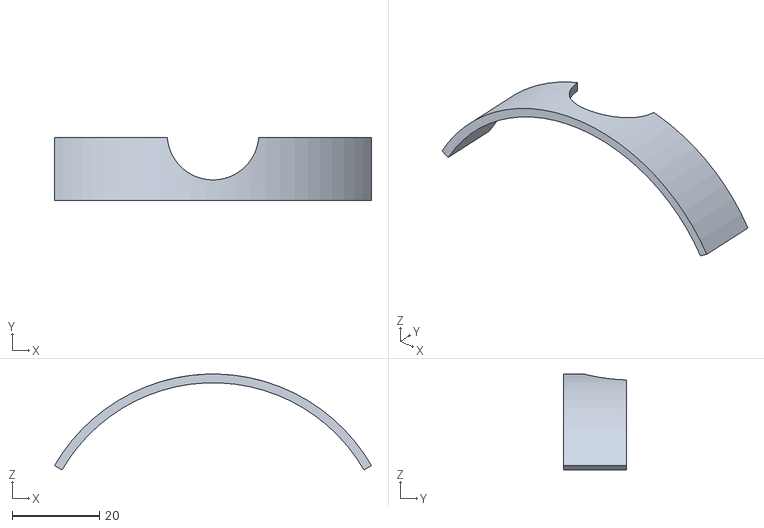
[picture p164: CAD file, 2022-04-26]
Designs/Designs/New cap Design/stl/1FingerPrint_part_CapDesign_Version2.STL
72.7 x 14.5 x 22.0
