Benedict-Bsl/SmartCap/Designs/Designs/New cap Design/UP_lock_CapDesign_Version2.SLDPRT

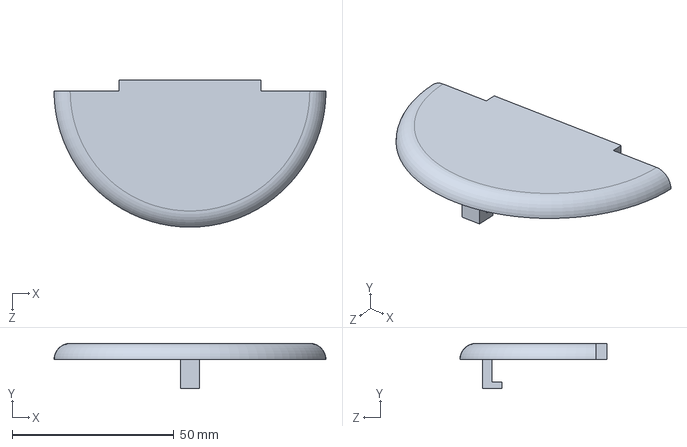
[picture p165: CAD file, 2022-04-26]
Designs/Designs/New cap Design/UP_lock_CapDesign_Version2.SLDPRT
84.0 x 14.0 x 45.5 mm
