Benedict-Bsl/SmartCap/Designs/Designs/Rotator_1.SLDPRT

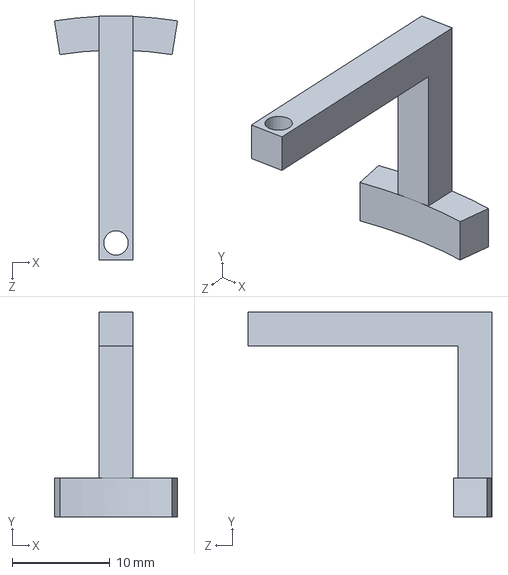
[picture p166: CAD file, 2022-04-26]
Designs/Designs/Rotator_1.SLDPRT
12.6 x 21.0 x 25.0 mm
