Benedict-Bsl/SmartCap/Designs/Designs/STL files/New/retractable2.SLDPRT

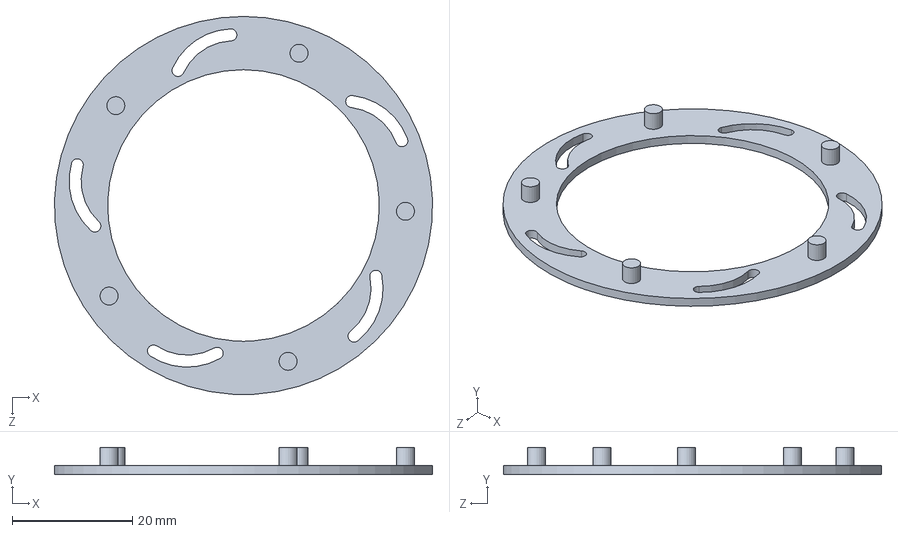
[picture p167: CAD file, 2022-04-26]
Designs/Designs/STL files/New/retractable2.SLDPRT
63.0 x 4.50 x 63.0 mm
