Benedict-Bsl/SmartCap/Designs/Designs/STL files/Rectrator_holder.STL

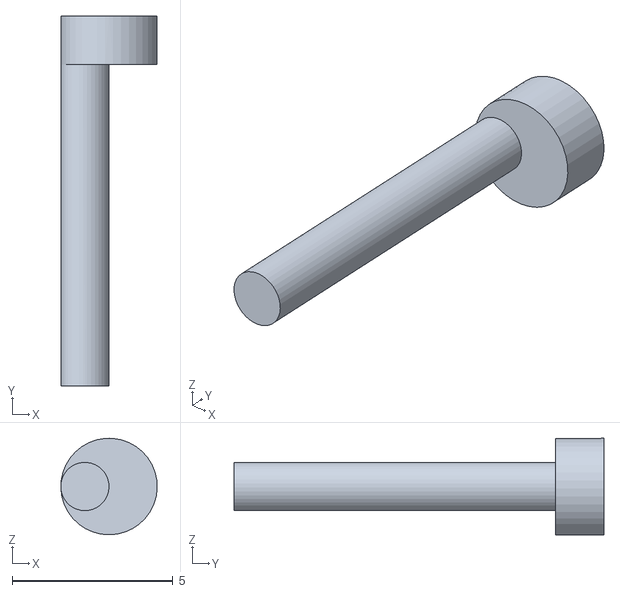
[picture p168: CAD file, 2022-04-26]
Designs/Designs/STL files/Rectrator_holder.STL
3.00 x 11.5 x 3.00
