Benedict-Bsl/SmartCap/Designs/Designs/Thursday 13 04 2022/CapDesign_Version6_WithoutTwoOpenSides.SLDPRT

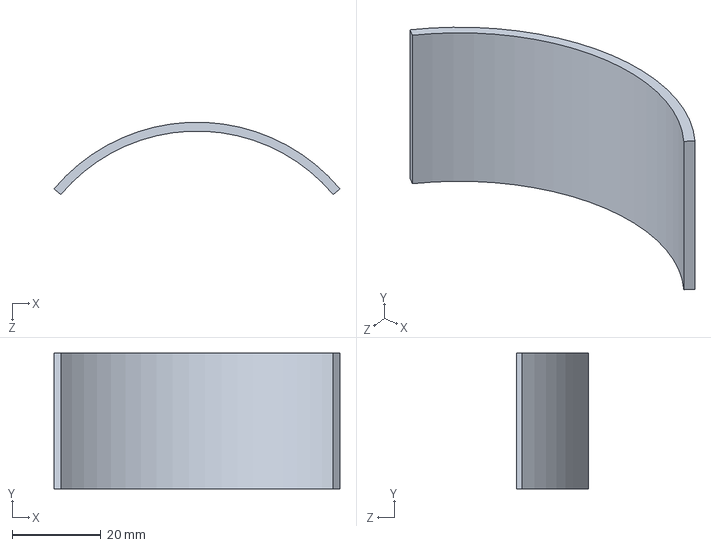
[picture p169: CAD file, 2022-04-26]
Designs/Designs/Thursday 13 04 2022/CapDesign_Version6_WithoutTwoOpenSides.SLDPRT
64.3 x 30.5 x 16.2 mm
