Benedict-Bsl/SmartCap/Designs/Designs/Thursday 13 04 2022/STL/Top_CapDesign_Version6.STL

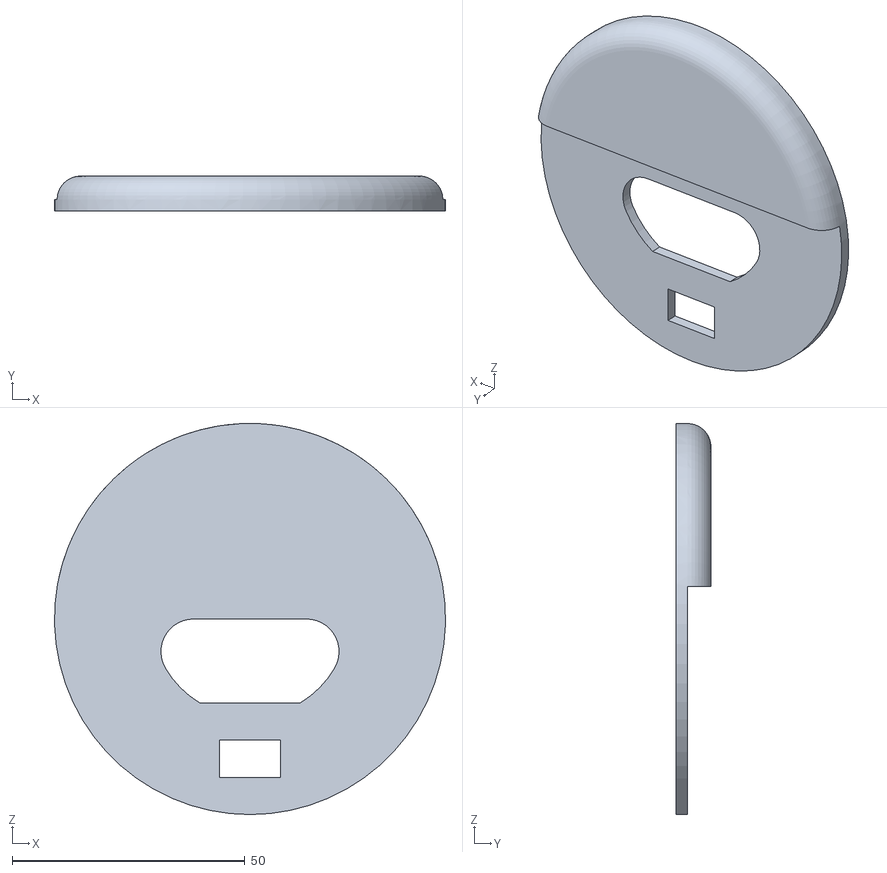
[picture p170: CAD file, 2022-04-26]
Designs/Designs/Thursday 13 04 2022/STL/Top_CapDesign_Version6.STL
84.0 x 7.50 x 84.0
