Benedict-Bsl/SmartCap/Designs/Designs/tuesda 04 05/PartSensorholder.STL

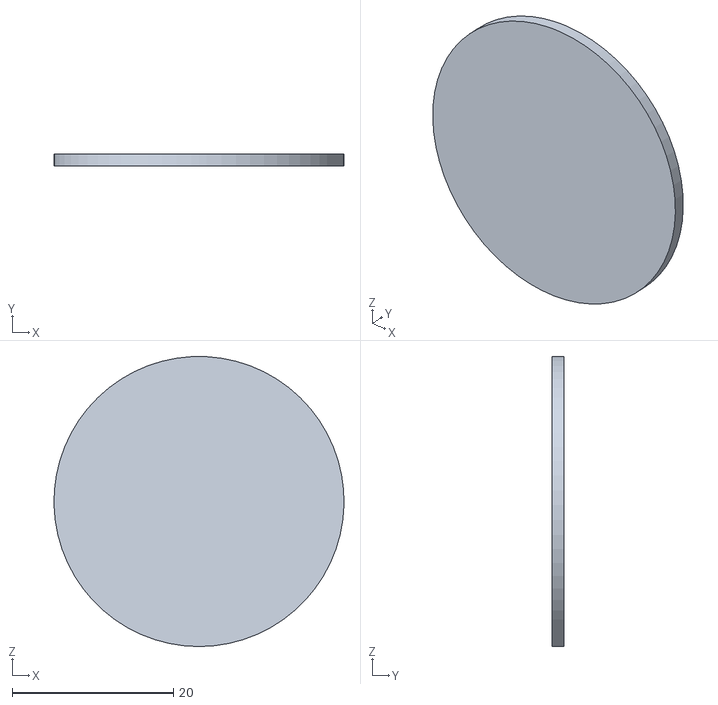
[picture p171: CAD file, 2022-04-26]
Designs/Designs/tuesda 04 05/PartSensorholder.STL
36.0 x 1.50 x 36.0
