Benedict-Bsl/SmartCap/Designs/Monday 25 04 2022/stkl/bigger_capBottom.STL

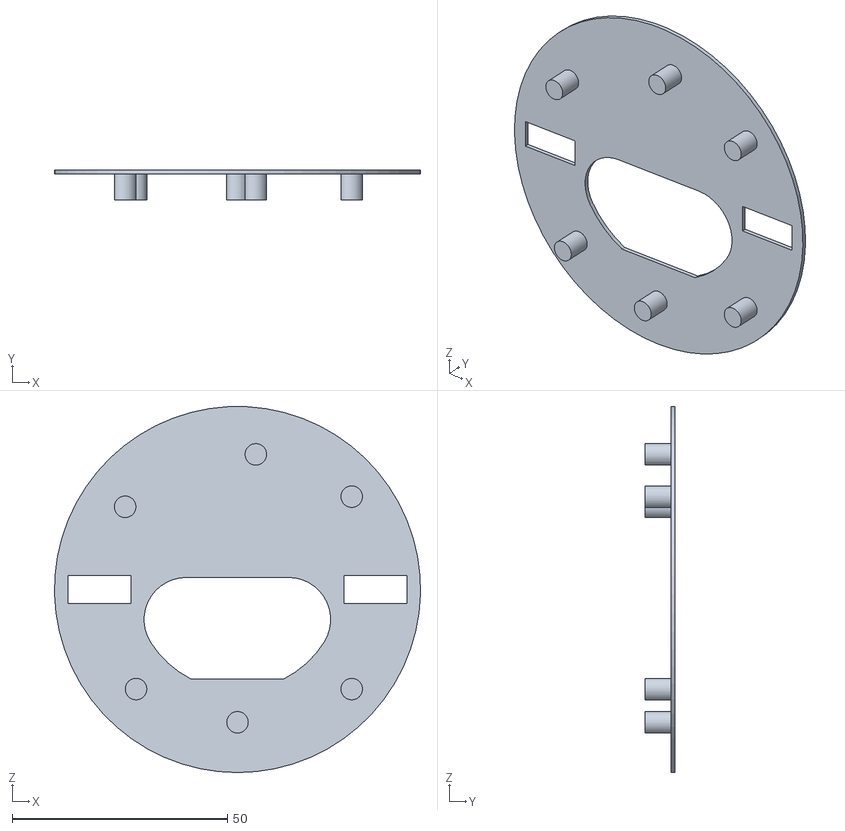
[picture p172: CAD file, 2022-05-06]
Designs/Monday 25 04 2022/stkl/bigger_capBottom.STL
85.0 x 7.00 x 85.0
