Benedict-Bsl/SmartCap/Designs/STL files/CupVersion4D6_withLocksMTop.STL

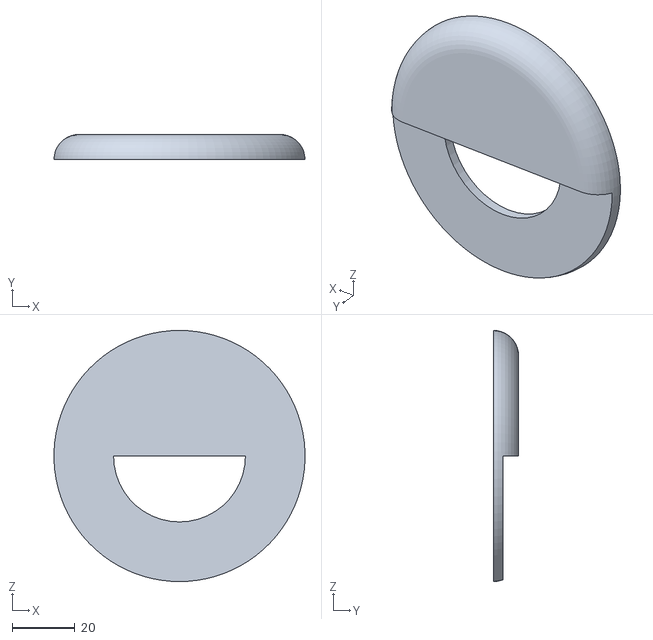
[picture p173: CAD file, 2022-03-20]
Designs/STL files/CupVersion4D6_withLocksMTop.STL
79.9 x 8.00 x 80.0
