Benedict-Bsl/SmartCap/Designs/STL files/Updated/Backup (8) of hinge2.SLDPRT

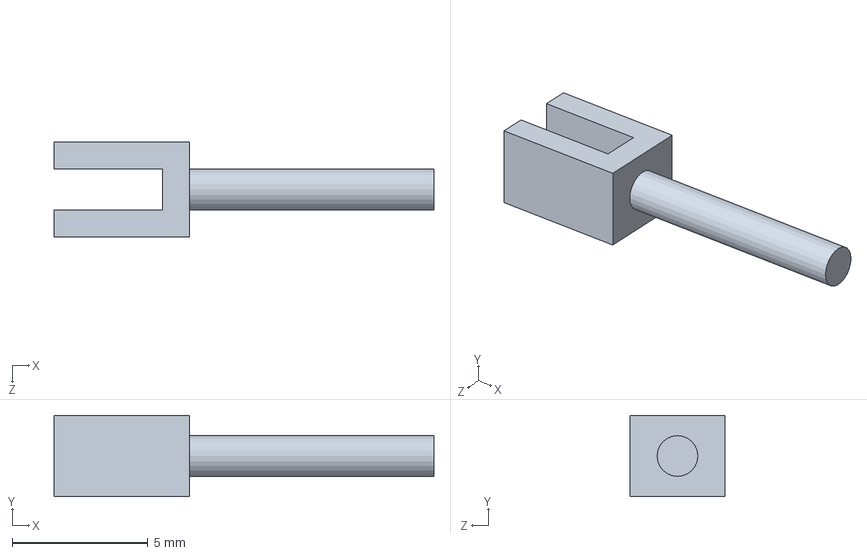
[picture p174: CAD file, 2022-04-26]
Designs/STL files/Updated/Backup (8) of hinge2.SLDPRT
14.0 x 3.00 x 3.50 mm
