Benedict-Bsl/SmartCap/Designs/STL files/Usable/CupVersion4C2_compartment.STL

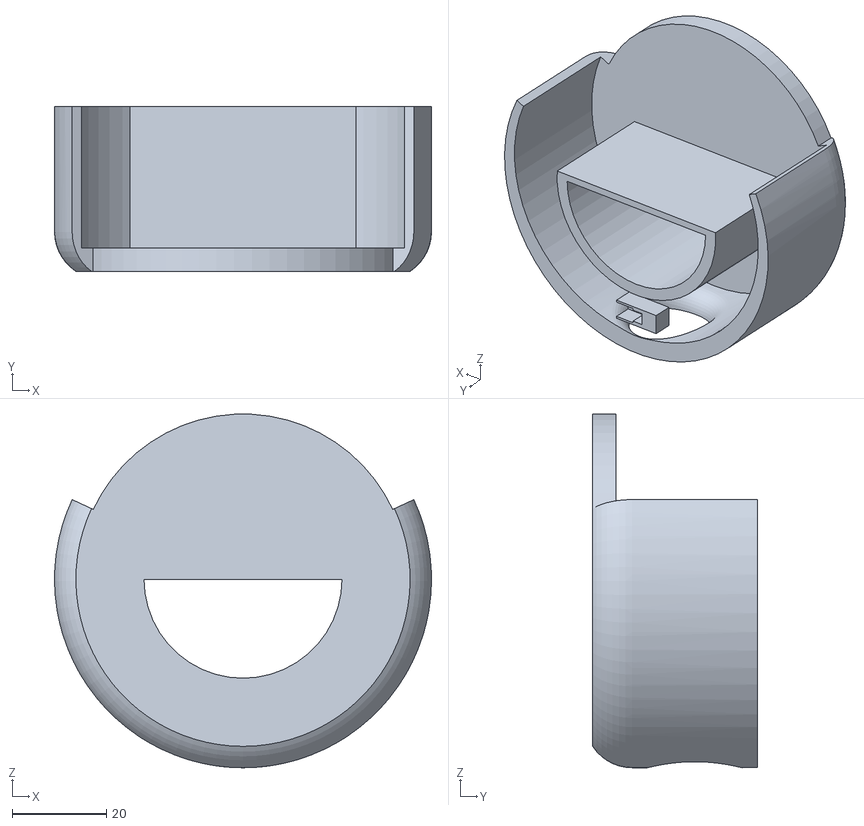
[picture p175: CAD file, 2022-03-20]
Designs/STL files/Usable/CupVersion4C2_compartment.STL
80.0 x 35.0 x 75.0
