Benedict-Bsl/SmartCap/Designs/Tuesday 15 06 2022/rotatingDisk2.SLDPRT

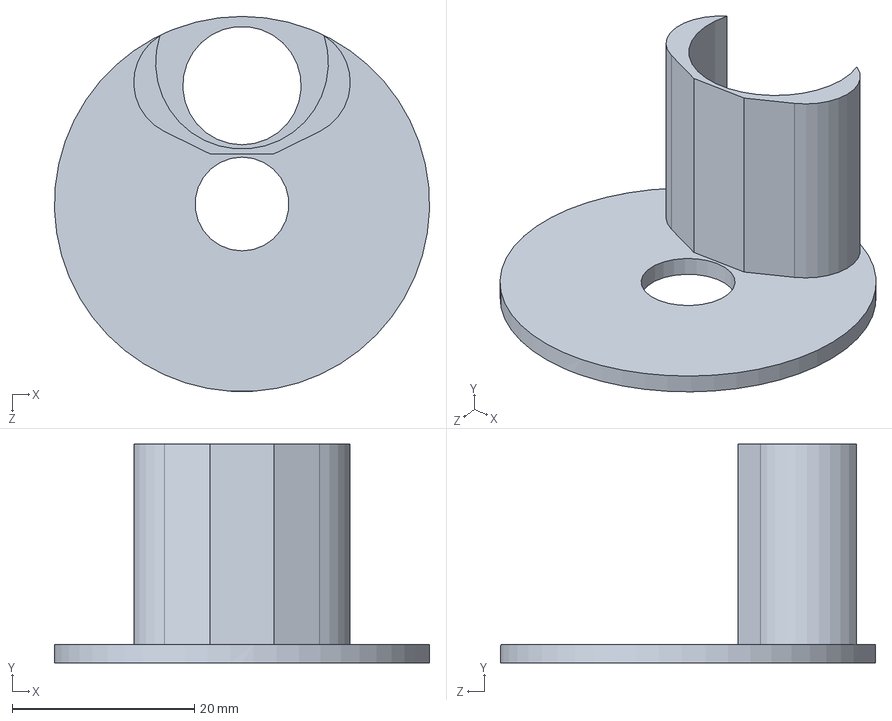
[picture p176: CAD file, 2022-06-18]
Designs/Tuesday 15 06 2022/rotatingDisk2.SLDPRT
41.2 x 24.0 x 41.2 mm
