Benedict-Bsl/SmartCap/Designs/Tuesday 15 06 2022/STL/pillSize5.STL

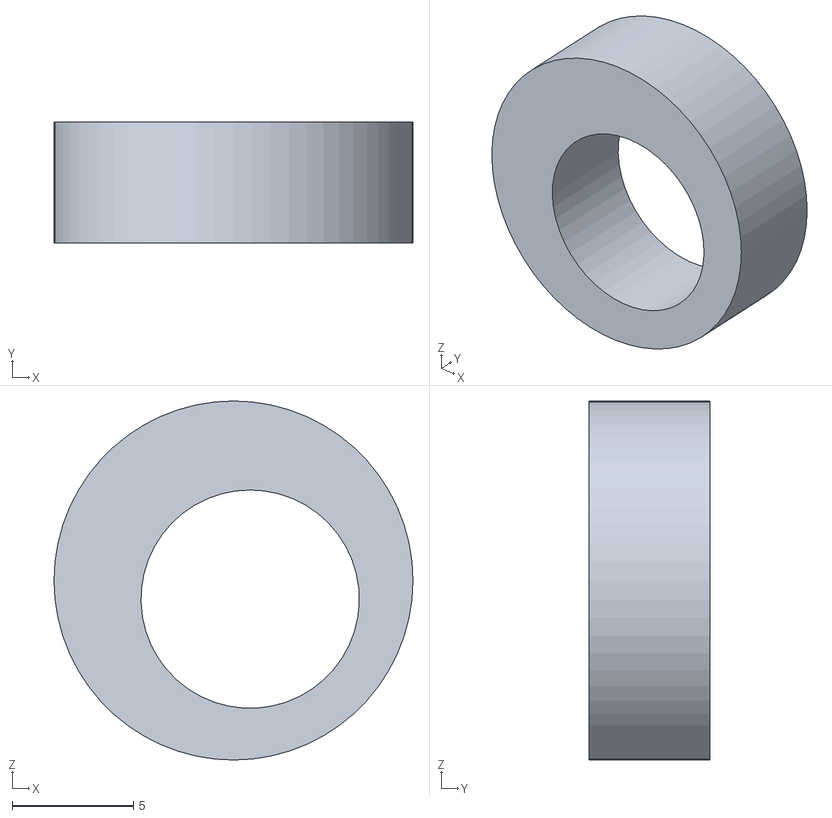
[picture p177: CAD file, 2022-06-18]
Designs/Tuesday 15 06 2022/STL/pillSize5.STL
14.8 x 5.00 x 14.8
