Benedict-Bsl/SmartCap/Designs/Tuesday10 05 2022/stl/B_locks_bottom.STL

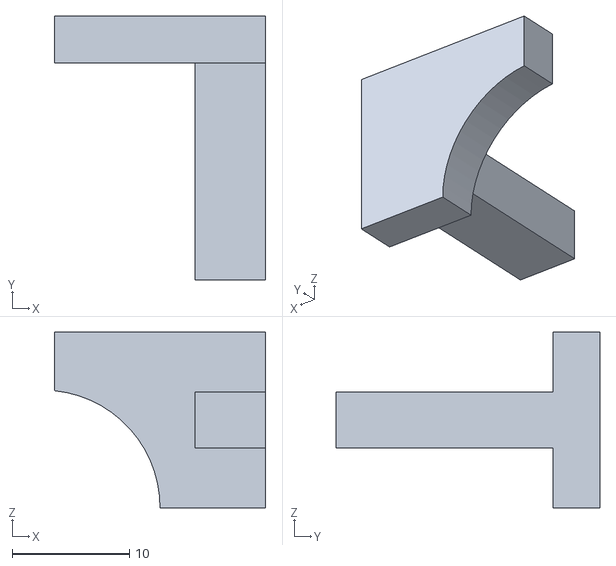
[picture p179: CAD file, 2022-05-22]
Designs/Tuesday10 05 2022/stl/B_locks_bottom.STL
18.0 x 22.5 x 15.0
