Benedict-Bsl/SmartCap/Misceleanous/cupModSlide.SLDPRT

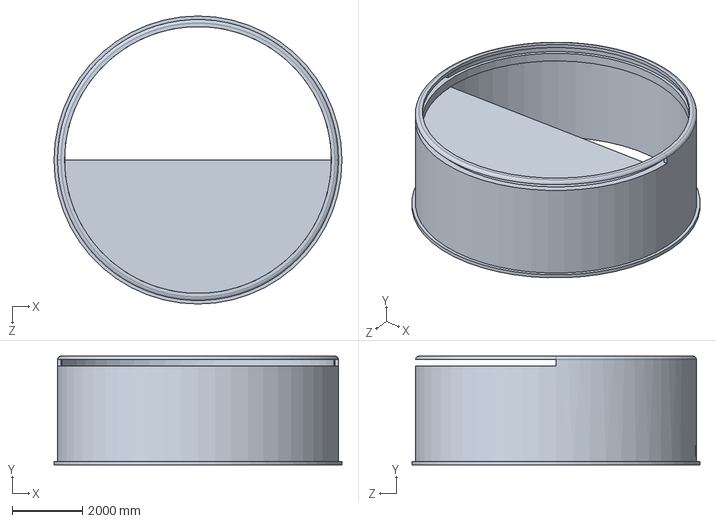
[picture p180: CAD file, 2022-03-13]
Misceleanous/cupModSlide.SLDPRT
8200.0 x 3100.0 x 8200.0 mm
