Benedict-Bsl/SmartCap/Designs/Designs/Locking/Bottom2ndPart_Lock_CupVersion4D6_withLocksM_2_fp&mt.SLDPRT

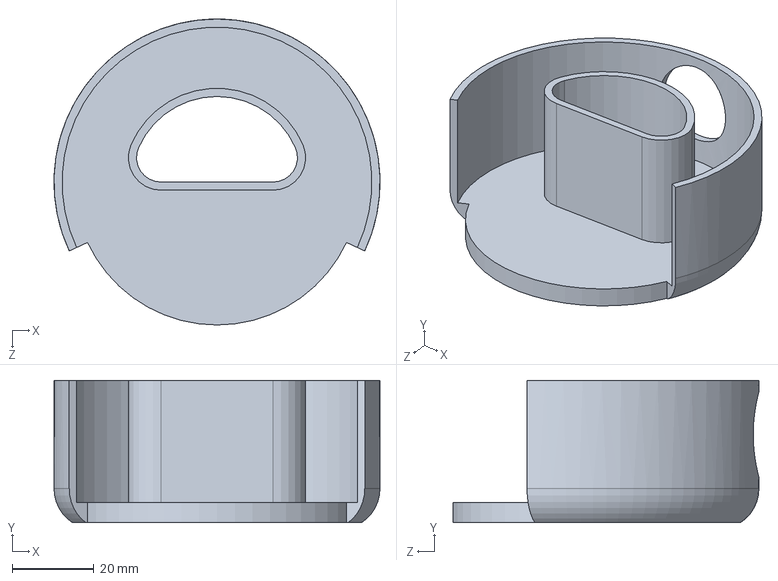
[picture p181: CAD file, 2022-04-26]
Designs/Designs/Locking/Bottom2ndPart_Lock_CupVersion4D6_withLocksM_2_fp&mt.SLDPRT
80.0 x 35.0 x 75.1 mm
