Benedict-Bsl/SmartCap/Designs/Designs/Monday 04 04 2022/LockInside.SLDPRT

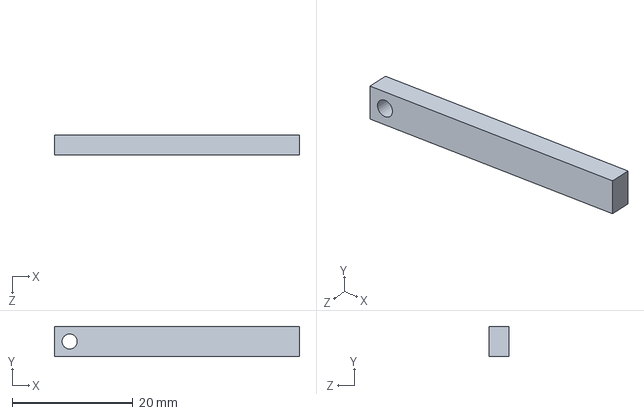
[picture p182: CAD file, 2022-04-26]
Designs/Designs/Monday 04 04 2022/LockInside.SLDPRT
40.5 x 5.00 x 3.30 mm
