Benedict-Bsl/SmartCap/Designs/Designs/Monday 25 04 2022/bigger_cap.SLDPRT

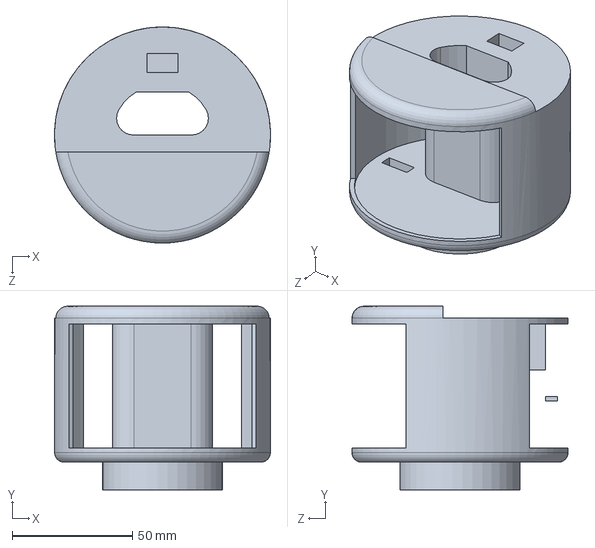
[picture p183: CAD file, 2022-05-06]
Designs/Designs/Monday 25 04 2022/bigger_cap.SLDPRT
90.0 x 76.5 x 90.0 mm
