Benedict-Bsl/SmartCap/Designs/Designs/New cap Design/stl/3 CapDesign_Version2.STL

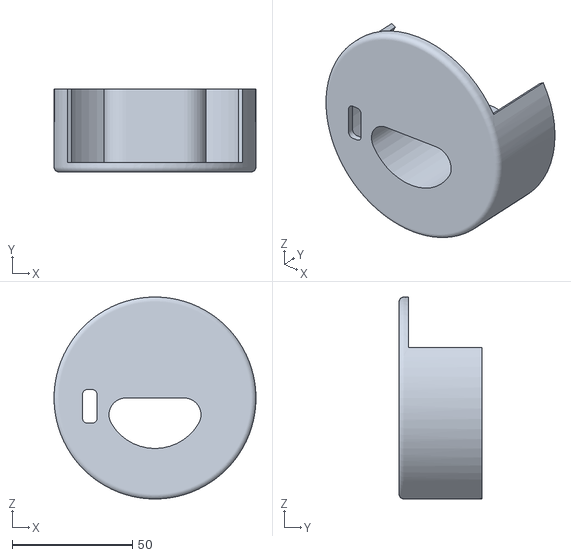
[picture p184: CAD file, 2022-04-26]
Designs/Designs/New cap Design/stl/3 CapDesign_Version2.STL
84.0 x 34.5 x 84.0
