Benedict-Bsl/SmartCap/Designs/Designs/Rotorara.SLDPRT

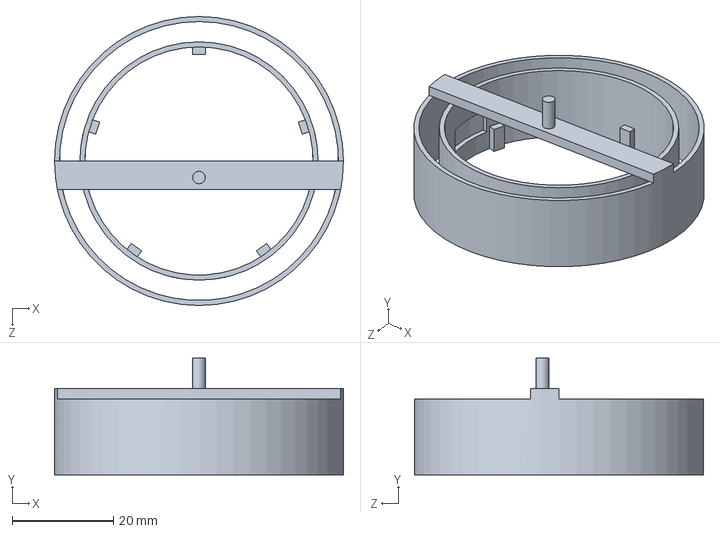
[picture p185: CAD file, 2022-04-26]
Designs/Designs/Rotorara.SLDPRT
57.0 x 23.0 x 57.0 mm
