Benedict-Bsl/SmartCap/Designs/Designs/STL files/New/Rectrator_holder.SLDPRT

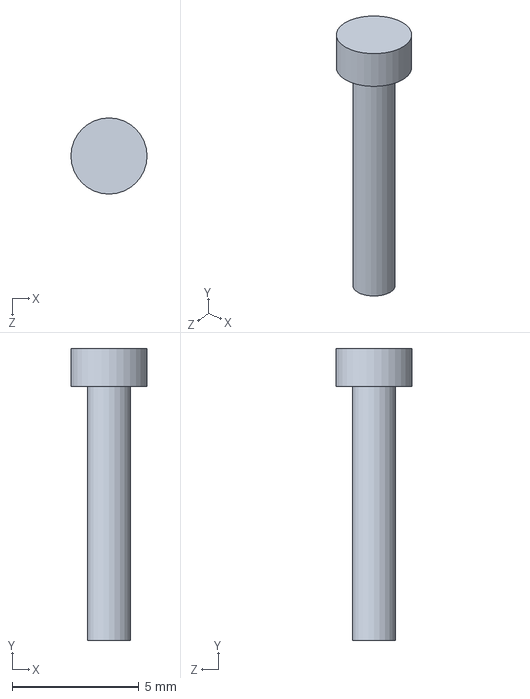
[picture p186: CAD file, 2022-04-26]
Designs/Designs/STL files/New/Rectrator_holder.SLDPRT
3.00 x 11.5 x 3.00 mm
