Benedict-Bsl/SmartCap/Designs/Designs/STL files/Retractee_kvo.STL

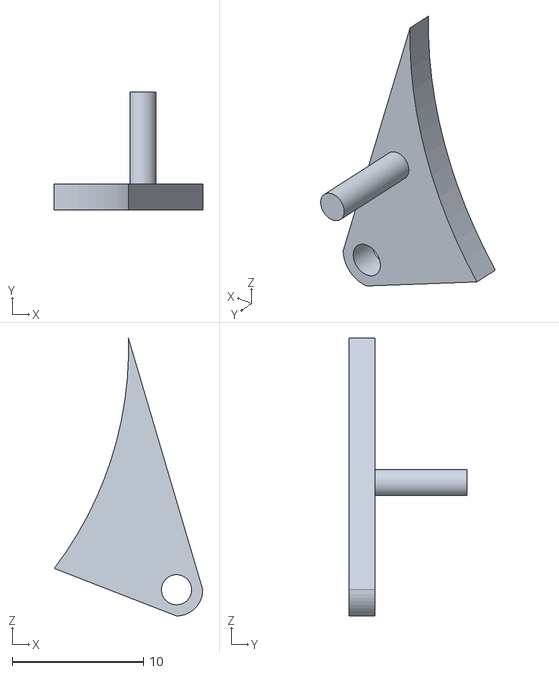
[picture p187: CAD file, 2022-04-26]
Designs/Designs/STL files/Retractee_kvo.STL
11.3 x 9.00 x 21.2
