Benedict-Bsl/SmartCap/Designs/Designs/Thursday 13 04 2022/STL/1-loCK_A_WithThin_CapDesign_Version6.STL

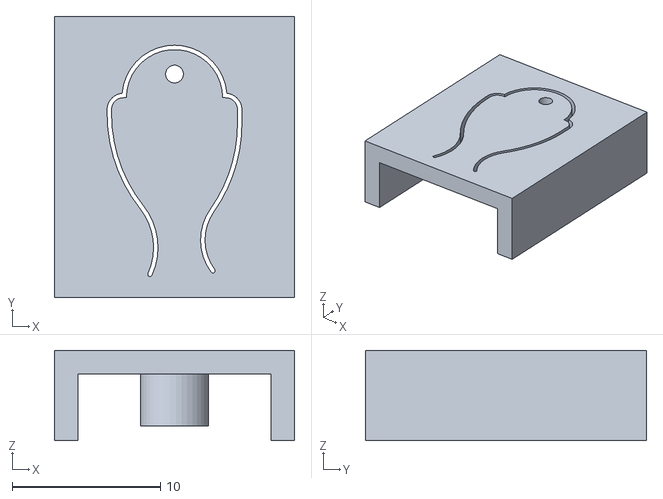
[picture p188: CAD file, 2022-04-26]
Designs/Designs/Thursday 13 04 2022/STL/1-loCK_A_WithThin_CapDesign_Version6.STL
16.2 x 19.0 x 6.10
