Benedict-Bsl/SmartCap/Designs/Designs/tuesda 04 05/Middle_CapDesign_Version5.STL

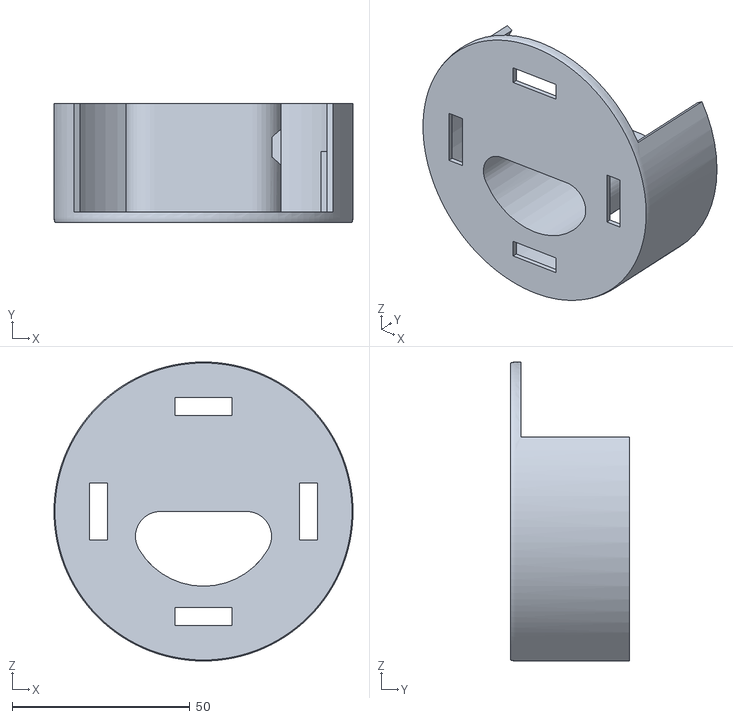
[picture p189: CAD file, 2022-04-26]
Designs/Designs/tuesda 04 05/Middle_CapDesign_Version5.STL
84.0 x 33.5 x 84.0
