Benedict-Bsl/SmartCap/Designs/Monday 25 04 2022/stkl/bottom_bigger_cap.STL

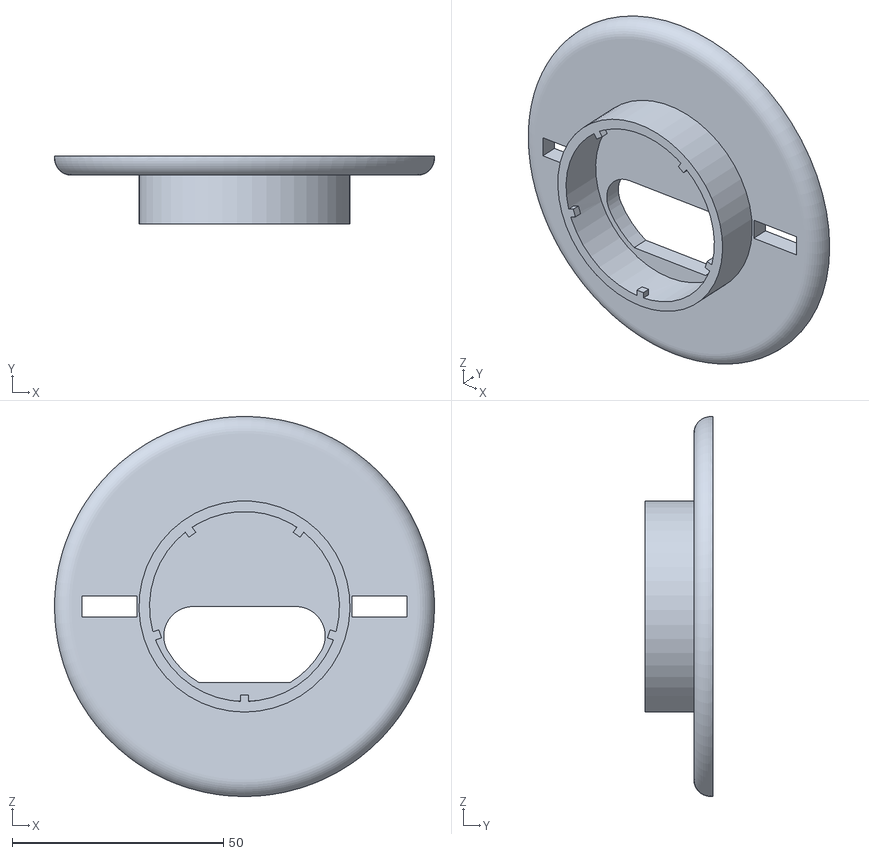
[picture p190: CAD file, 2022-05-06]
Designs/Monday 25 04 2022/stkl/bottom_bigger_cap.STL
90.0 x 16.0 x 90.0
