Benedict-Bsl/SmartCap/Designs/STL files/CupVersion4D5.STL

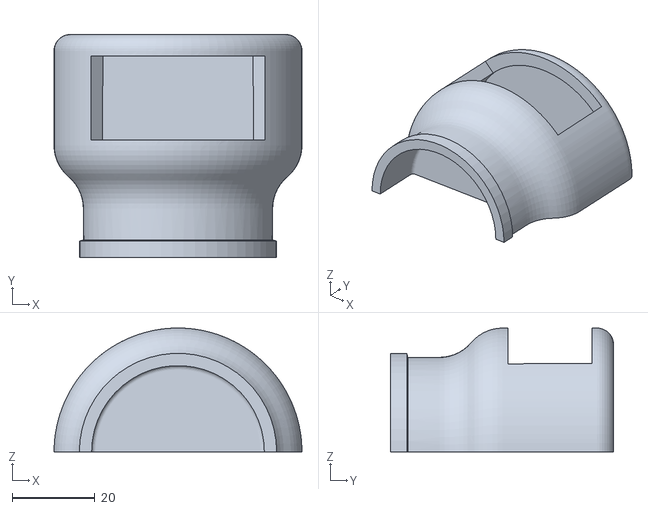
[picture p191: CAD file, 2022-03-20]
Designs/STL files/CupVersion4D5.STL
60.0 x 54.0 x 30.0
