Benedict-Bsl/SmartCap/Designs/STL files/Updated/Backup (1) of hinge1.SLDPRT

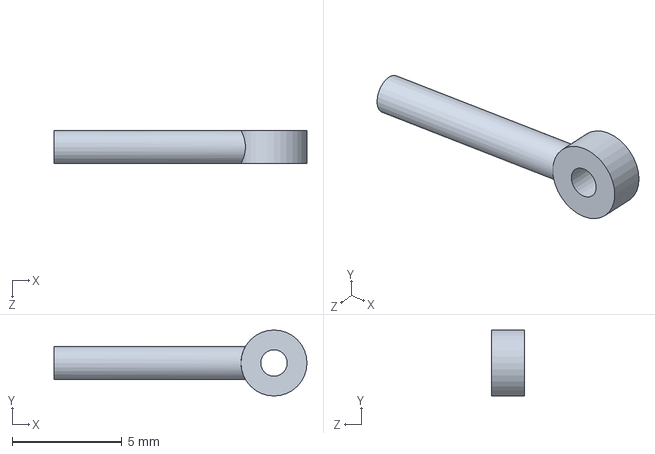
[picture p192: CAD file, 2022-04-26]
Designs/STL files/Updated/Backup (1) of hinge1.SLDPRT
11.5 x 3.00 x 1.50 mm
