Benedict-Bsl/SmartCap/Designs/STL files/Usable/Backup (1) of TopFor_VErsion4D_fp&mt.SLDPRT

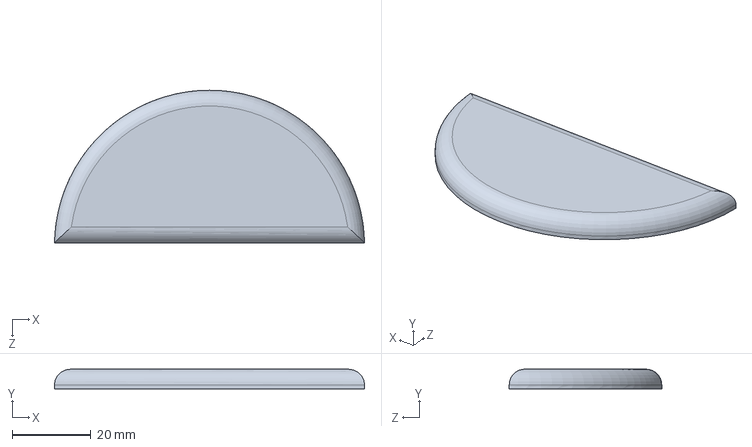
[picture p193: CAD file, 2022-03-20]
Designs/STL files/Usable/Backup (1) of TopFor_VErsion4D_fp&mt.SLDPRT
78.8 x 5.00 x 38.8 mm
