Benedict-Bsl/SmartCap/Designs/Tuesday 15 06 2022/esp32Cam.SLDPRT

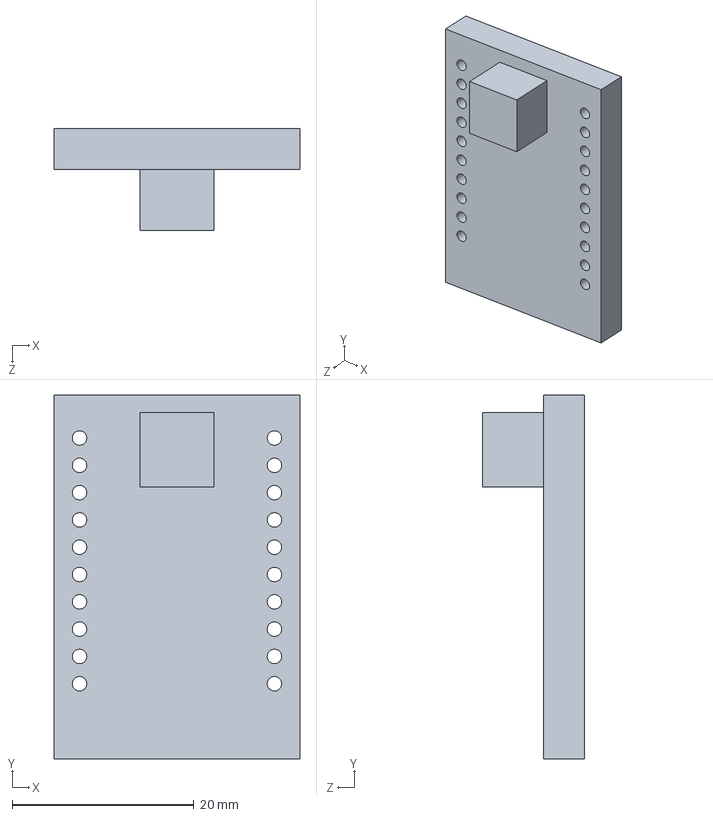
[picture p194: CAD file, 2022-06-18]
Designs/Tuesday 15 06 2022/esp32Cam.SLDPRT
27.0 x 40.0 x 11.2 mm
