Benedict-Bsl/SmartCap/Designs/Tuesday 15 06 2022/STL/pillSize3.SLDPRT

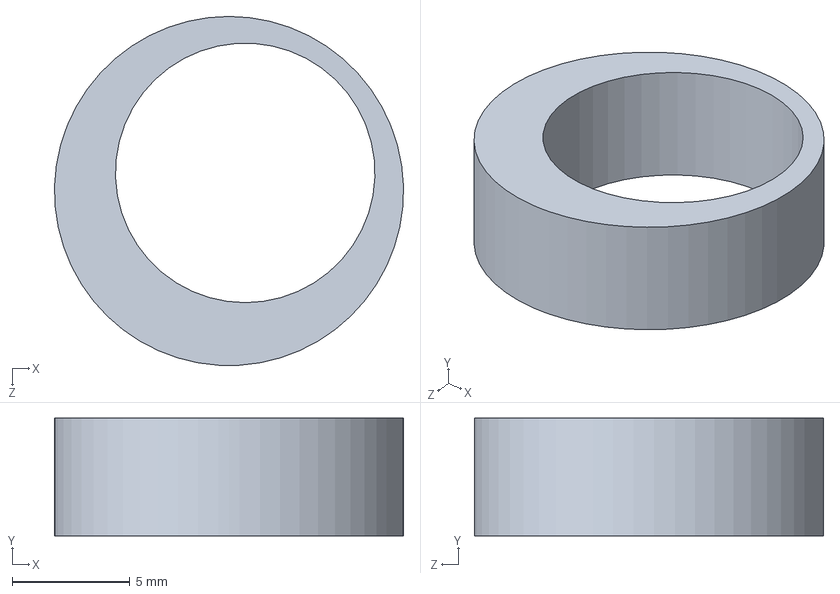
[picture p195: CAD file, 2022-06-18]
Designs/Tuesday 15 06 2022/STL/pillSize3.SLDPRT
14.8 x 5.00 x 14.8 mm
