Benedict-Bsl/SmartCap/Designs/Tuesday10 05 2022/Backup of couloir.SLDPRT

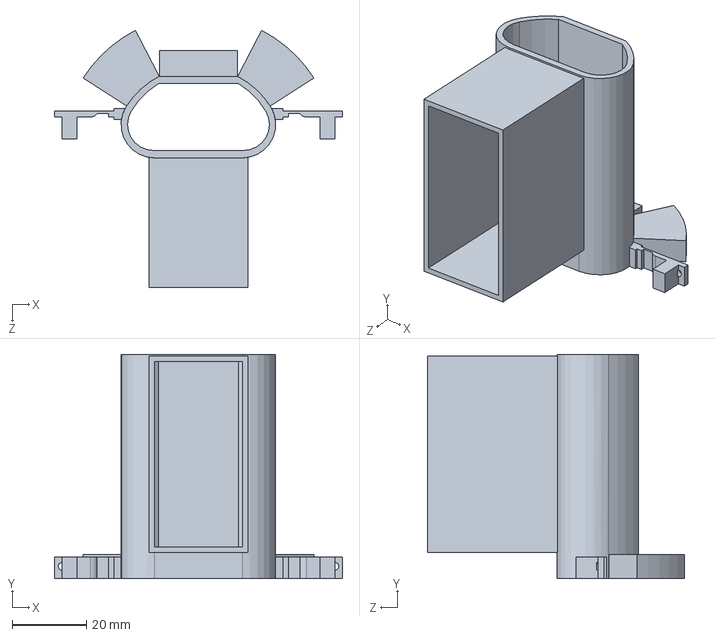
[picture p196: CAD file, 2022-06-18]
Designs/Tuesday10 05 2022/Backup of couloir.SLDPRT
77.6 x 60.5 x 69.4 mm
