Benedict-Bsl/SmartCap/Designs/Tuesday10 05 2022/stl/Abigger_cap3_FingerPrintPart.STL

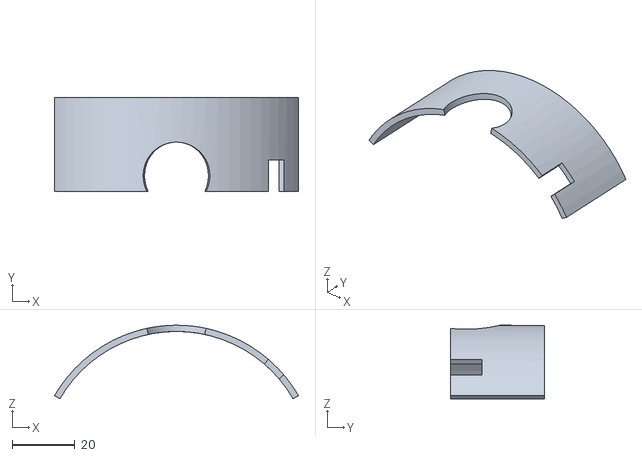
[picture p197: CAD file, 2022-05-22]
Designs/Tuesday10 05 2022/stl/Abigger_cap3_FingerPrintPart.STL
77.9 x 30.0 x 23.5
