Benedict-Bsl/SmartCap/Misceleanous/Backup (1) of sliddingSection.SLDPRT

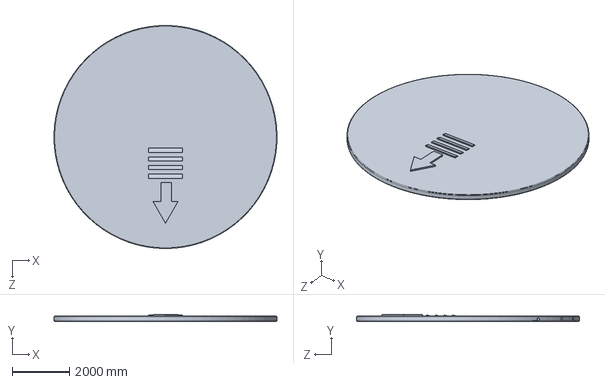
[picture p198: CAD file, 2022-03-13]
Misceleanous/Backup (1) of sliddingSection.SLDPRT
7758.3 x 230.0 x 7760.0 mm
