Benedict-Bsl/SmartCap/Designs/Designs/Bottle)design.SLDPRT

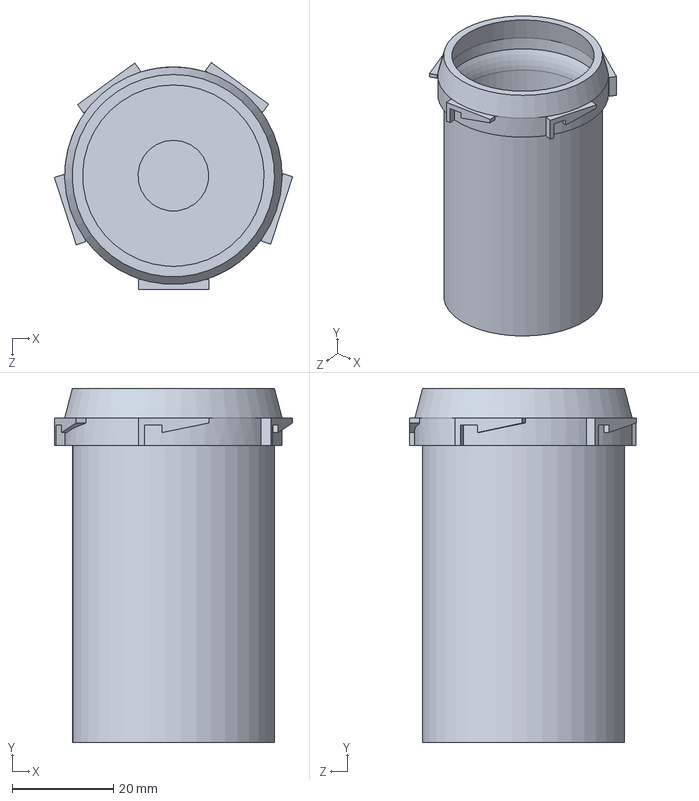
[picture p199: CAD file, 2022-04-26]
Designs/Designs/Bottle)design.SLDPRT
47.1 x 70.0 x 44.9 mm
