Benedict-Bsl/SmartCap/Designs/Designs/Locking/Bottom1_Lock_CupVersion4D6_withLocksM_2_fp&mt.SLDPRT

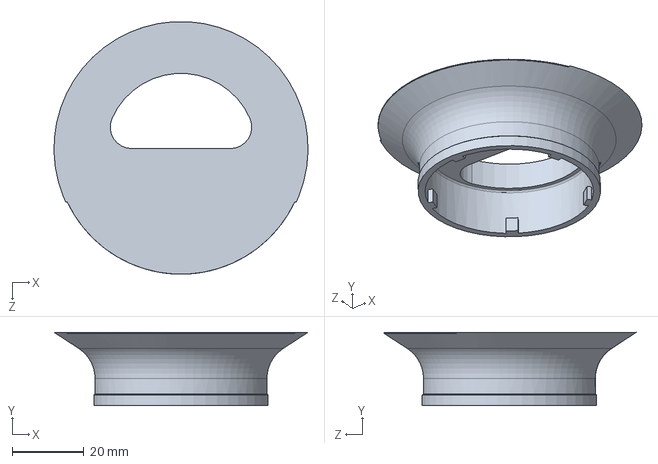
[picture p200: CAD file, 2022-04-26]
Designs/Designs/Locking/Bottom1_Lock_CupVersion4D6_withLocksM_2_fp&mt.SLDPRT
70.9 x 20.5 x 70.5 mm
