Benedict-Bsl/SmartCap/Designs/Designs/Locking/New/rotation axis gear.SLDPRT

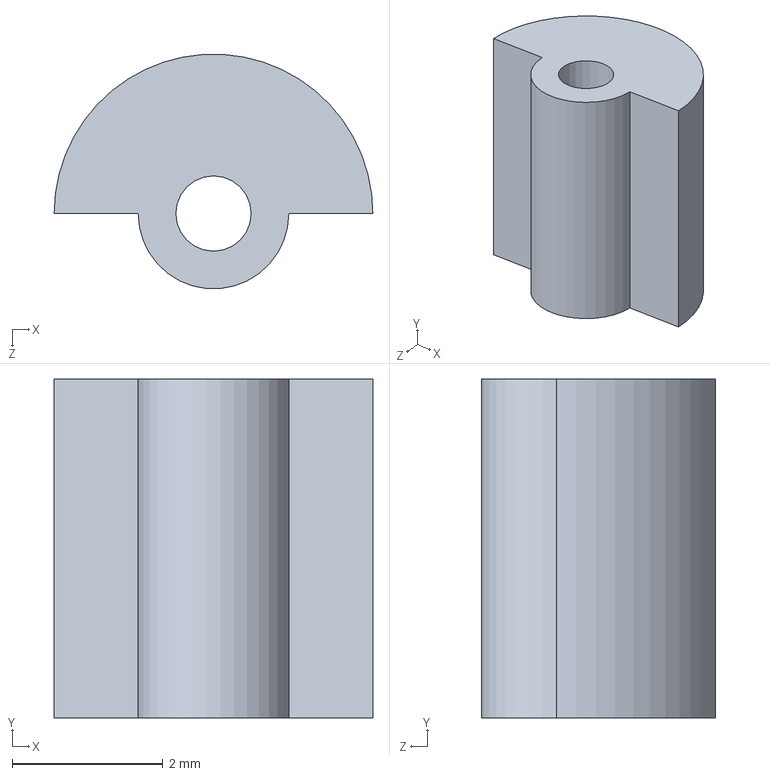
[picture p201: CAD file, 2022-04-26]
Designs/Designs/Locking/New/rotation axis gear.SLDPRT
4.23 x 4.50 x 3.11 mm
