Benedict-Bsl/SmartCap/Designs/Designs/Monday 04 04 2022/Backup (2) of CapDesign_Version5.SLDPRT

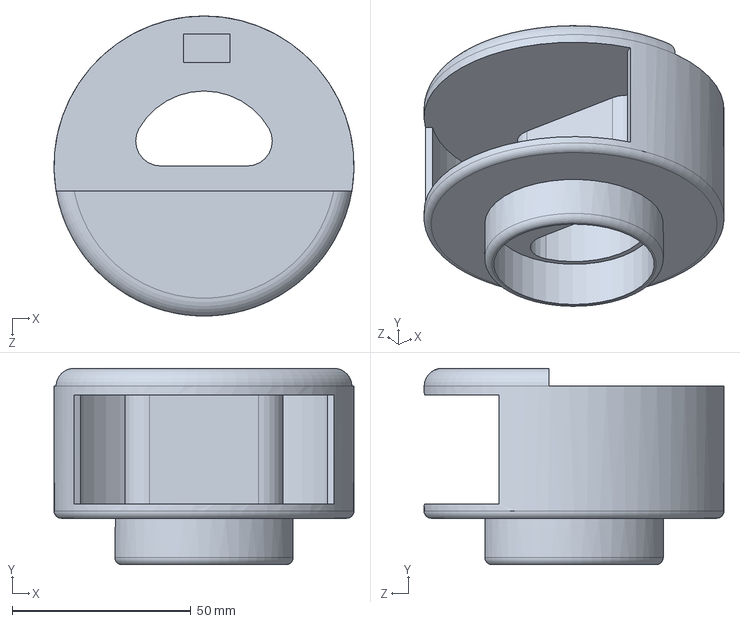
[picture p202: CAD file, 2022-04-26]
Designs/Designs/Monday 04 04 2022/Backup (2) of CapDesign_Version5.SLDPRT
84.0 x 55.0 x 84.0 mm
