Benedict-Bsl/SmartCap/Designs/Designs/New cap Design/motorHolder.SLDPRT

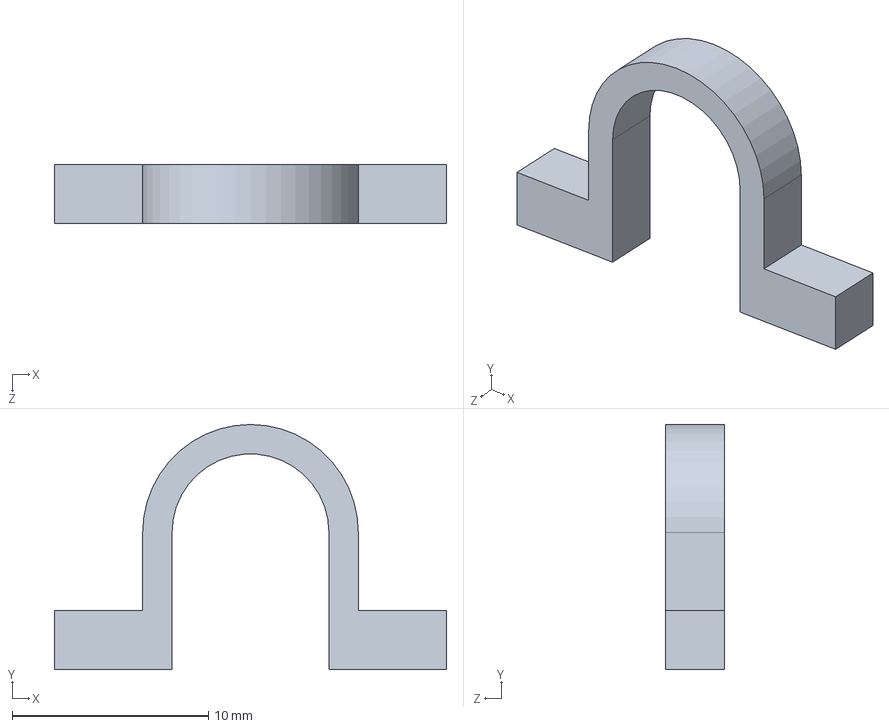
[picture p203: CAD file, 2022-04-26]
Designs/Designs/New cap Design/motorHolder.SLDPRT
20.0 x 12.5 x 3.00 mm
