Benedict-Bsl/SmartCap/Designs/Designs/New cap Design/stl/5 UP_lock_CapDesign_Version2.STL

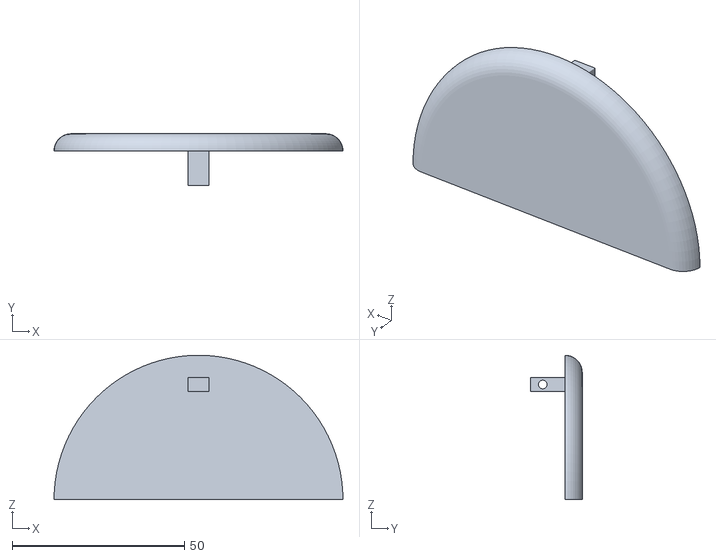
[picture p204: CAD file, 2022-04-26]
Designs/Designs/New cap Design/stl/5 UP_lock_CapDesign_Version2.STL
84.0 x 15.0 x 42.0
