Benedict-Bsl/SmartCap/Designs/Designs/STL files/New/retractable_rotator.SLDPRT

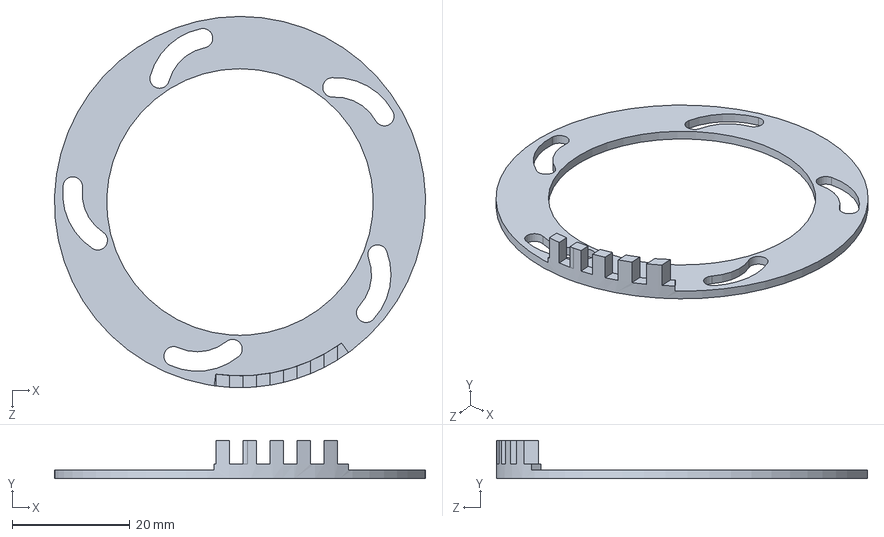
[picture p205: CAD file, 2022-04-26]
Designs/Designs/STL files/New/retractable_rotator.SLDPRT
63.0 x 6.50 x 63.0 mm
