Benedict-Bsl/SmartCap/Designs/Designs/STL files/Retractee.STL

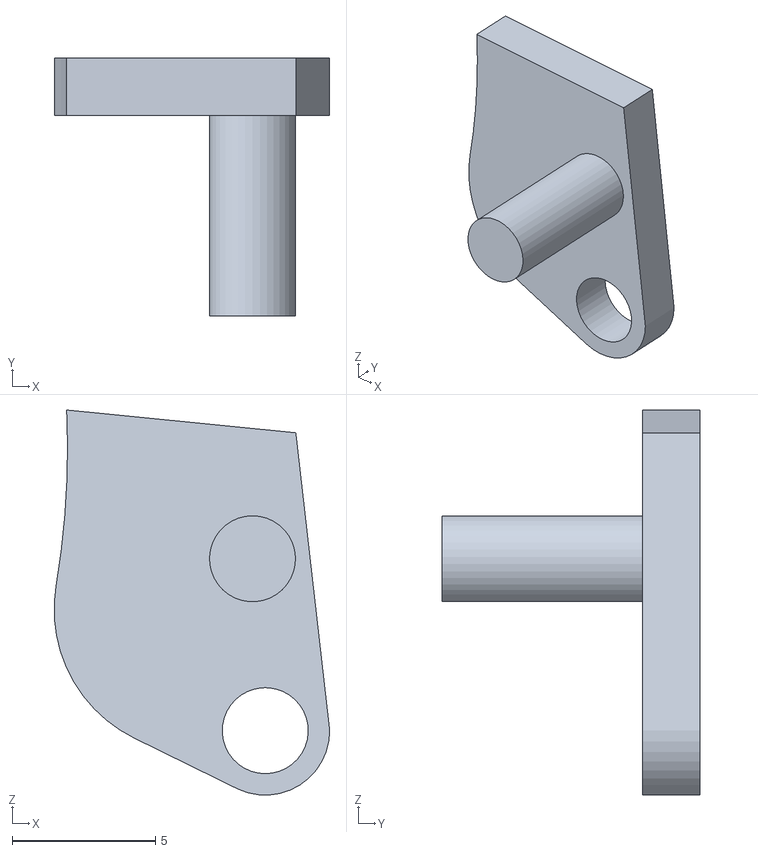
[picture p206: CAD file, 2022-04-26]
Designs/Designs/STL files/Retractee.STL
9.61 x 9.00 x 13.4
