Benedict-Bsl/SmartCap/Designs/Designs/Thursday 13 04 2022/STL/lock side cover.STL

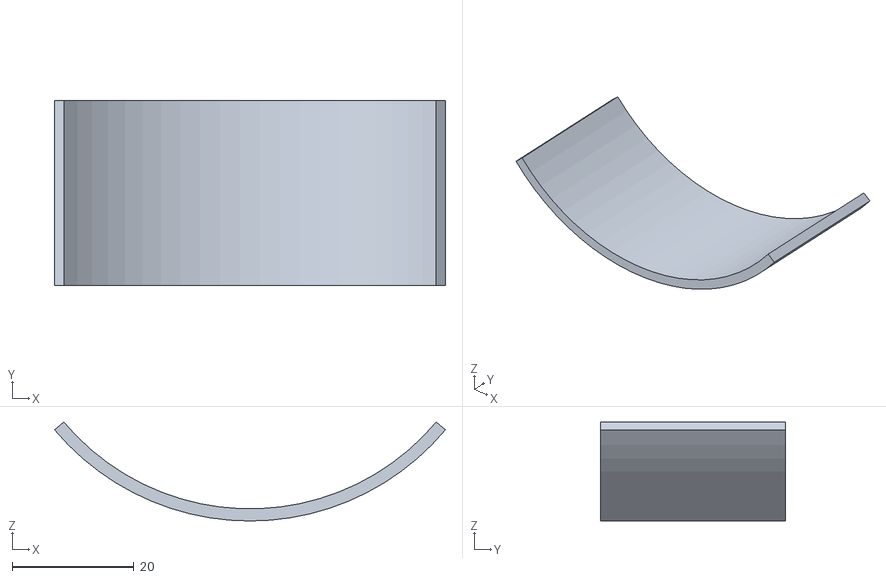
[picture p207: CAD file, 2022-04-26]
Designs/Designs/Thursday 13 04 2022/STL/lock side cover.STL
64.3 x 30.5 x 16.3
