Benedict-Bsl/SmartCap/Designs/Designs/tuesda 04 05/Part1.SLDPRT

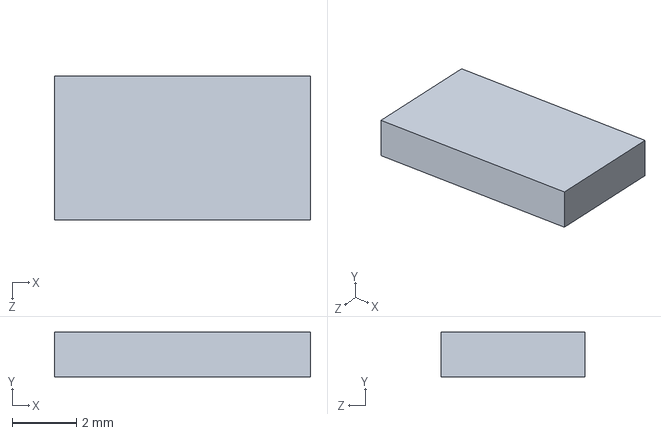
[picture p208: CAD file, 2022-04-26]
Designs/Designs/tuesda 04 05/Part1.SLDPRT
8.00 x 1.40 x 4.50 mm
