Benedict-Bsl/SmartCap/Designs/Monday 25 04 2022/stkl/locks_bottom_2B.STL

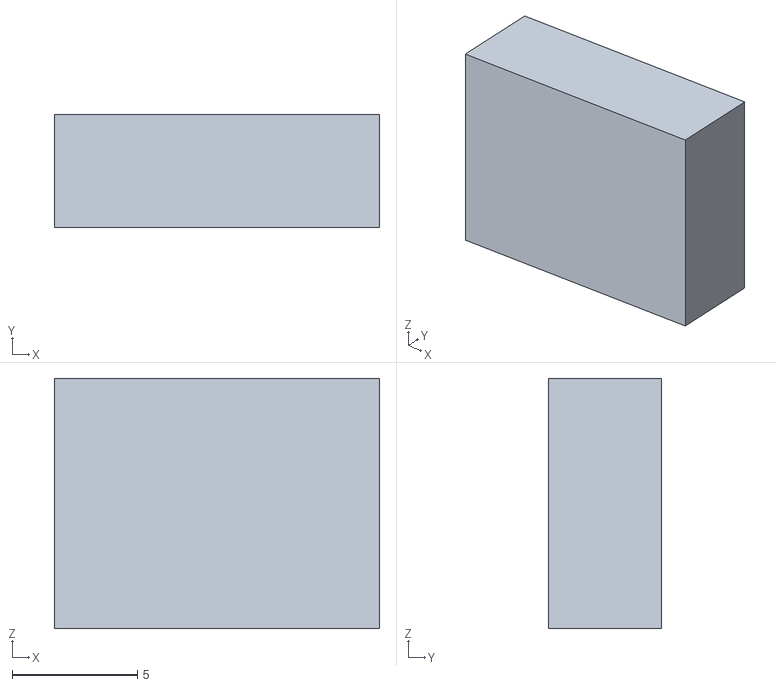
[picture p209: CAD file, 2022-05-06]
Designs/Monday 25 04 2022/stkl/locks_bottom_2B.STL
13.0 x 4.50 x 10.0
