Benedict-Bsl/SmartCap/Designs/Monday 25 04 2022/UP_lock_CapDesign_Version6_L.SLDPRT

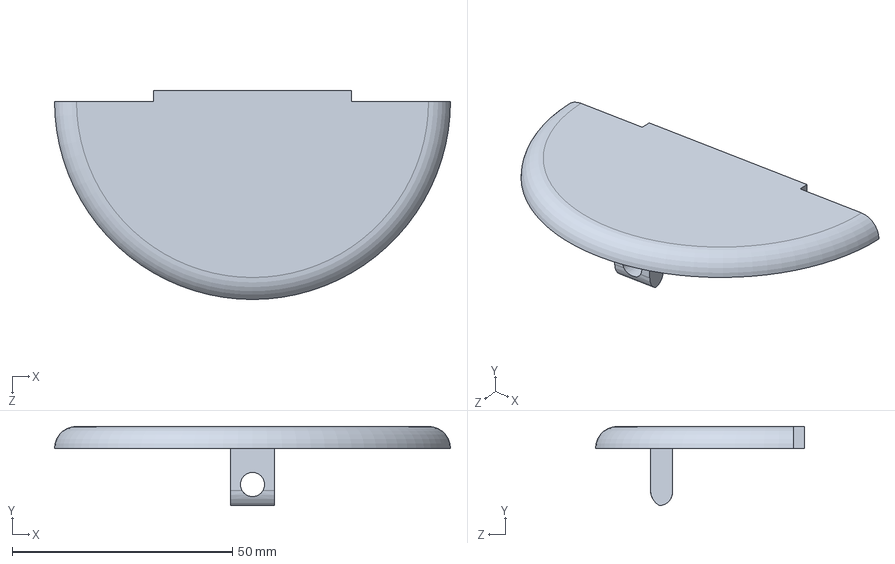
[picture p210: CAD file, 2022-05-06]
Designs/Monday 25 04 2022/UP_lock_CapDesign_Version6_L.SLDPRT
90.0 x 18.0 x 47.5 mm
