Benedict-Bsl/SmartCap/Designs/STL files/SideCoverFor_CupVersion4D6.STL

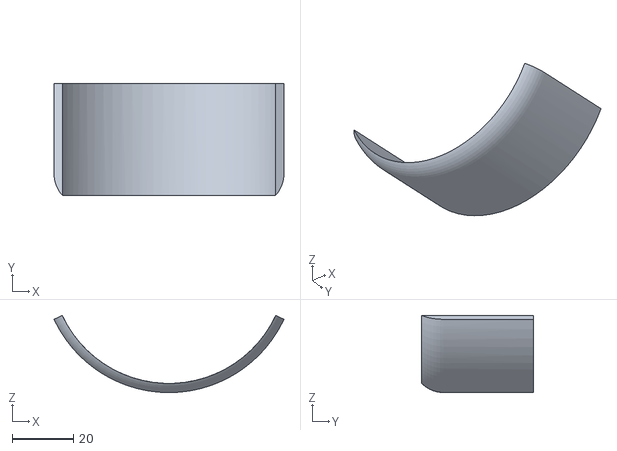
[picture p211: CAD file, 2022-03-20]
Designs/STL files/SideCoverFor_CupVersion4D6.STL
75.2 x 36.5 x 25.2
