Benedict-Bsl/SmartCap/Designs/STL files/Updated/Motor_compartment_CupVersion4D6_withLocksM_2_fp&mt.SLDPRT

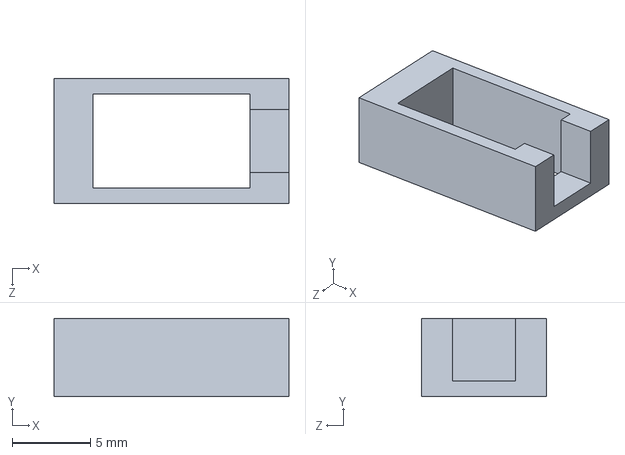
[picture p212: CAD file, 2022-04-26]
Designs/STL files/Updated/Motor_compartment_CupVersion4D6_withLocksM_2_fp&mt.SLDPRT
15.0 x 5.00 x 8.00 mm
