Benedict-Bsl/SmartCap/Designs/STL files/Usable/Up2.STL

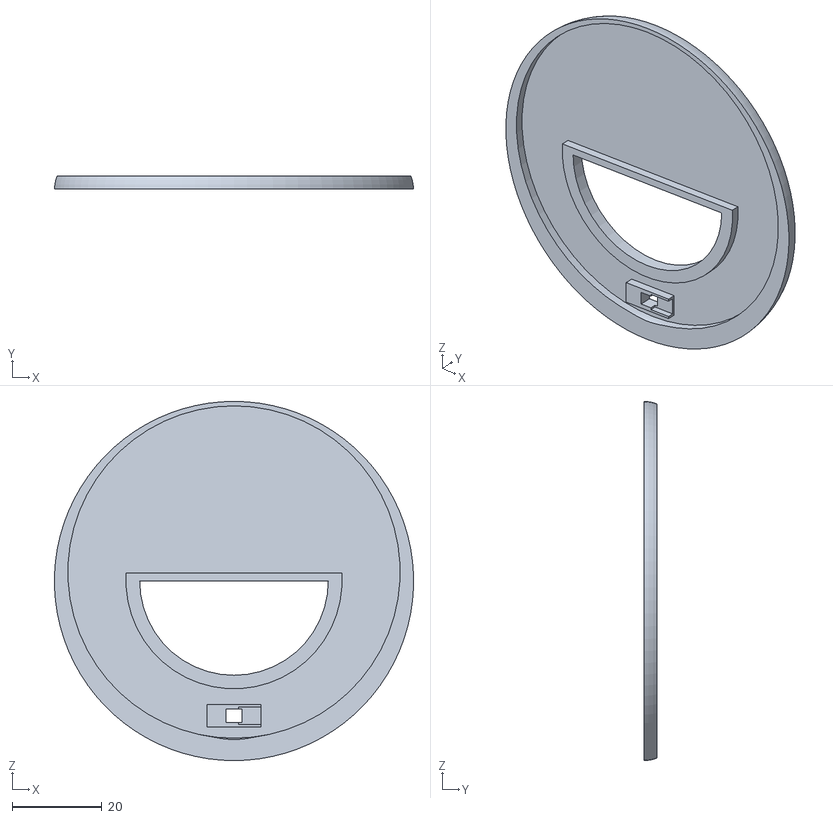
[picture p213: CAD file, 2022-03-20]
Designs/STL files/Usable/Up2.STL
79.9 x 3.00 x 80.0
