Benedict-Bsl/SmartCap/Designs/Tuesday 15 06 2022/STL/Rotate_pillSizeVar7.STL

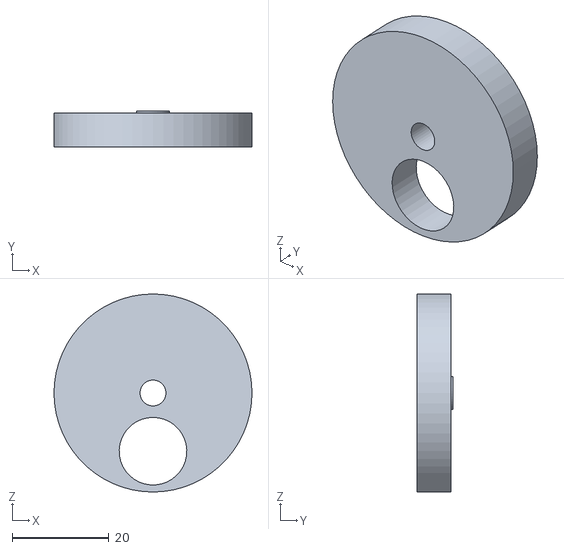
[picture p214: CAD file, 2022-06-18]
Designs/Tuesday 15 06 2022/STL/Rotate_pillSizeVar7.STL
41.0 x 7.40 x 41.0
