Benedict-Bsl/SmartCap/Designs/Tuesday10 05 2022/Backup of bigger_cap3.SLDPRT

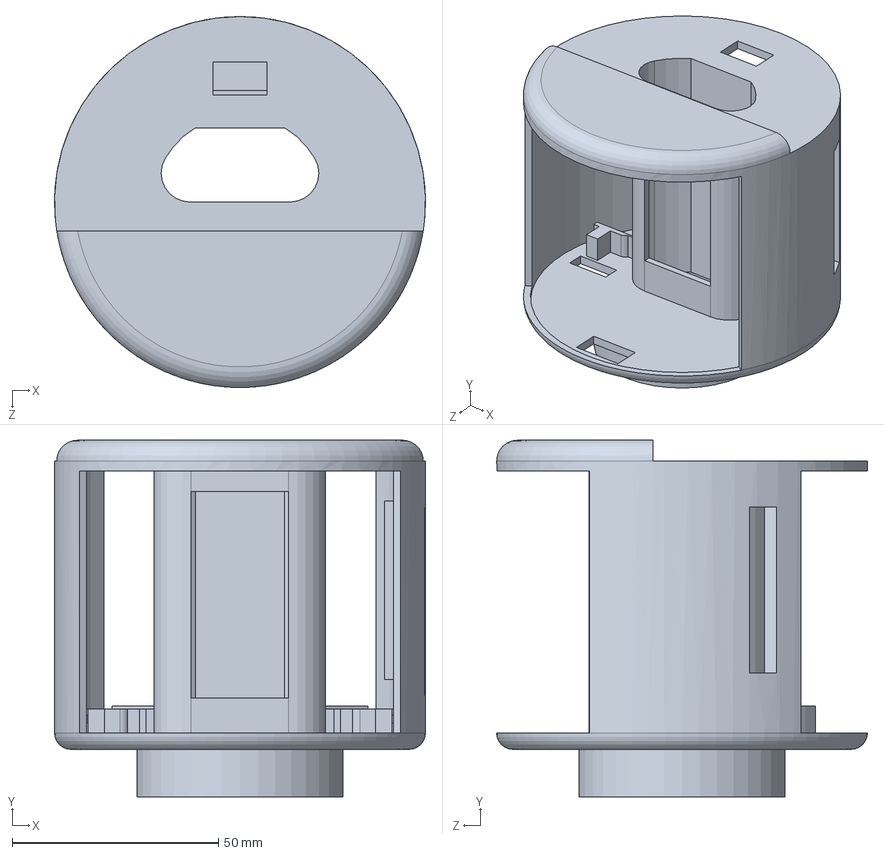
[picture p215: CAD file, 2022-06-18]
Designs/Tuesday10 05 2022/Backup of bigger_cap3.SLDPRT
90.0 x 86.5 x 90.0 mm
