Benedict-Bsl/SmartCap/Designs/Tuesday10 05 2022/stl/loCK_WithThin_for_biggerCapB.STL

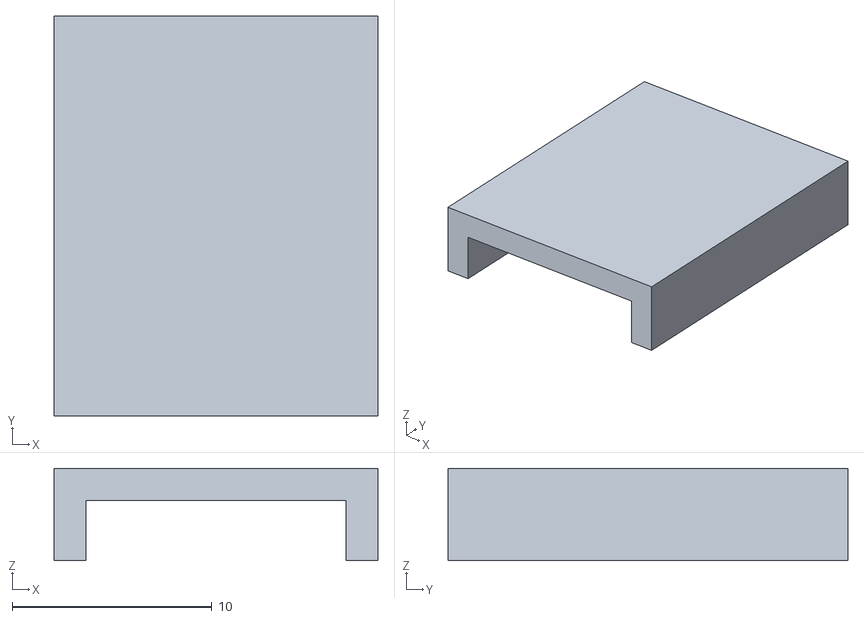
[picture p216: CAD file, 2022-05-22]
Designs/Tuesday10 05 2022/stl/loCK_WithThin_for_biggerCapB.STL
16.2 x 20.0 x 4.60
