Benedict-Bsl/SmartCap/Misceleanous/magnet.SLDPRT

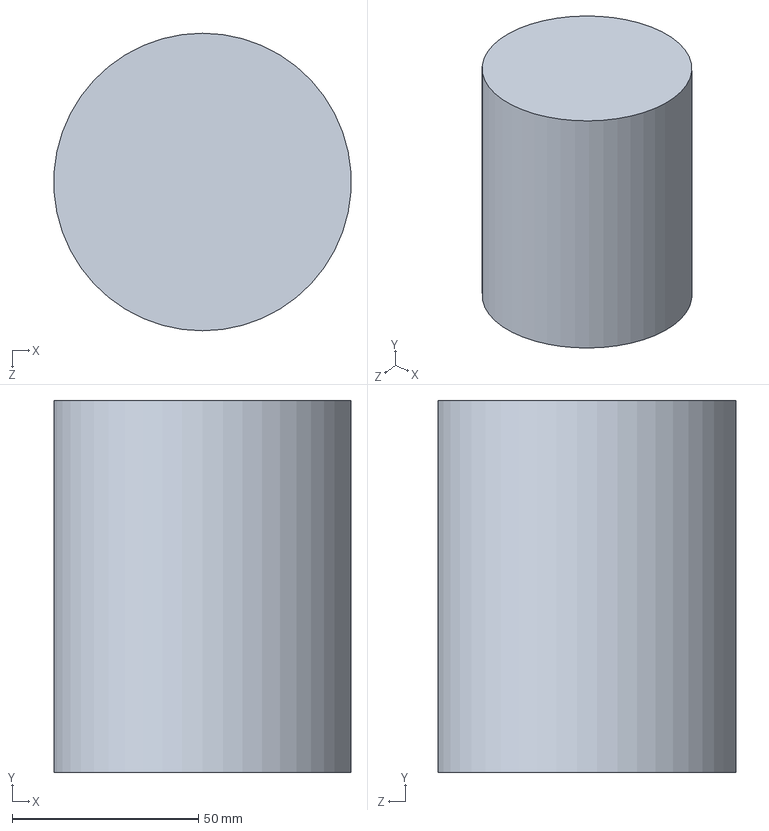
[picture p217: CAD file, 2022-03-13]
Misceleanous/magnet.SLDPRT
79.8 x 100.0 x 80.0 mm
