Benedict-Bsl/SmartCap/Designs/Designs/Locking/Backup (6) of Top_LockMechan_CupVersion4D6_withLocksM_2_fp&mt.SLDPRT

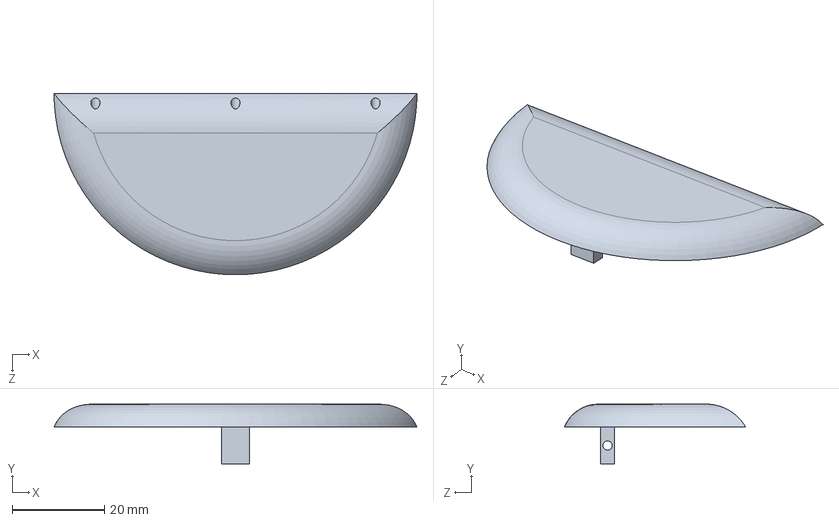
[picture p218: CAD file, 2022-04-26]
Designs/Designs/Locking/Backup (6) of Top_LockMechan_CupVersion4D6_withLocksM_2_fp&mt.SLDPRT
78.8 x 13.0 x 39.4 mm
