Benedict-Bsl/SmartCap/Designs/Designs/Locking/New/holder of rotation axis gear.SLDPRT

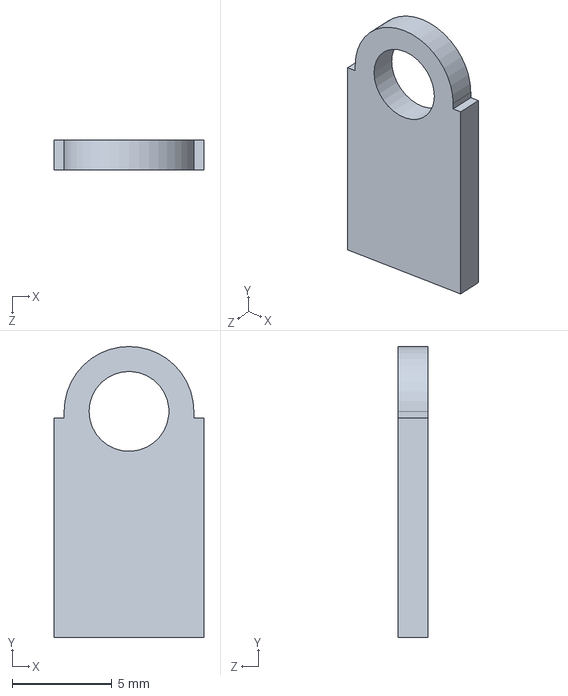
[picture p219: CAD file, 2022-04-26]
Designs/Designs/Locking/New/holder of rotation axis gear.SLDPRT
7.50 x 14.6 x 1.50 mm
