Benedict-Bsl/SmartCap/Designs/Designs/New cap Design/FingerPrint_part_CapDesign_Version2.SLDPRT

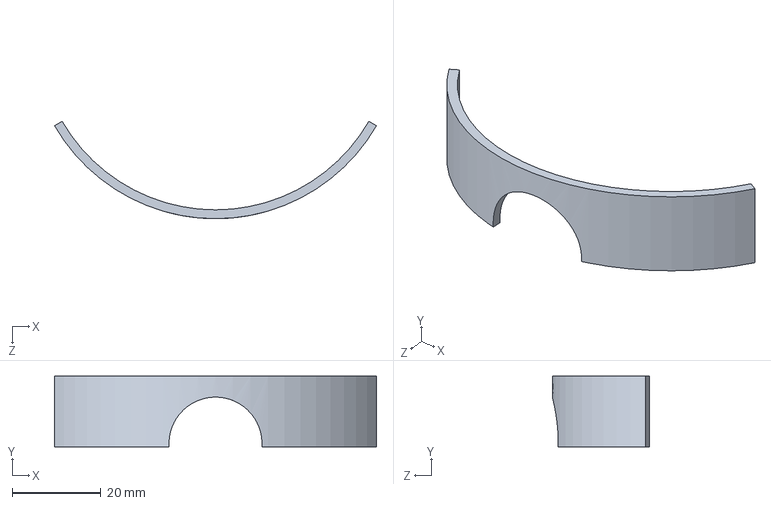
[picture p220: CAD file, 2022-04-26]
Designs/Designs/New cap Design/FingerPrint_part_CapDesign_Version2.SLDPRT
72.7 x 16.0 x 22.0 mm
