Benedict-Bsl/SmartCap/Designs/Designs/STL files/FingerPrint_CapDesign_Version2.STL

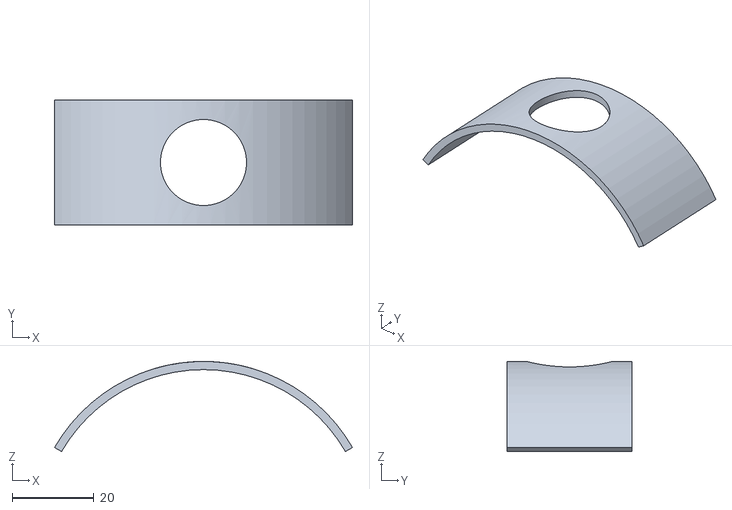
[picture p221: CAD file, 2022-04-26]
Designs/Designs/STL files/FingerPrint_CapDesign_Version2.STL
72.7 x 30.5 x 22.0
