Benedict-Bsl/SmartCap/Designs/Designs/STL files/New/retractable2_Vd.SLDPRT

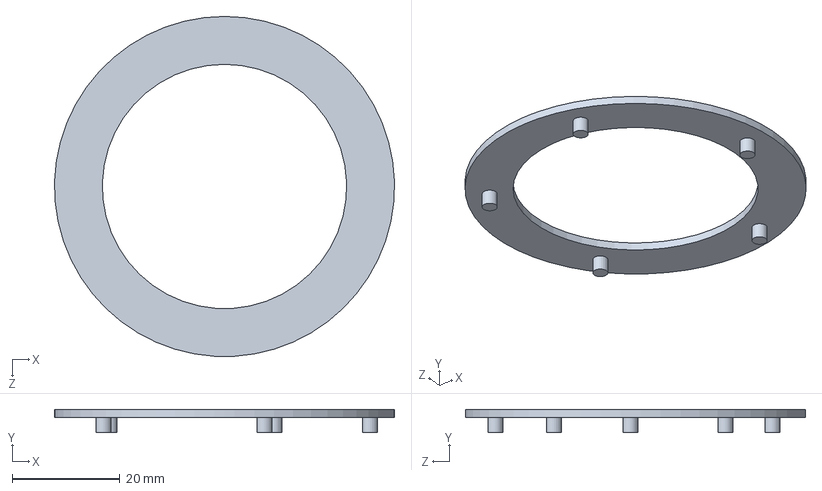
[picture p222: CAD file, 2022-04-26]
Designs/Designs/STL files/New/retractable2_Vd.SLDPRT
63.0 x 4.30 x 63.0 mm
