Benedict-Bsl/SmartCap/Designs/Designs/Thursday 13 04 2022/STL/Backup (1) of a.SLDPRT

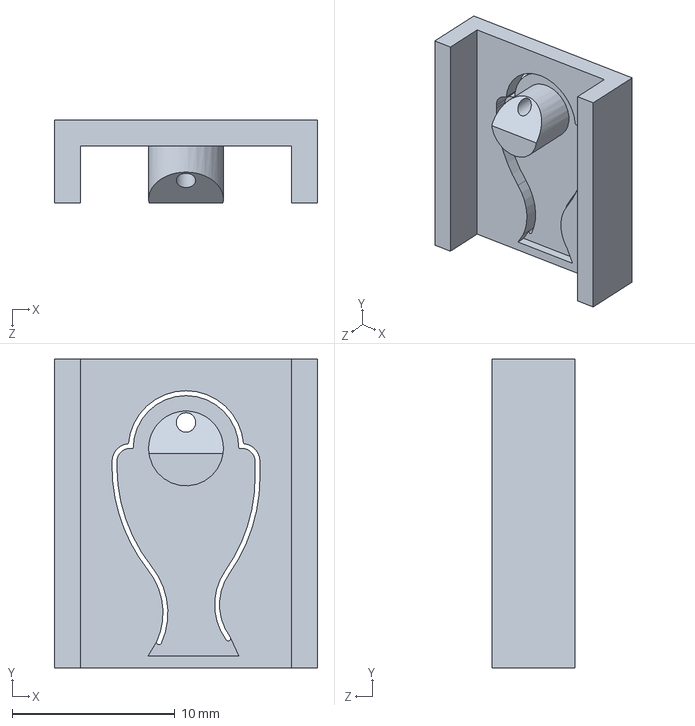
[picture p223: CAD file, 2022-04-26]
Designs/Designs/Thursday 13 04 2022/STL/Backup (1) of a.SLDPRT
16.2 x 19.0 x 5.10 mm
