Benedict-Bsl/SmartCap/Circuitry/FewCopper_TrackRX_PCB.PDF

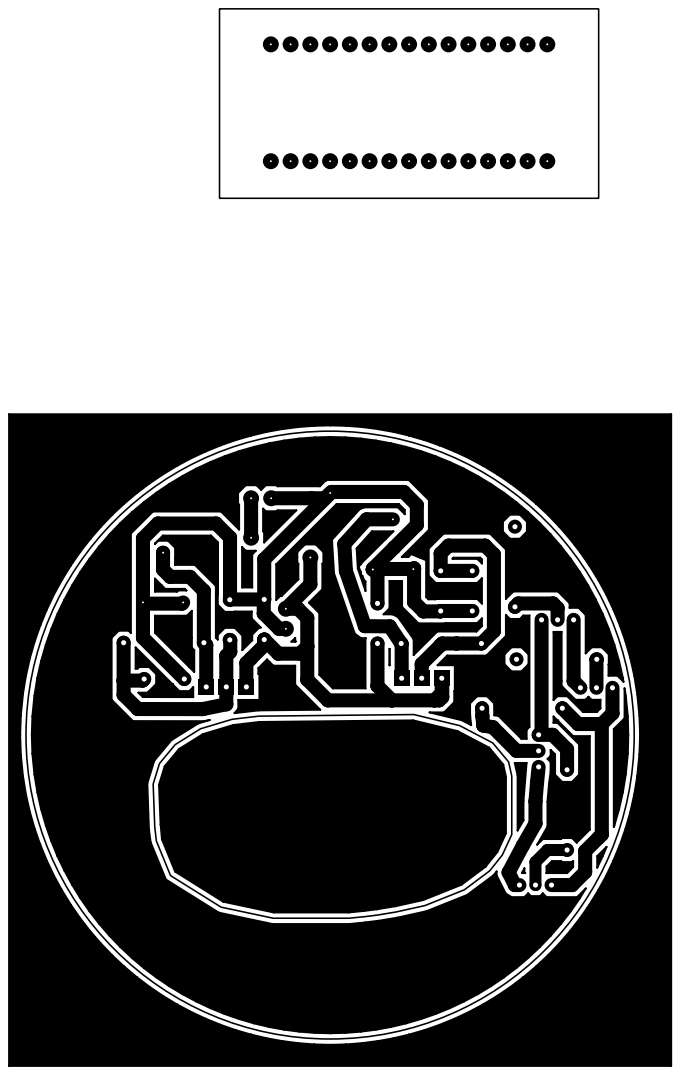
[picture p264: page 1]
