Benedict-Bsl/SmartCap/Circuitry/TrackRX_PCB.PDF

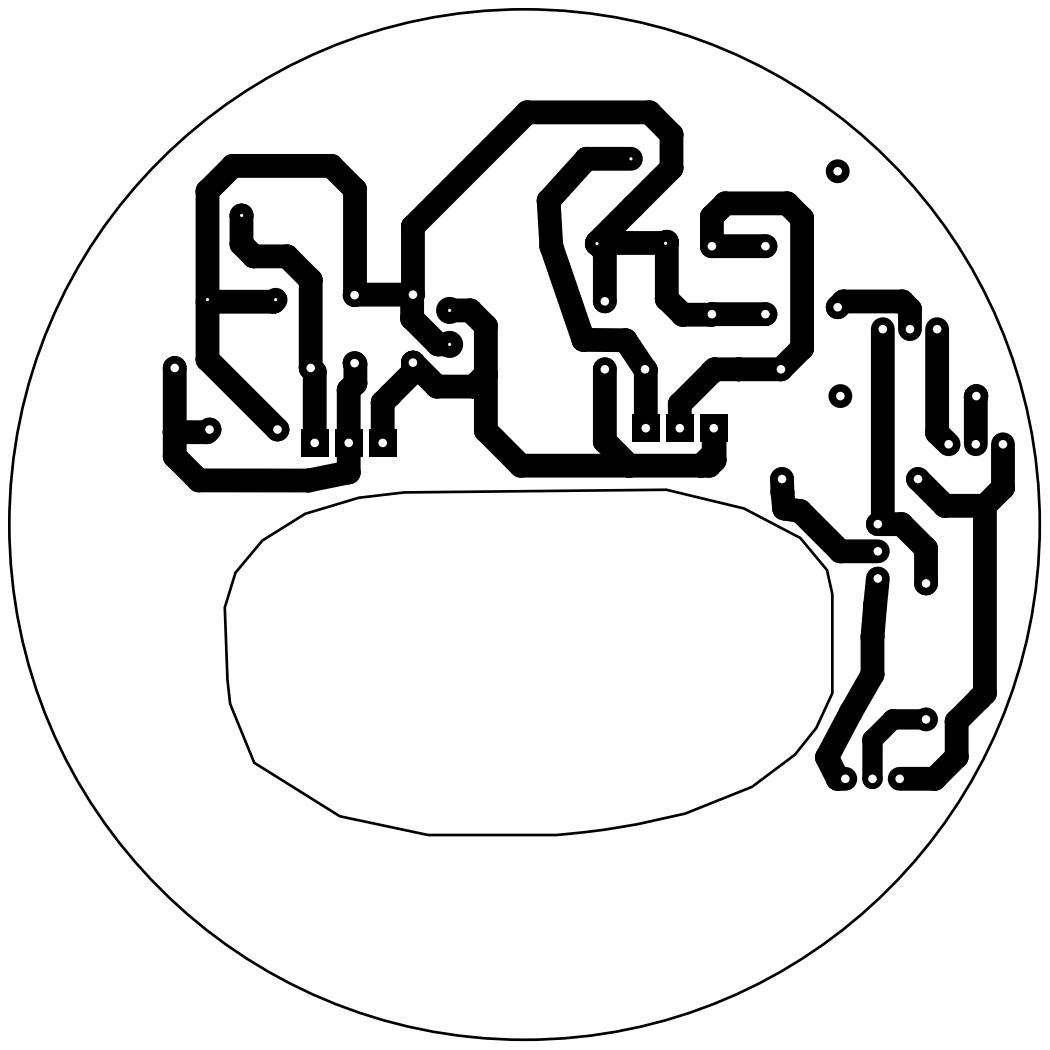
[picture p265: page 1]
