Benedict-Bsl/SmartCap/Circuitry/TrackRX_PCB3_Content_info.PDF

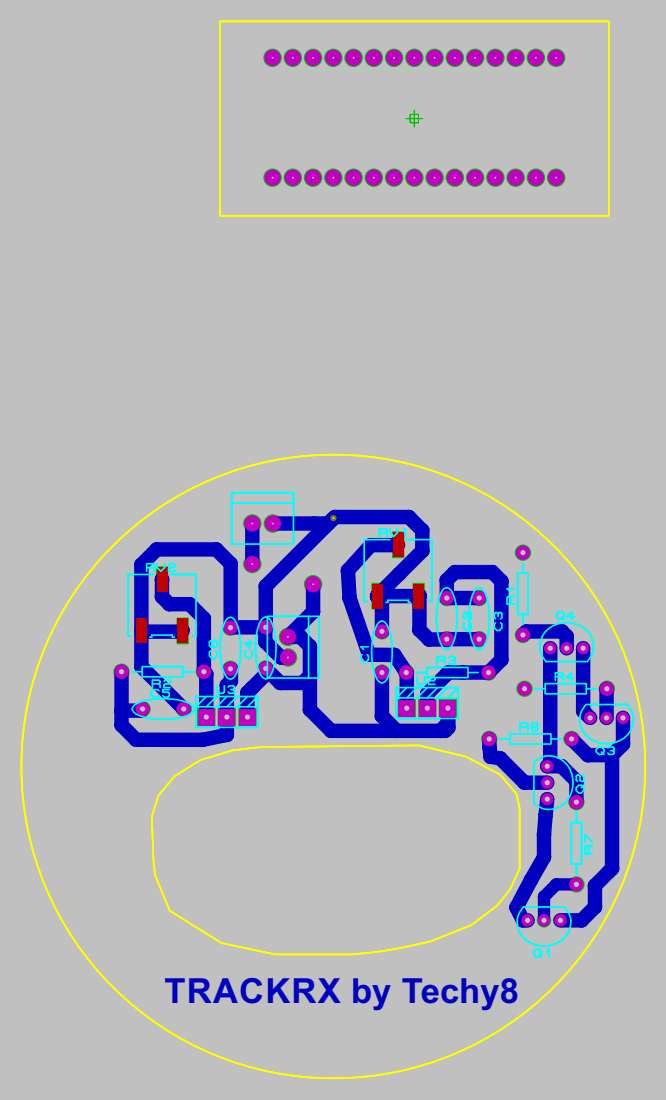
[picture p266: page 1]
