Benedict-Bsl/SmartCap/Circuitry/PCB-ver2_3.PDF

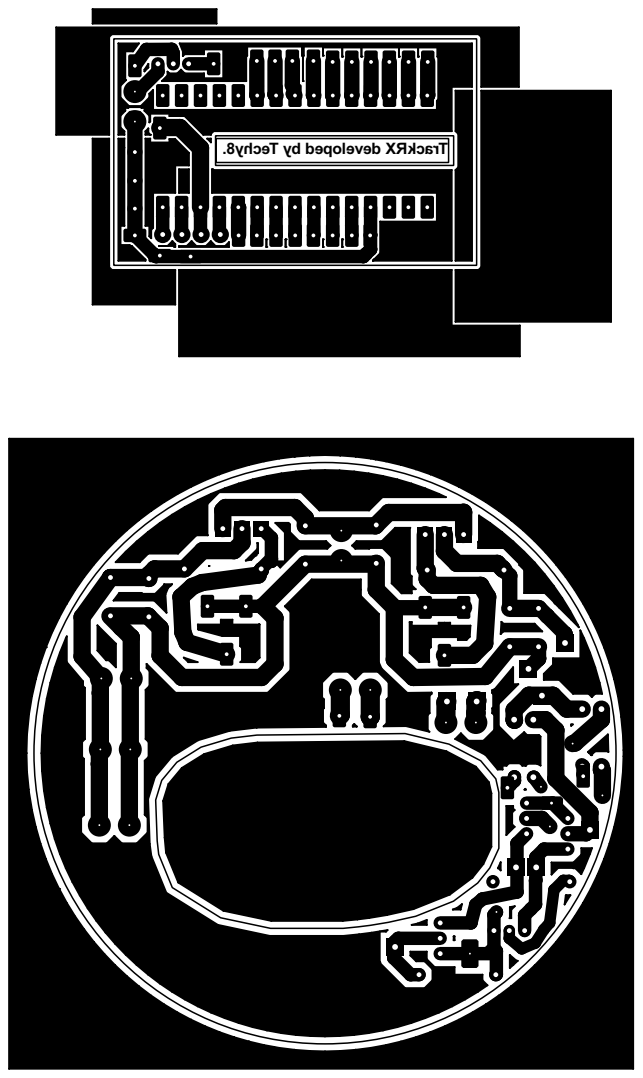
[picture p267: page 1]

. 8yhceT yb depol eved XRkcar T
