Benedict-Bsl/SmartCap/Circuitry/PCB.PDF

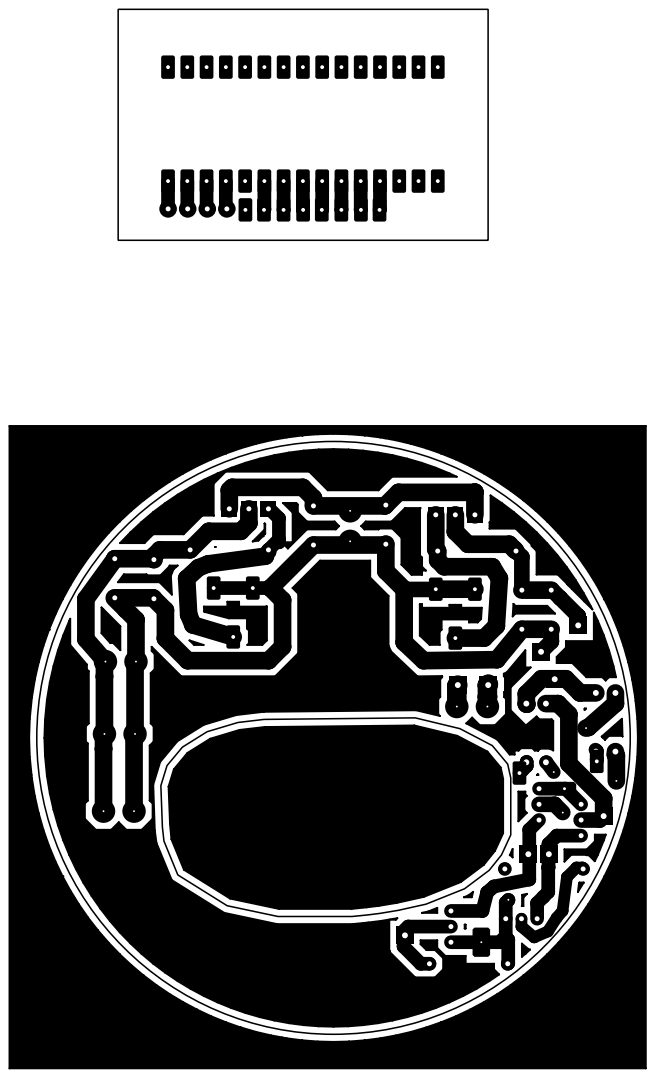
[picture p268: page 1]
