Benedict-Bsl/SmartCap/Circuitry/PCB_verbose.PDF

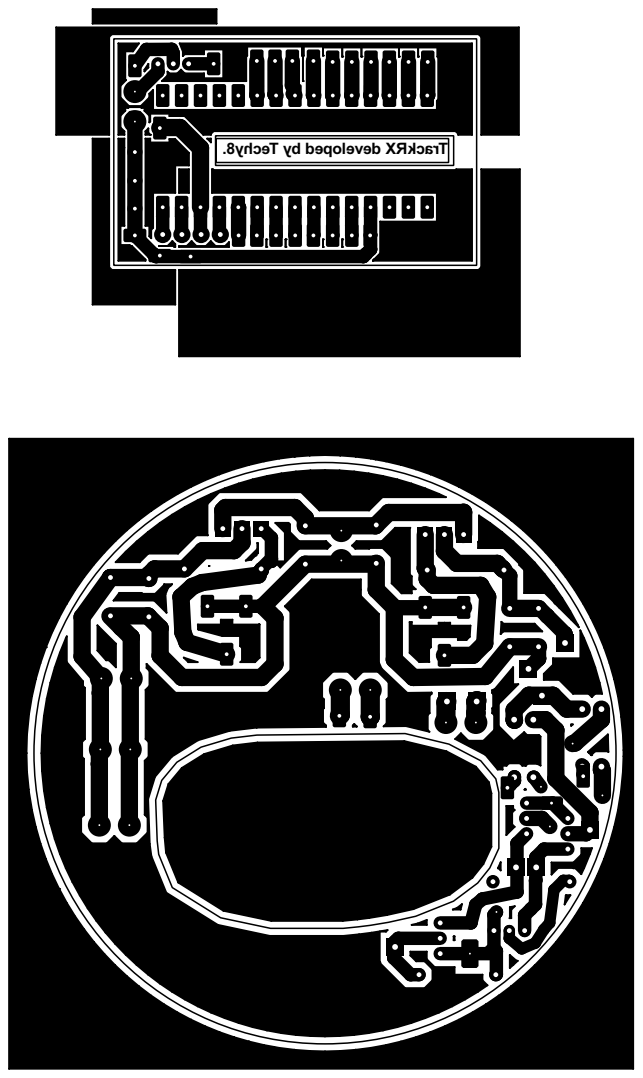
[picture p269: page 1]

. 8yhceT yb depol eved XRkcar T
