Benedict-Bsl/SmartCap/Circuitry/TrackRX_PCB3.PDF

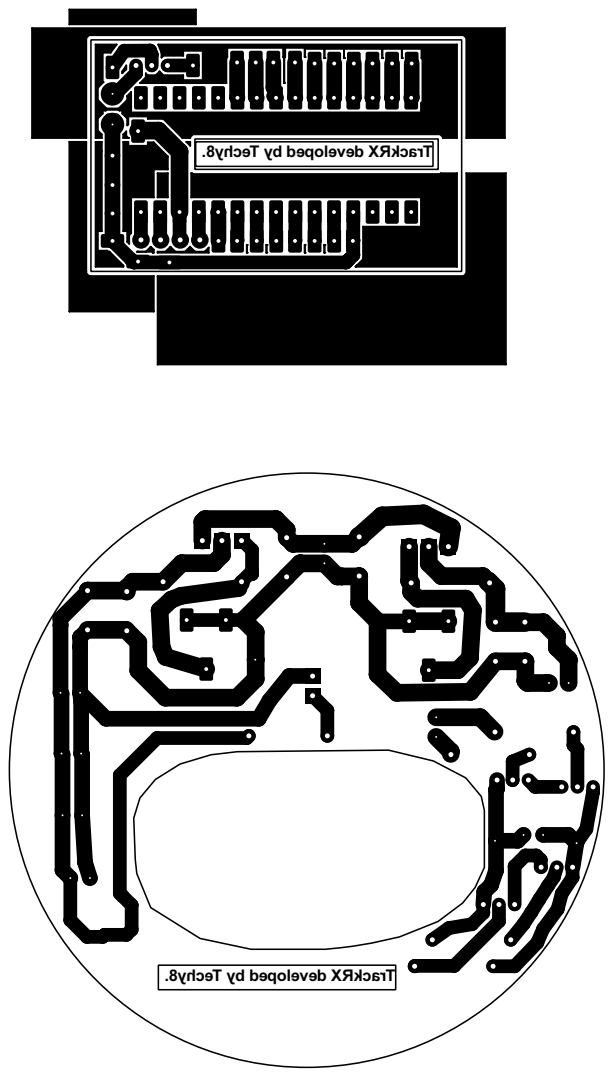
[picture p270: page 1]

. 8yhceT yb depol eved XRkcar T
