Benedict-Bsl/SmartCap/Circuitry/TrackRX_PCB3_covered.PDF

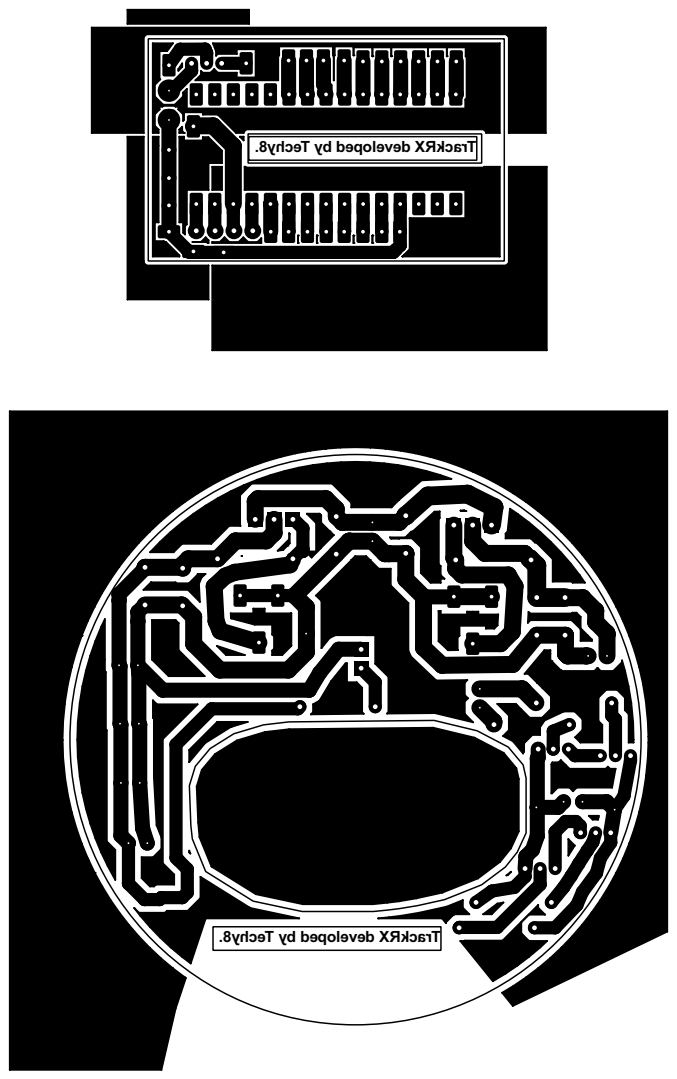
[picture p271: page 1]

. 8yhceT yb depol eved XRkcar T
