Benedict-Bsl/SmartCap/Circuitry/PCB-ver2.PDF

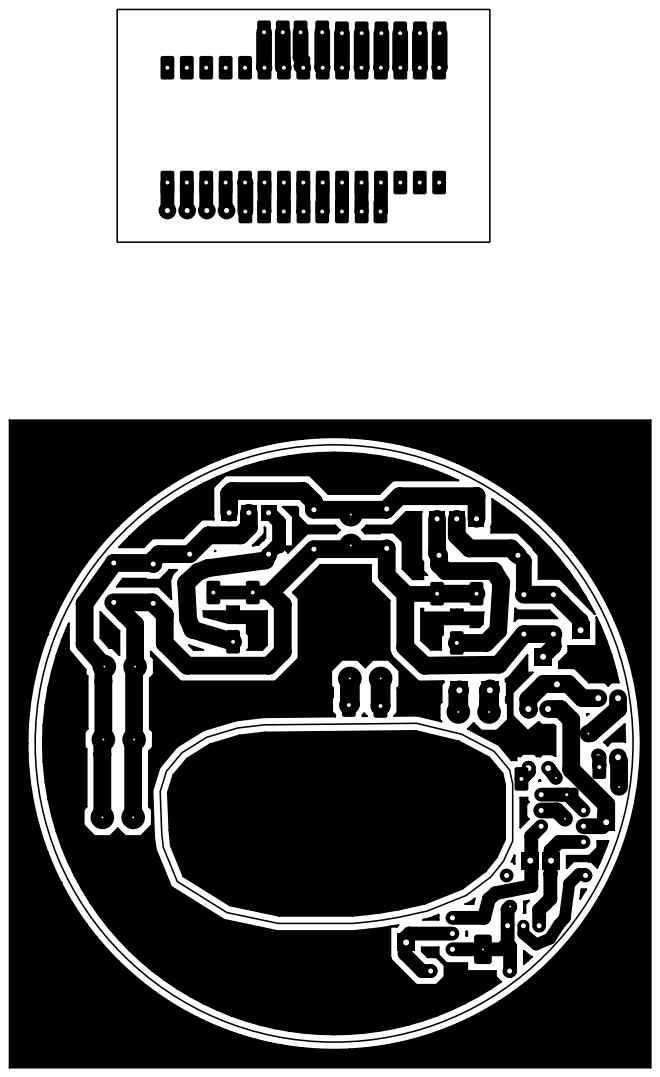
[picture p272: page 1]
