Benedict-Bsl/SmartCap/FirmWare/TrackRXProgram/src/SIM800L.h

/********************************************************************************
 * Arduino-SIM800L-driver                                                       *
 * ----------------------                                                       *
 * Arduino driver for GSM/GPRS module SIMCom SIM800L to make HTTP/S connections *
 * with GET and POST methods                                                    *
 * Author: Olivier Staquet                                                      *
 * Last version available on https://github.com/ostaquet/Arduino-SIM800L-driver *
 ********************************************************************************
 * MIT License
 *
 * Copyright (c) 2019 Olivier Staquet
 *
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
 * THE SOFTWARE IS PROVIDED "AS IS", WITHOUT WARRANTY OF ANY KIND, EXPRESS OR
 * IMPLIED, INCLUDING BUT NOT LIMITED TO THE WARRANTIES OF MERCHANTABILITY,
 * FITNESS FOR A PARTICULAR PURPOSE AND NONINFRINGEMENT. IN NO EVENT SHALL THE
 * AUTHORS OR COPYRIGHT HOLDERS BE LIABLE FOR ANY CLAIM, DAMAGES OR OTHER
 * LIABILITY, WHETHER IN AN ACTION OF CONTRACT, TORT OR OTHERWISE, ARISING FROM,
 * OUT OF OR IN CONNECTION WITH THE SOFTWARE OR THE USE OR OTHER DEALINGS IN THE
 * SOFTWARE.
 *******************************************************************************/
#ifndef _SIM800L_H_
#define _SIM800L_H_

#include <Arduino.h>

#define DEFAULT_TIMEOUT 5000
#define RESET_PIN_NOT_USED -1

enum PowerMode {MINIMUM, NORMAL, POW_UNKNOWN, SLEEP, POW_ERROR};
enum NetworkRegistration {NOT_REGISTERED, REGISTERED_HOME, SEARCHING, DENIED, NET_UNKNOWN, REGISTERED_ROAMING, NET_ERROR};

class SIM800L {
  public:
    // Initialize the driver
    // Parameters:
    //  _stream : Stream opened to the SIM800L module (Software or Hardware, usually 9600 bps)
    //  _pinRst (optional) : pin to the reset of the SIM800L module
    //  _internalBufferSize (optional): size in bytes of the internal buffer to handle general IO with the module
    //                        (including URL and maximum payload to send through POST method)
    //  _recvBufferSize (optional) : size in bytes of the reception buffer (max data to receive from GET or POST)
    //  _debugStream (optional) : Stream opened to the debug console (Software of Hardware)
    SIM800L(Stream* _stream, uint8_t _pinRst = RESET_PIN_NOT_USED, uint16_t _internalBufferSize = 128, uint16_t _recvBufferSize = 256);
    ~SIM800L();

    // Force a reset of the module
    void reset();

    // Status functions
    bool isReady();
    uint8_t getSignal();
    PowerMode getPowerMode();
    NetworkRegistration getRegistrationStatus();
    char* getVersion();
    char* getFirmware();
    char* getSimCardNumber();
    char* getSimStatus();
    char* getIP();

    // Troubleshooting functions: enable echo mode
    bool enableEchoMode();

    // Define PIN code to activate SIM card
    bool setPinCode(const char *pin);

    // Define the power mode (for parameter: see PowerMode enum)
    bool setPowerMode(PowerMode powerMode);

    // Enable/disable GPRS
    bool setupGPRS(const char *apn);
    bool setupGPRS(const char *apn, const char *user, const char *password);
    bool connectGPRS();
    bool isConnectedGPRS();
    bool disconnectGPRS();

    // HTTP methods
    uint16_t doGet(const char* url, uint16_t serverReadTimeoutMs);
    uint16_t doGet(const char* url, const char* headers, uint16_t serverReadTimeoutMs);
    uint16_t doPost(const char* url, const char* contentType, const char* payload, uint16_t clientWriteTimeoutMs, uint16_t serverReadTimeoutMs);
    uint16_t doPost(const char* url, const char* headers, const char* contentType, const char* payload, uint16_t clientWriteTimeoutMs, uint16_t serverReadTimeoutMs);

    // Obtain results after HTTP successful connections (size and buffer)
    uint16_t getDataSizeReceived();
    char* getDataReceived();

  protected:
    // Send command
    void sendCommand(const char* command);
    // Send comment from PROGMEM
    void sendCommand_P(const char* command);
    // Send command with parameter within quotes (template : command"parameter")
    void sendCommand(const char* command, const char* parameter);
    // Send command with parameter within quotes from PROGMEM (template : command"parameter")
    void sendCommand_P(const char* command, const char* parameter);

    // Read from module (timeout in millisec)
    bool readResponse(uint16_t timeout, uint8_t crlfToWait = 2);
    // Read from module and expect a specific answer defined in PROGMEM (timeout in millisec)
    bool readResponseCheckAnswer_P(uint16_t timeout, const char* expectedAnswer, uint8_t crlfToWait = 2);

    // Purge the serial
    void purgeSerial();

    // Find string in another string
    int16_t strIndex(const char* str, const char* findStr, uint16_t startIdx = 0);

    // Manage internal buffer
    void initInternalBuffer();
    void initRecvBuffer();

    // Manage HTTP/S connection
    uint16_t initiateHTTP(const char* url, const char* headers);
    uint16_t readHTTP(uint16_t serverReadTimeoutMs);

  private:
    // Serial line with SIM800L
    Stream* stream = NULL;

    // Serial console for the debug
    Stream* debugStream;

    // Details about the circuit: pins
    uint8_t pinReset = 0;

    // Internal memory for the shared buffer
    // Used for all reception of message from the module
    char *internalBuffer;
    uint16_t internalBufferSize = 0;

    // Reception buffer
    char *recvBuffer;
    uint16_t recvBufferSize = 0;
    uint16_t dataSize = 0;

    // Enable debug mode
    bool enableDebug = true;
};

#endif // _SIM800L_H_
